hudsonburke/SandsOfTime/Hardware/CAD/Clock/Rack and Pinion Arm/Inside_Channel/Inside_Channel_Acrylic_Assem.SLDASM

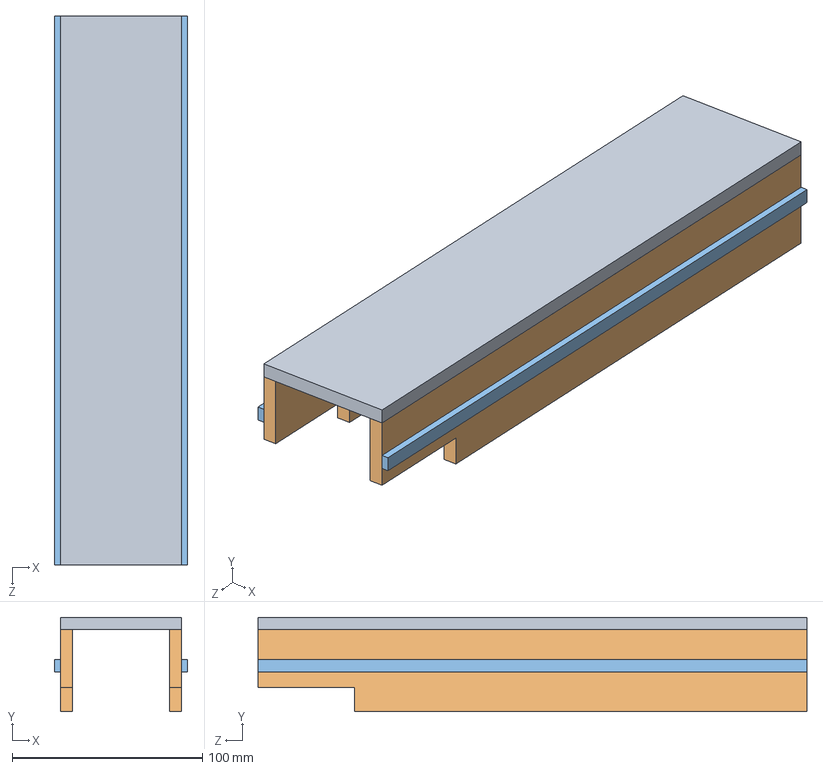
[picture p34: CAD file, 2023-07-05]
Hardware/CAD/Clock/Rack and Pinion Arm/Inside_Channel/Inside_Channel_Acrylic_Assem.SLDASM
69.8 x 49.5 x 288.3 mm
Top
Vert_Outer x 2
Slide x 2
