hudsonburke/SandsOfTime/PriorWork/Solidworks/Solidworks/HG_Assembly/HG_Assembly_4.SLDASM

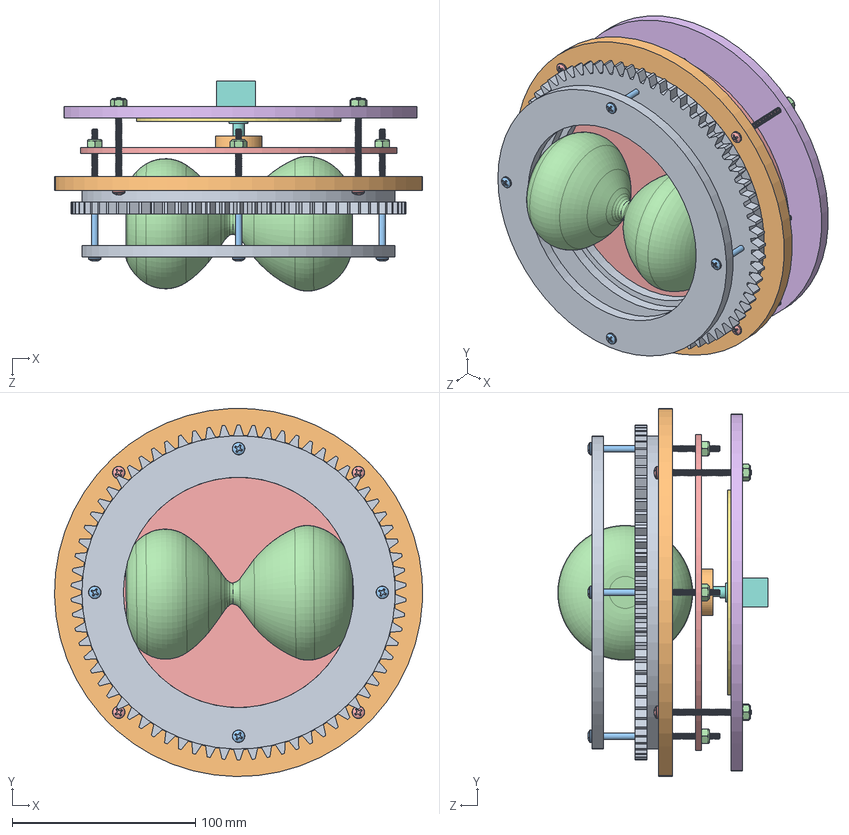
[picture p35: CAD file, 2023-07-05]
PriorWork/Solidworks/Solidworks/HG_Assembly/HG_Assembly_4.SLDASM
200.9 x 200.9 x 114.8 mm
Hourglass_holder_Plate_2 x 2
Outer_Ring_LS
Inner_Ring_LS
Hourglass
Diffuser
Encoder_Plate
LED_ring
Encoder (1)
HG_Gear
Encoder_mount
6_32_2.75_inch x 4
Nylon_Insert_Nut x 8
6_32_2_inch x 4
