hudsonburke/SandsOfTime/Hardware/CAD/Clock/Frame_with_HG_Assembly.SLDASM

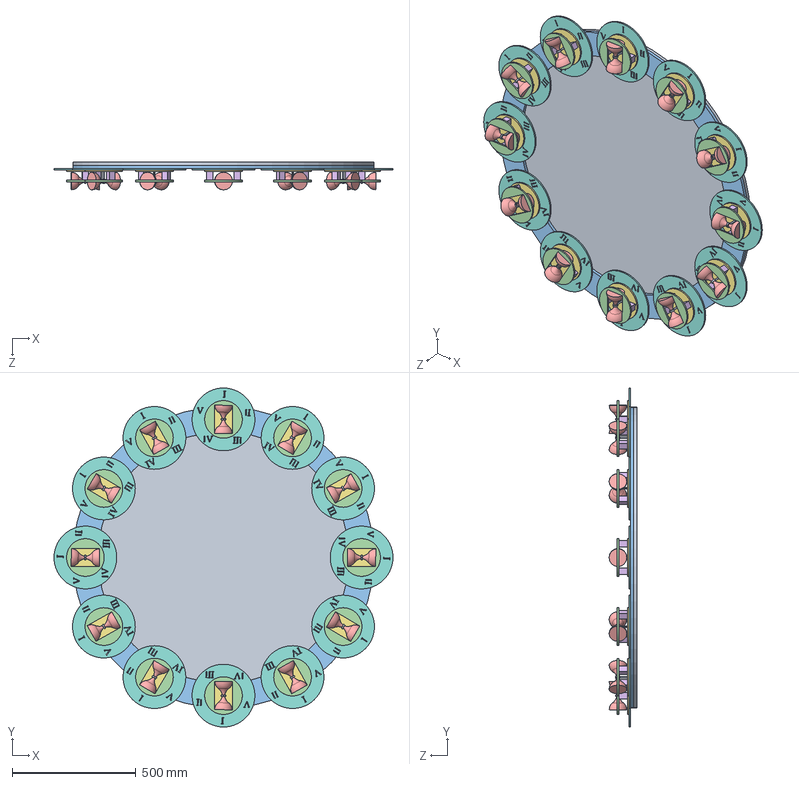
[picture p36: CAD file, 2023-07-05]
Hardware/CAD/Clock/Frame_with_HG_Assembly.SLDASM
1371.6 x 1371.6 x 111.7 mm
Clock_Back
Bearing x 12
Clock_Frame
Hourglass_Plate x 12
Hourglass x 12
Flick_Standoff x 24
Flick_Spacer x 12
Number_Plate x 12
Holder x 24
