hudsonburke/SandsOfTime/Hardware/CAD/Clock/Rack and Pinion Arm/Bearing.SLDASM

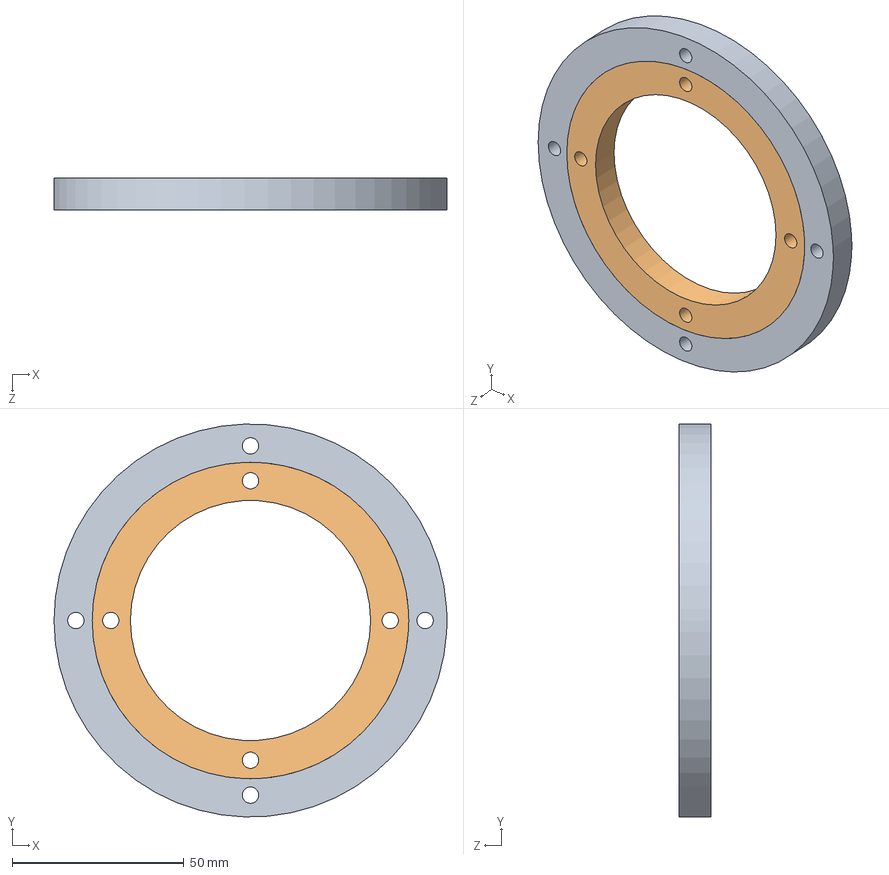
[picture p37: CAD file, 2023-07-05]
Hardware/CAD/Clock/Rack and Pinion Arm/Bearing.SLDASM
114.3 x 114.2 x 9.17 mm
Outside_Ring
Inside_Ring
