hudsonburke/SandsOfTime/Hardware/CAD/Clock/Arm/Arm_Mechanism.SLDASM

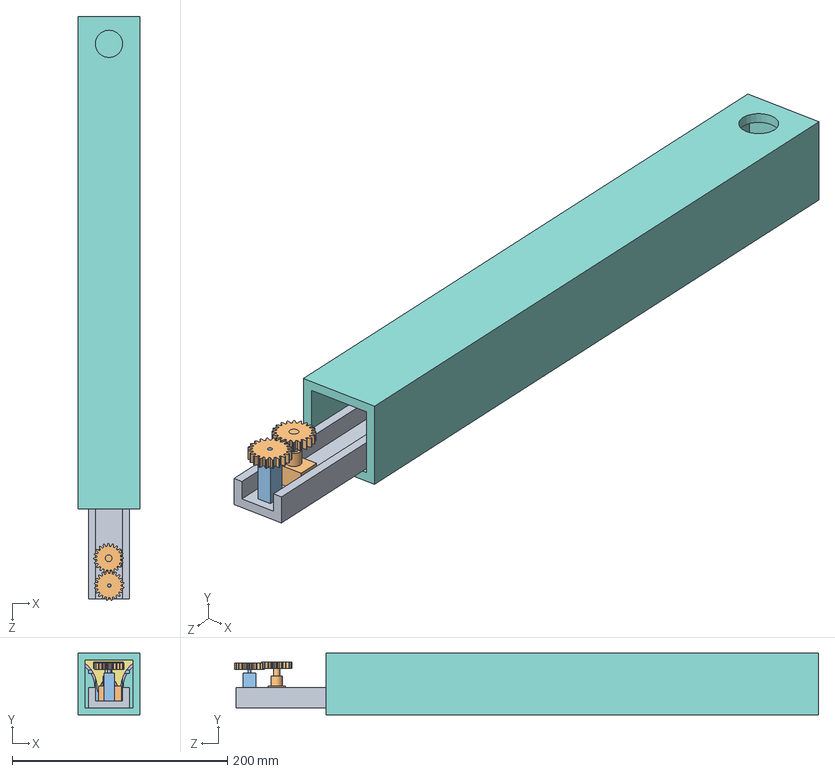
[picture p38: CAD file, 2023-07-05]
Hardware/CAD/Clock/Arm/Arm_Mechanism.SLDASM
57.1 x 57.1 x 542.3 mm
U_Channel
Encoder
Small_Motor
Lead_Nut
Lead_Screw
Bearing_Lead_Screw
Bearing_Holder
Outer Arm
Lead_Screw_Motor
spur gear_ai x 2
Lead_Nut_Holder
Lin_Bearing_Track
Lin_Bearing_Mount
Motor_Holder
