hudsonburke/SandsOfTime/Hardware/CAD/Clock/Open Back/Second_Arm_SubAssembly.SLDASM

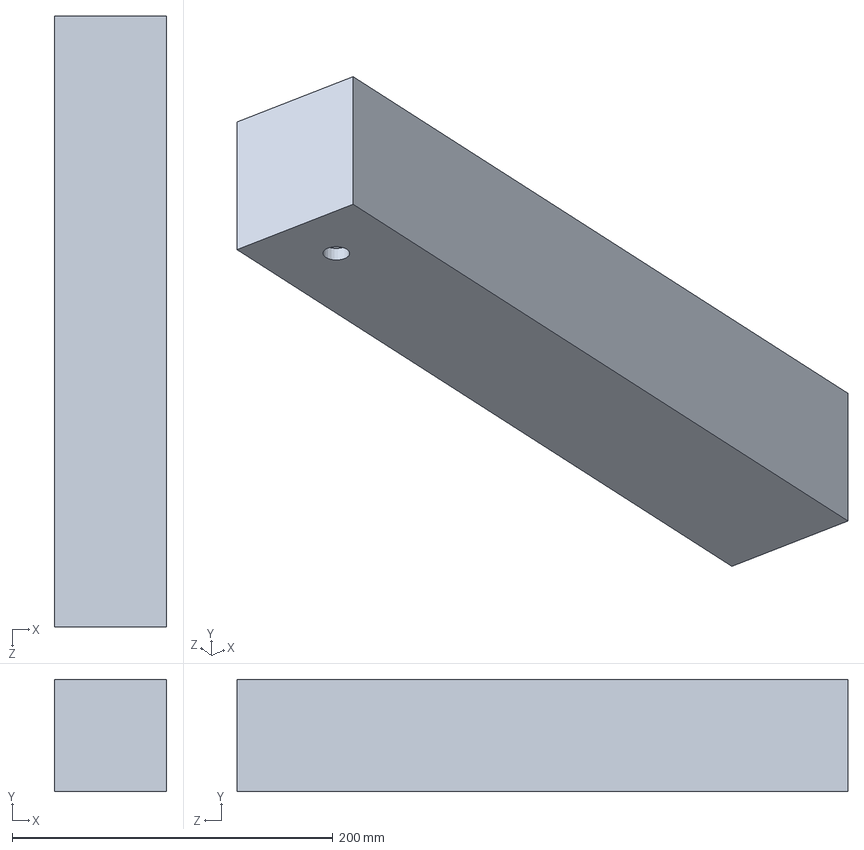
[picture p39: CAD file, 2023-07-05]
Hardware/CAD/Clock/Open Back/Second_Arm_SubAssembly.SLDASM
69.8 x 69.8 x 381.0 mm
Arm1
Linear_Actuator
Arm2
spur gear_ai
