hudsonburke/SandsOfTime/Hardware/CAD/Clock/R and P Arm DC Brush/HG Assembly 10-9/New Version of Assembly 10-9/HG_Assembly_3.SLDASM

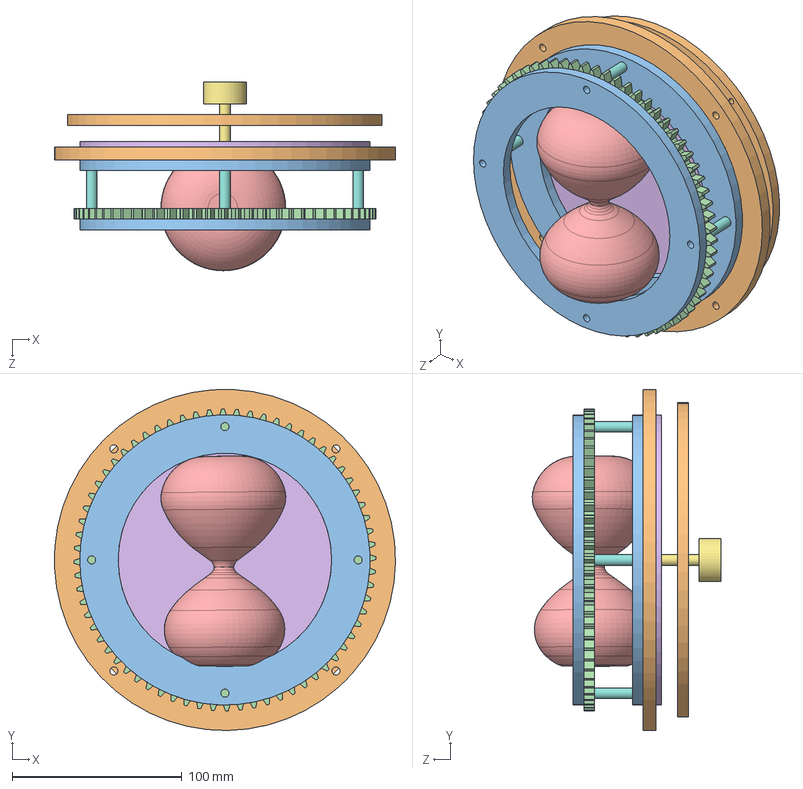
[picture p40: CAD file, 2023-07-05]
Hardware/CAD/Clock/R and P Arm DC Brush/HG Assembly 10-9/New Version of Assembly 10-9/HG_Assembly_3.SLDASM
200.9 x 200.9 x 111.1 mm
Hourglass_Plate_2 x 2
Outer_Ring_LS
Inner_Ring_LS
spur gear_ai
Hourglass
Diffuser
Encoder
Standoff x 4
LED_ring
LED_spacer
