hudsonburke/SandsOfTime/Hardware/CAD/Clock/Rack and Pinion Arm/Inside_Slide.SLDASM

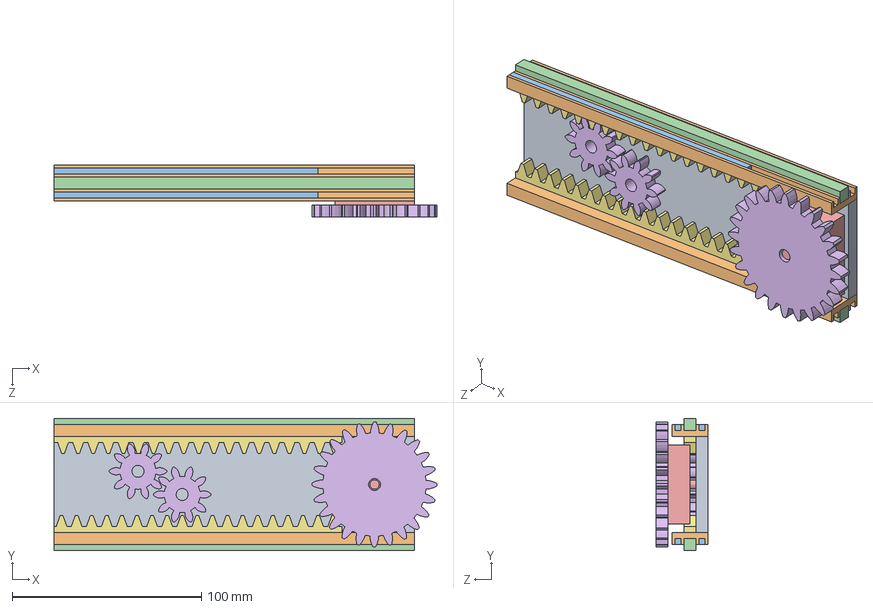
[picture p41: CAD file, 2023-07-05]
Hardware/CAD/Clock/Rack and Pinion Arm/Inside_Slide.SLDASM
202.5 x 69.8 x 27.5 mm
Inside_Bottom_Plate
Inside_Side_Plate x 2
Copper_Insert x 4
Teflon_Insert x 2
Pancake_Motor
spur gear_ai x 3
rack spur rectangular_ai x 2
