hudsonburke/SandsOfTime/Hardware/CAD/Clock/Open Back/Second_Clock_Assembly.SLDASM

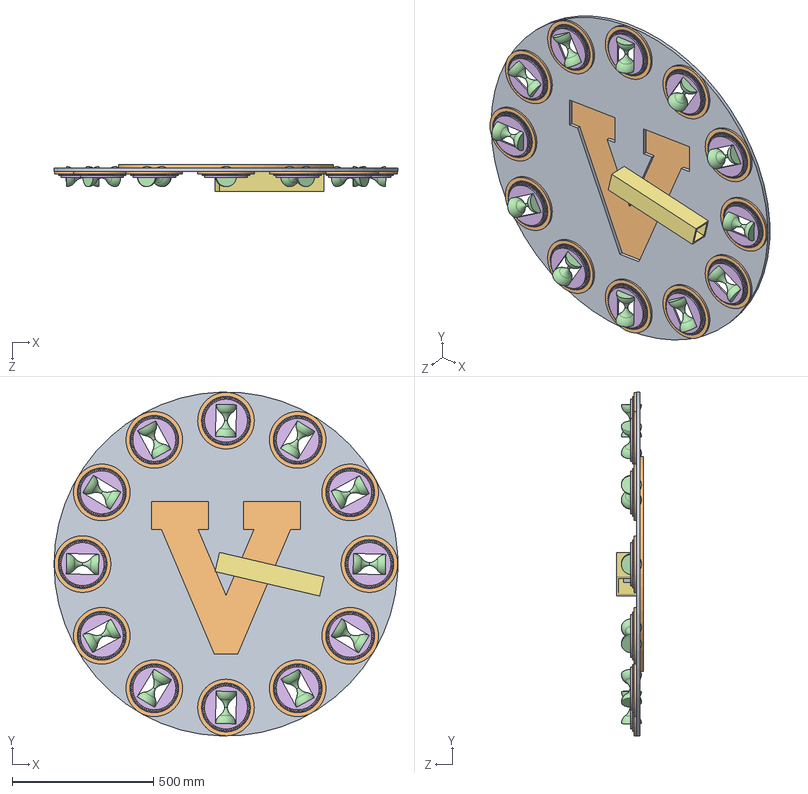
[picture p42: CAD file, 2023-07-05]
Hardware/CAD/Clock/Open Back/Second_Clock_Assembly.SLDASM
1219.2 x 1218.7 x 95.2 mm
Second_BackPlate
Outer_Ring x 12
Inner_Ring x 12
Hourglass x 12
spur gear_ai x 13
Hourglass_Plate x 12
Arm1
Linear_Actuator
Arm2
Back_Plate
