hudsonburke/SandsOfTime/Hardware/CAD/Clock/Hourglass_SubAssem.SLDASM

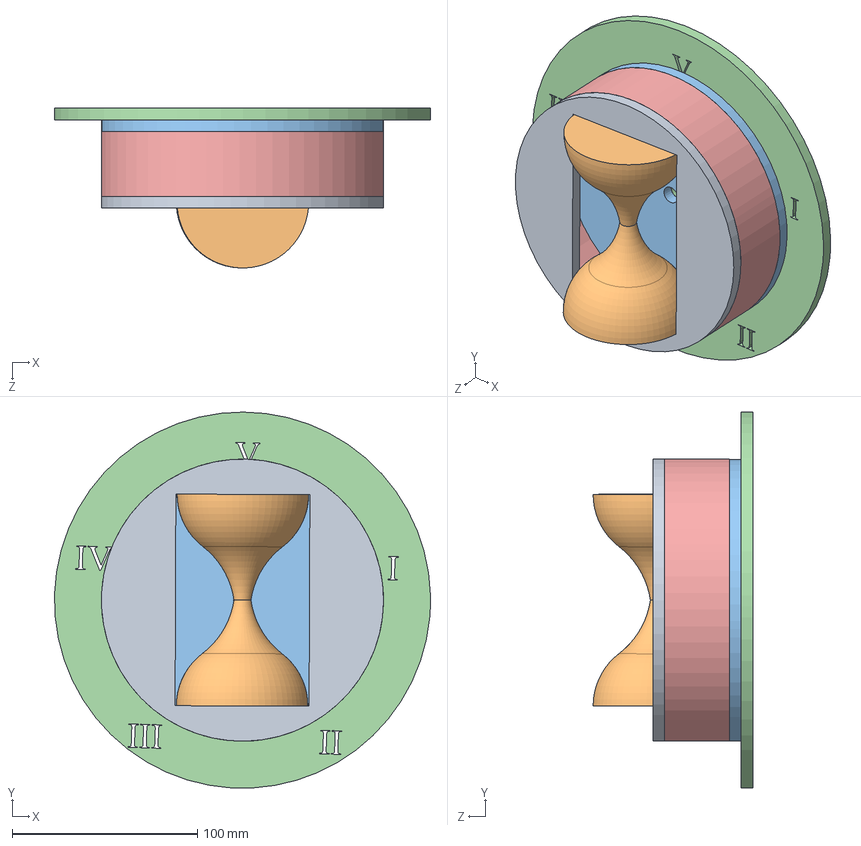
[picture p43: CAD file, 2023-07-05]
Hardware/CAD/Clock/Hourglass_SubAssem.SLDASM
203.1 x 203.0 x 86.3 mm
Hourglass_Plate
Hourglass
Flick_Spacer
Number_Plate
PVC_ring
