hudsonburke/SandsOfTime/Hardware/CAD/Clock/HG_Assembly_3.SLDASM

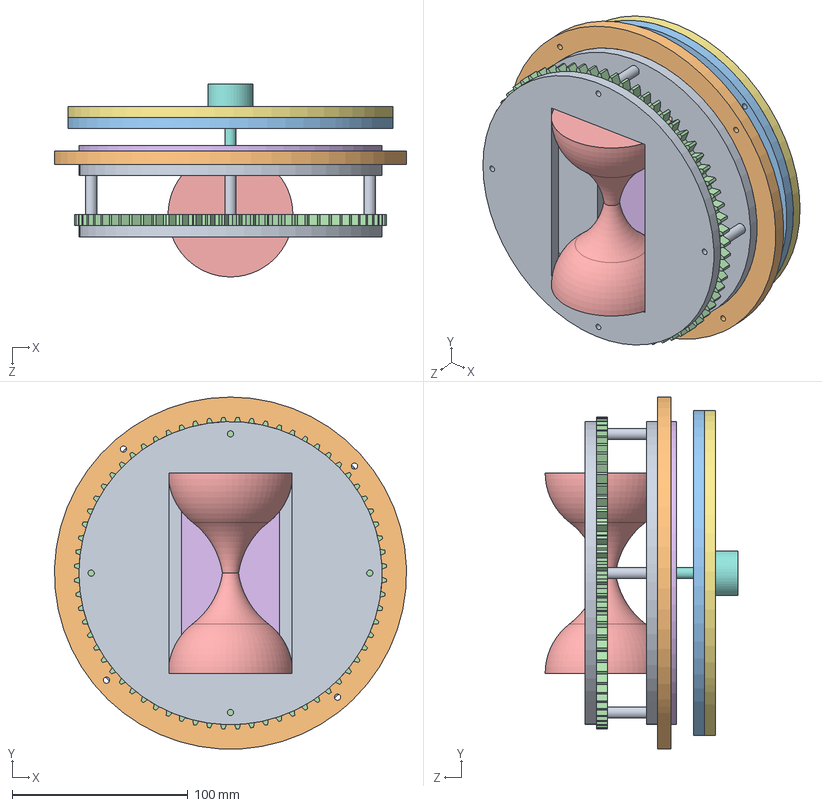
[picture p44: CAD file, 2023-07-05]
Hardware/CAD/Clock/HG_Assembly_3.SLDASM
200.6 x 200.5 x 109.8 mm
Hourglass_Plate_2 x 2
Outer_Ring
Inner_Ring
spur gear_ai
Hourglass
Diffuser
Back_Plate
Encoder
Standoff x 4
LED_ring
LED_spacer
