hudsonburke/SandsOfTime/Hardware/CAD/Clock/Clock_Assembly_4.SLDASM

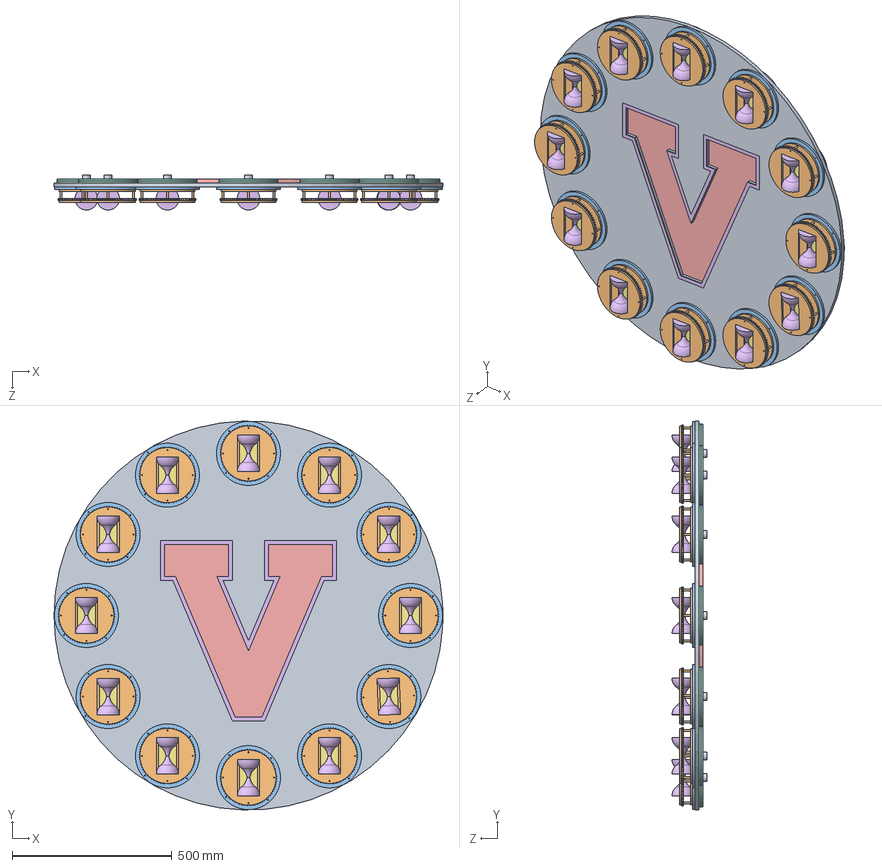
[picture p45: CAD file, 2023-07-05]
Hardware/CAD/Clock/Clock_Assembly_4.SLDASM
1219.2 x 1218.7 x 109.8 mm
Second_BackPlate
Hourglass_Plate_2 x 24
Outer_Ring x 12
Inner_Ring x 12
spur gear_ai x 12
Hourglass x 12
Diffuser x 12
Back_Plate x 12
Encoder x 12
Standoff x 48
LED_ring x 12
LED_spacer x 12
Back_Plate1
Alum_V
