hudsonburke/SandsOfTime/Hardware/CAD/Clock/Frame_Assembly.SLDASM

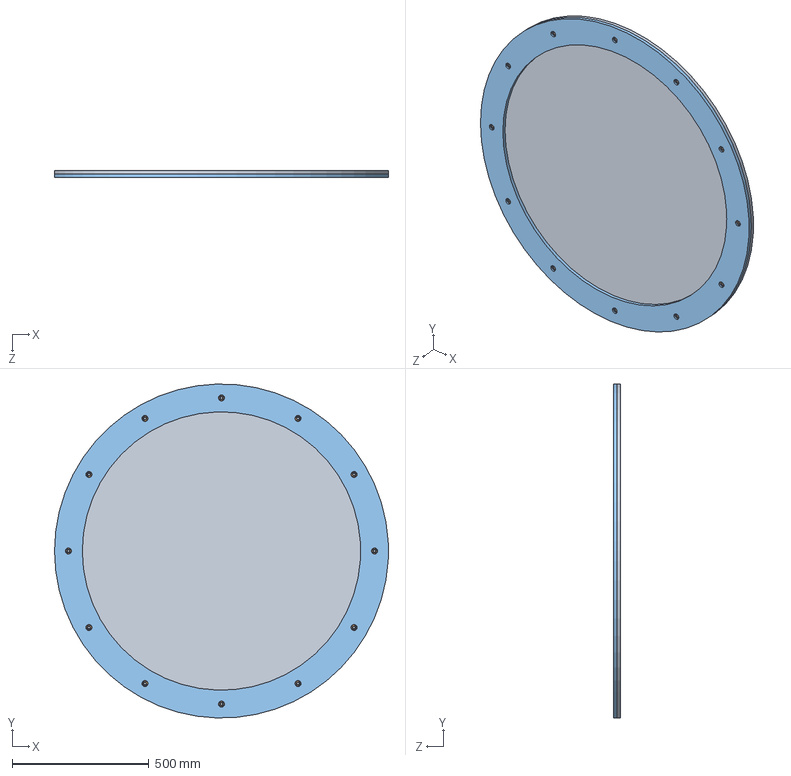
[picture p46: CAD file, 2023-07-05]
Hardware/CAD/Clock/Frame_Assembly.SLDASM
1219.2 x 1218.7 x 25.4 mm
Clock_Back
Bearing x 12
Clock_Frame
