hudsonburke/SandsOfTime/Hardware/CAD/Clock/R and P Arm DC Brush/Arm_Rotation_Assem.SLDASM

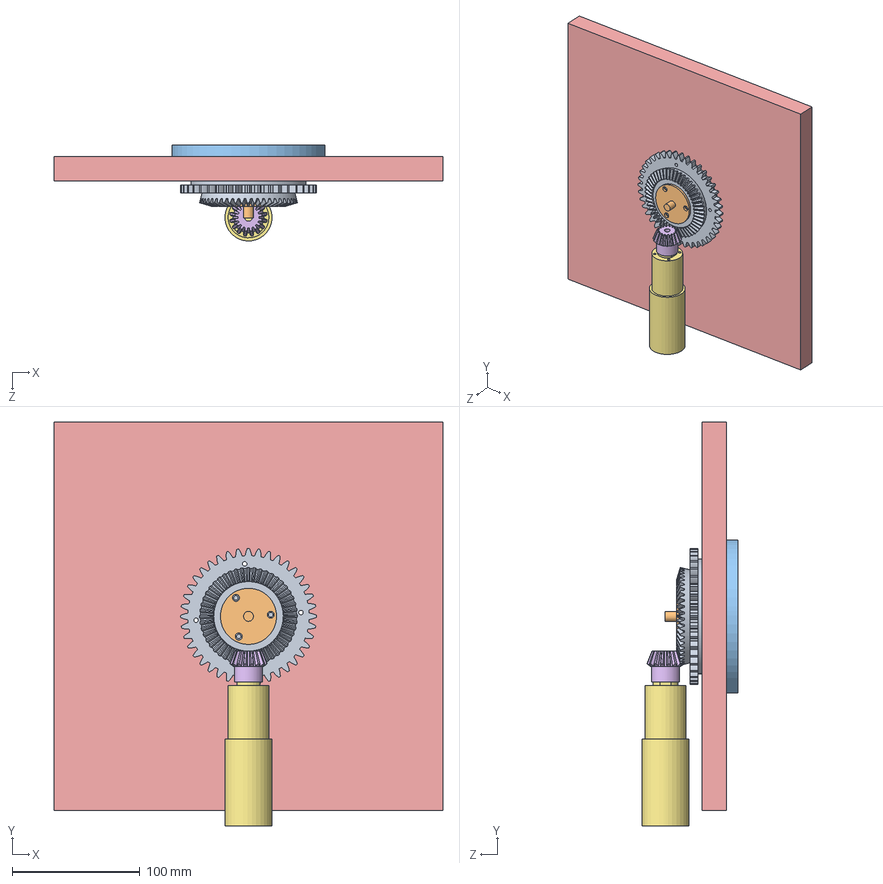
[picture p47: CAD file, 2023-07-05]
Hardware/CAD/Clock/R and P Arm DC Brush/Arm_Rotation_Assem.SLDASM
304.8 x 316.8 x 75.3 mm
Master_Center_Gear
Slip_Ring
Outside_Ring
Inside_Ring
Dummy_Backplate
Bevel_Gear_Motor
Drive_Motor
