hudsonburke/SandsOfTime/Hardware/CAD/Clock/R and P Arm DC Brush/Master_Drive_Gear.SLDASM

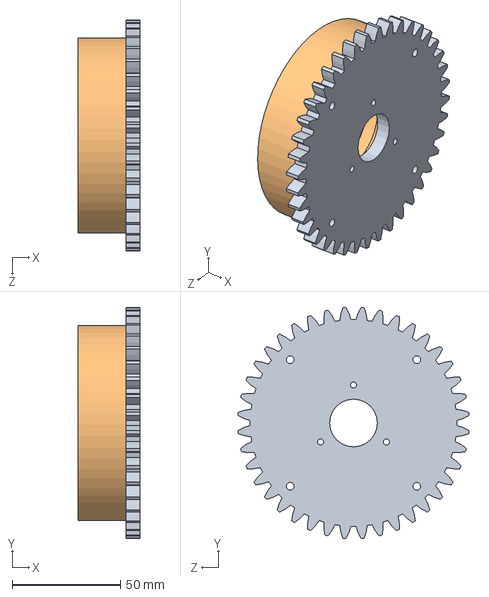
[picture p48: CAD file, 2023-07-05]
Hardware/CAD/Clock/R and P Arm DC Brush/Master_Drive_Gear.SLDASM
28.6 x 106.5 x 106.5 mm
Spur_Gear_Drive_Motor
Arm_Cup_Attachment
