hudsonburke/SandsOfTime/Hardware/CAD/Clock/Rack and Pinion Arm/Graphite_Brush.SLDASM

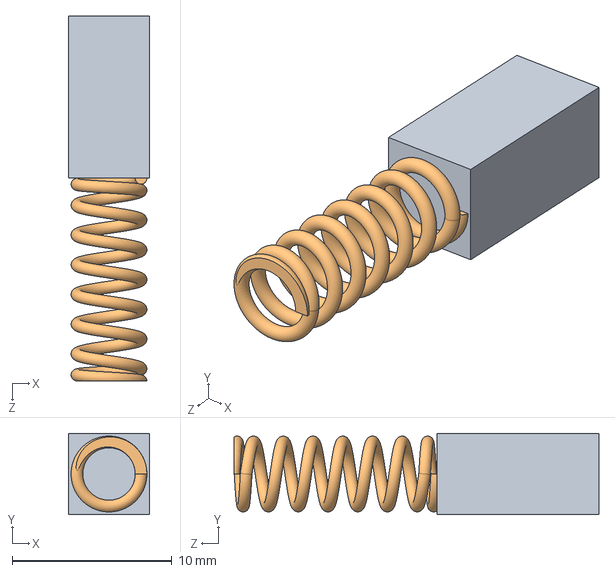
[picture p49: CAD file, 2023-07-05]
Hardware/CAD/Clock/Rack and Pinion Arm/Graphite_Brush.SLDASM
5.08 x 5.08 x 22.9 mm
Graphite
Graphite_Spring
