hudsonburke/SandsOfTime/Hardware/CAD/Clock/Arm/Lin_Bearing_Track.SLDPRT

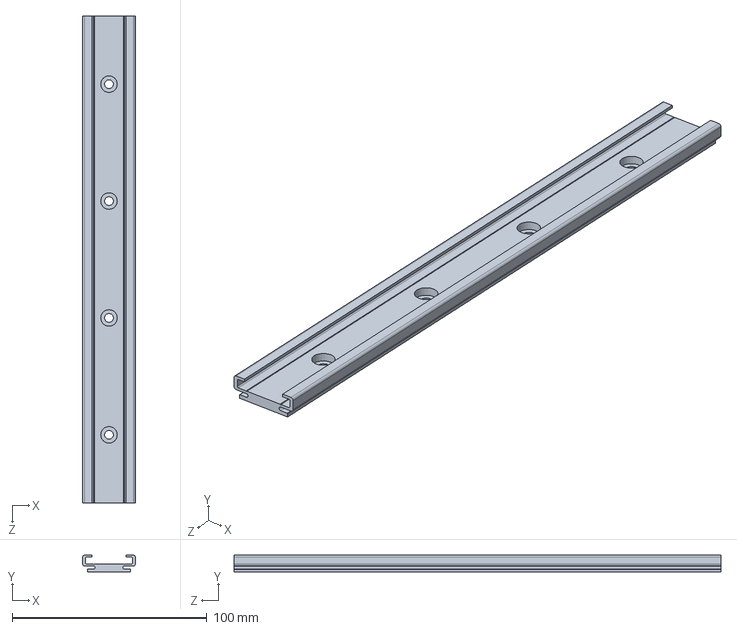
[picture p50: CAD file, 2023-07-05]
Hardware/CAD/Clock/Arm/Lin_Bearing_Track.SLDPRT
27.0 x 8.70 x 250.0 mm
