hudsonburke/SandsOfTime/Hardware/CAD/Clock/Open Back/Inner_Ring.SLDPRT

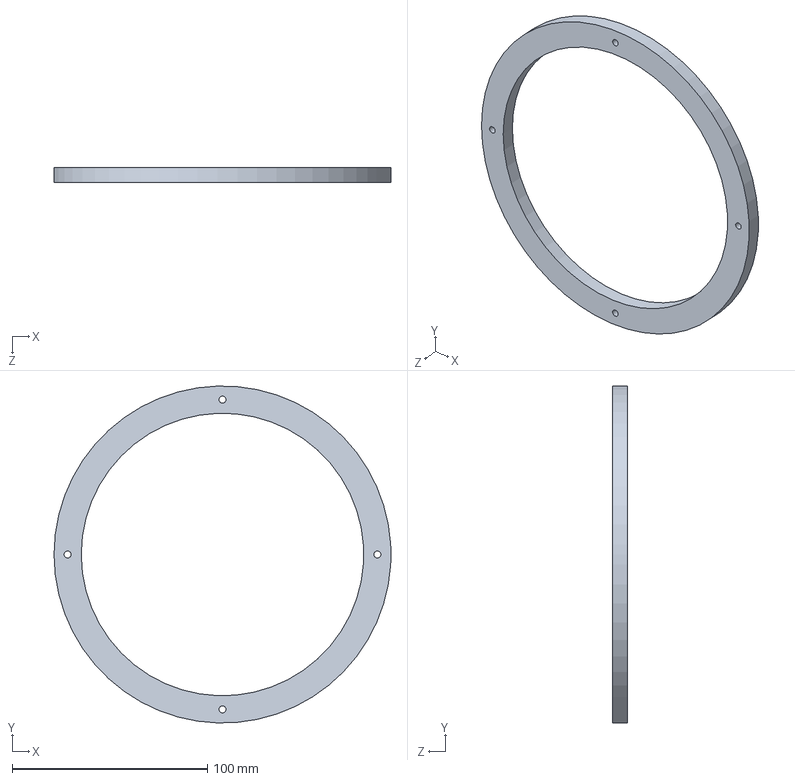
[picture p51: CAD file, 2023-07-05]
Hardware/CAD/Clock/Open Back/Inner_Ring.SLDPRT
172.7 x 172.6 x 7.62 mm
