hudsonburke/SandsOfTime/Hardware/CAD/Clock/R and P Arm DC Brush/HG Assembly 10-9/New Version of Assembly 10-9/Hourglass.SLDPRT

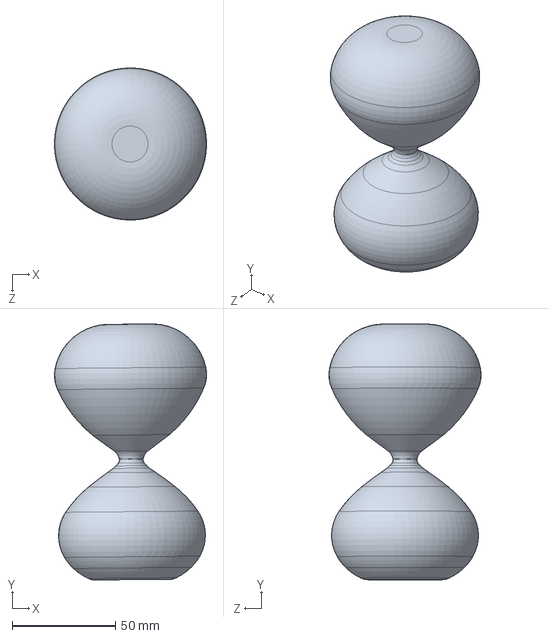
[picture p52: CAD file, 2026-04-15]
Hardware/CAD/Clock/R and P Arm DC Brush/HG Assembly 10-9/New Version of Assembly 10-9/Hourglass.SLDPRT
73.6 x 123.9 x 73.6 mm
