hudsonburke/SandsOfTime/Hardware/CAD/Clock/R and P Arm DC Brush/Inner_Channel/Bearing_Side.SLDPRT

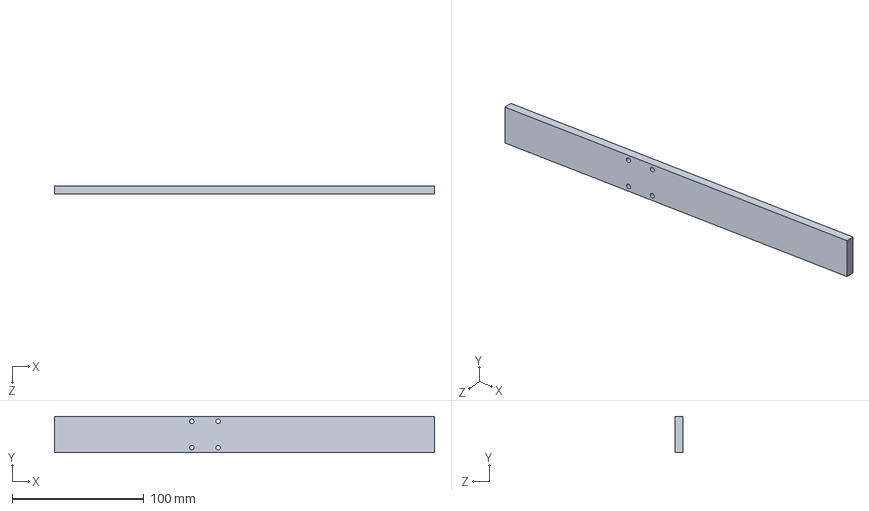
[picture p53: CAD file, 2023-07-05]
Hardware/CAD/Clock/R and P Arm DC Brush/Inner_Channel/Bearing_Side.SLDPRT
288.3 x 27.5 x 6.35 mm
