hudsonburke/SandsOfTime/Hardware/CAD/Clock/R and P Arm DC Brush/Outer_Channel/Left_Side.SLDPRT

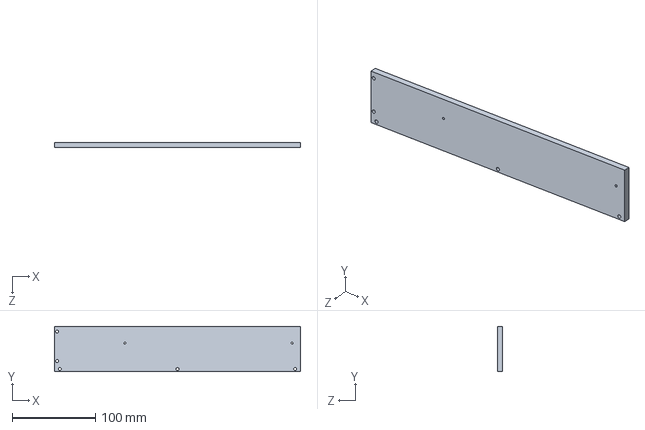
[picture p54: CAD file, 2023-07-05]
Hardware/CAD/Clock/R and P Arm DC Brush/Outer_Channel/Left_Side.SLDPRT
294.6 x 54.3 x 6.35 mm
