hudsonburke/SandsOfTime/Hardware/CAD/Clock/Rack and Pinion Arm/Bottom_Channel/Bottom.SLDPRT

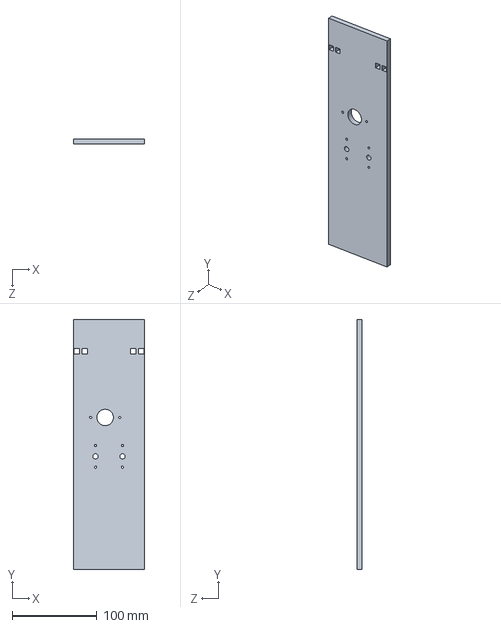
[picture p55: CAD file, 2023-07-05]
Hardware/CAD/Clock/Rack and Pinion Arm/Bottom_Channel/Bottom.SLDPRT
83.5 x 294.6 x 6.35 mm
