hudsonburke/SandsOfTime/Hardware/CAD/Clock/Rack and Pinion Arm/Inside_Channel/Sidewall.SLDPRT

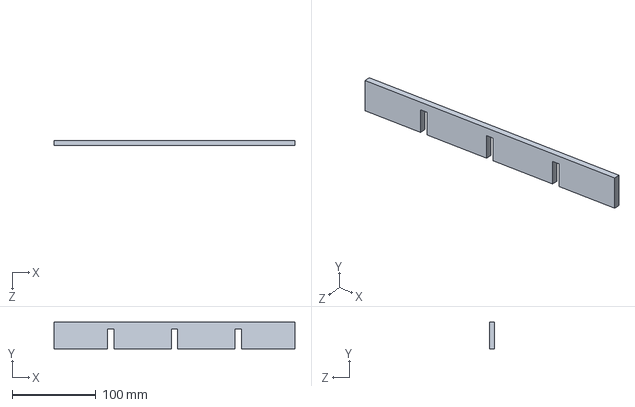
[picture p56: CAD file, 2023-07-05]
Hardware/CAD/Clock/Rack and Pinion Arm/Inside_Channel/Sidewall.SLDPRT
288.3 x 31.8 x 6.35 mm
