hudsonburke/SandsOfTime/PriorWork/MerrickBackup/Blocks/Inner Channel/L.SLDPRT

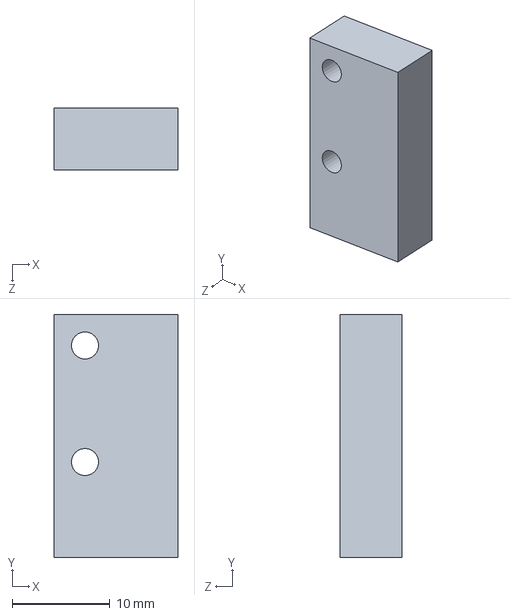
[picture p57: CAD file, 2023-07-05]
PriorWork/MerrickBackup/Blocks/Inner Channel/L.SLDPRT
12.7 x 24.9 x 6.35 mm
