hudsonburke/SandsOfTime/PriorWork/MerrickBackup/DXFs/Encoder_mount.DXF

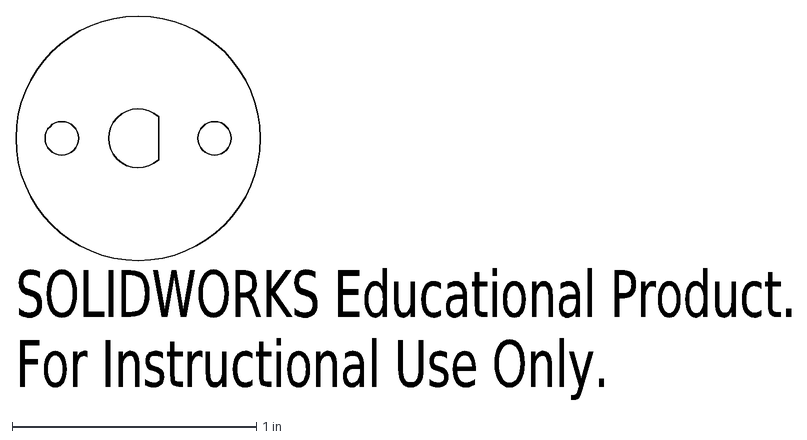
[picture p58: CAD file, 2023-07-05]
PriorWork/MerrickBackup/DXFs/Encoder_mount.DXF
SOLIDWORKS Educational Product.
For Instructional Use Only.
