hudsonburke/SandsOfTime/PriorWork/MerrickBackup/DXFs/Inner_Arm/Bottom_IC.DXF

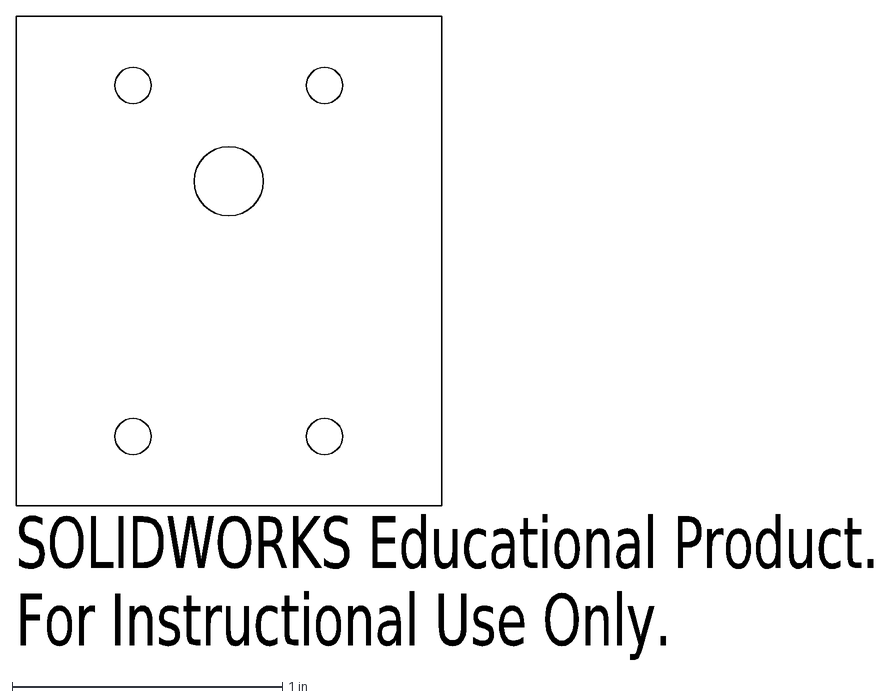
[picture p59: CAD file, 2023-07-05]
PriorWork/MerrickBackup/DXFs/Inner_Arm/Bottom_IC.DXF
SOLIDWORKS Educational Product.
For Instructional Use Only.
