hudsonburke/SandsOfTime/PriorWork/MerrickBackup/DXFs/Outer_Arm/Bottom_OC.SLDPRT

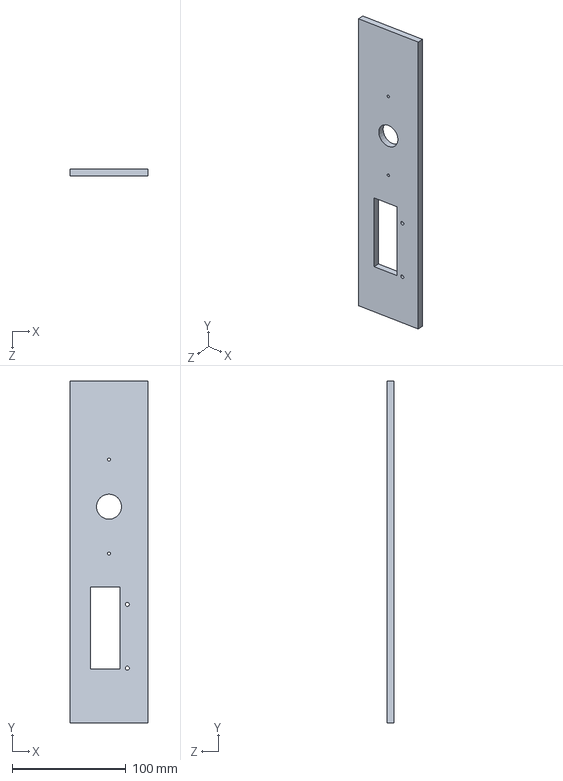
[picture p60: CAD file, 2023-07-05]
PriorWork/MerrickBackup/DXFs/Outer_Arm/Bottom_OC.SLDPRT
68.7 x 300.2 x 6.35 mm
