hudsonburke/SandsOfTime/PriorWork/MerrickBackup/Solidworks/Clock/Spacer.SLDPRT

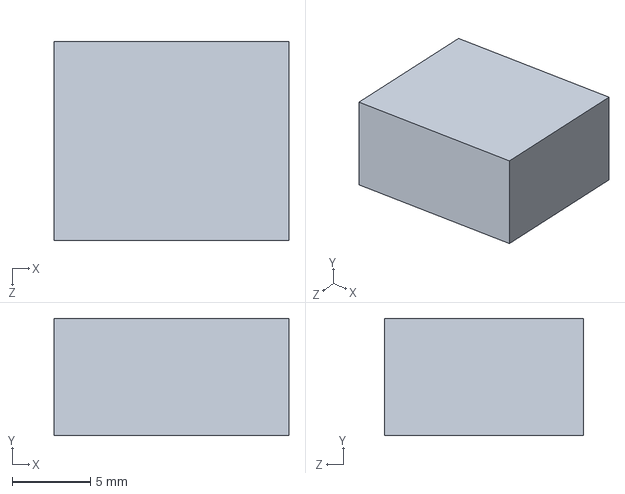
[picture p61: CAD file, 2023-07-05]
PriorWork/MerrickBackup/Solidworks/Clock/Spacer.SLDPRT
15.0 x 7.50 x 12.7 mm
