hudsonburke/SandsOfTime/PriorWork/MerrickBackup/Solidworks/HG_Assembly/6_32_2.75_inch.SLDPRT

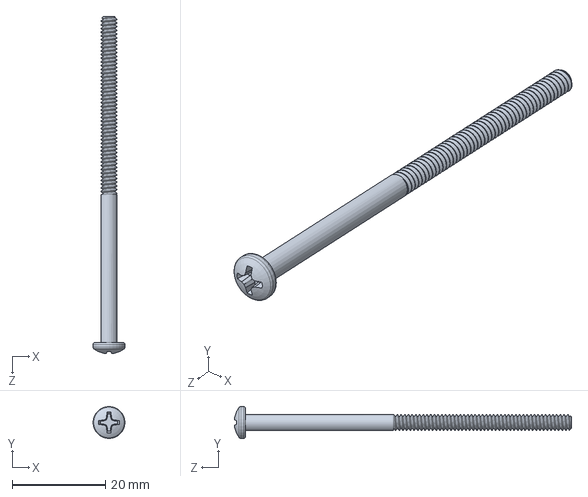
[picture p62: CAD file, 2023-07-05]
PriorWork/MerrickBackup/Solidworks/HG_Assembly/6_32_2.75_inch.SLDPRT
6.86 x 6.86 x 72.2 mm
