hudsonburke/SandsOfTime/PriorWork/MerrickBackup/WaterJet/Furman_Capstone_Arm_Gear.dxf

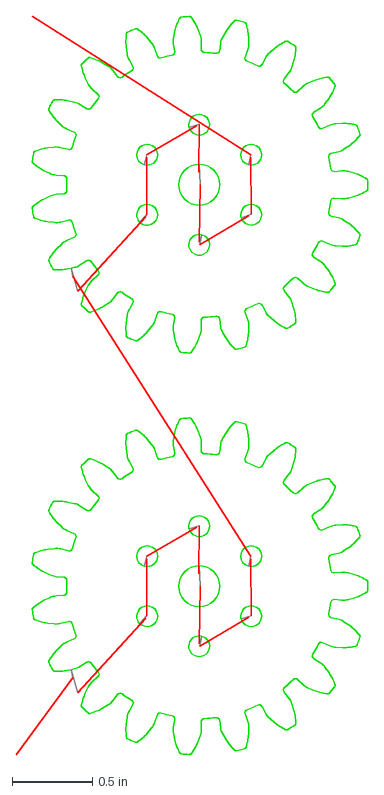
[picture p63: CAD file, 2023-07-05]
PriorWork/MerrickBackup/WaterJet/Furman_Capstone_Arm_Gear.dxf
2.19 x 4.60 in
