hudsonburke/SandsOfTime/PriorWork/Solidworks/Solidworks/HG_Assembly/Encoder (1).SLDPRT

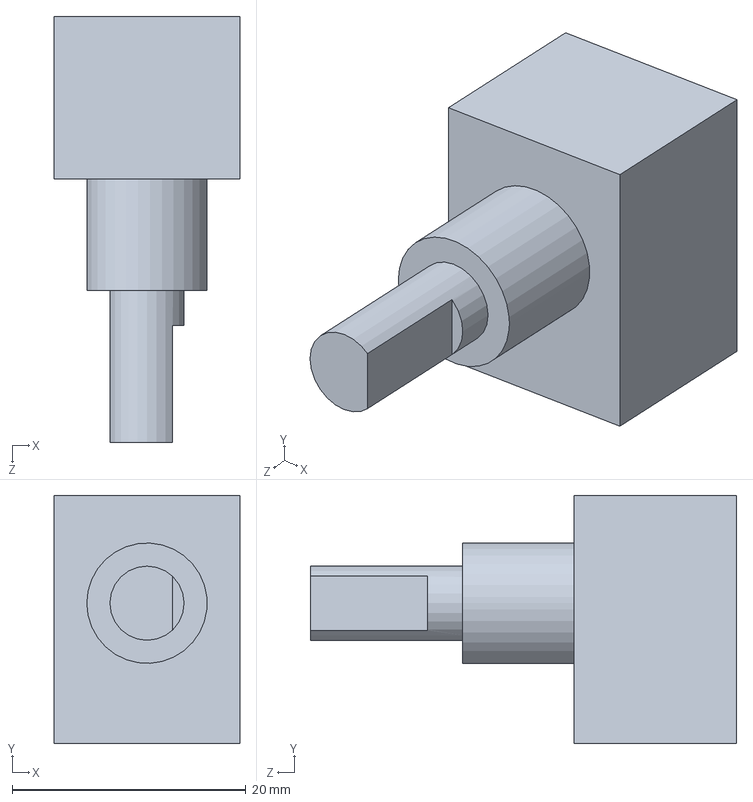
[picture p64: CAD file, 2023-07-05]
PriorWork/Solidworks/Solidworks/HG_Assembly/Encoder (1).SLDPRT
15.9 x 21.2 x 36.4 mm
