hudsonburke/SandsOfTime/Hardware/CAD/Clock/Arm/Lin_Bearing_Mount.SLDPRT

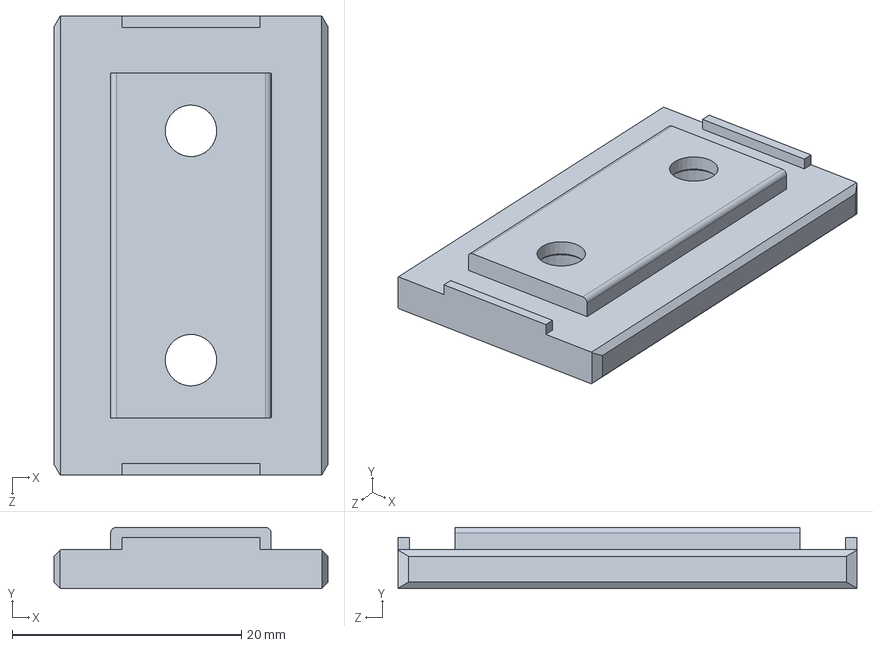
[picture p65: CAD file, 2023-07-05]
Hardware/CAD/Clock/Arm/Lin_Bearing_Mount.SLDPRT
23.9 x 5.35 x 40.0 mm
