hudsonburke/SandsOfTime/Hardware/CAD/Clock/Open Back/Alum_V.SLDPRT

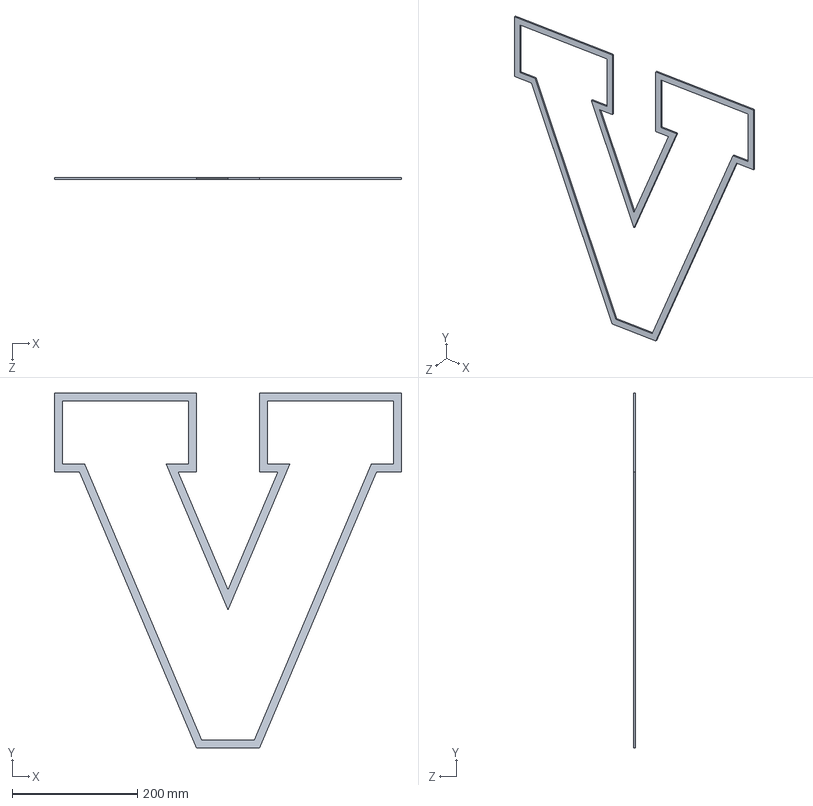
[picture p66: CAD file, 2023-07-05]
Hardware/CAD/Clock/Open Back/Alum_V.SLDPRT
553.0 x 565.5 x 3.17 mm
