hudsonburke/SandsOfTime/Hardware/CAD/Clock/Rack and Pinion Arm/Bottom_Channel/Back.SLDPRT

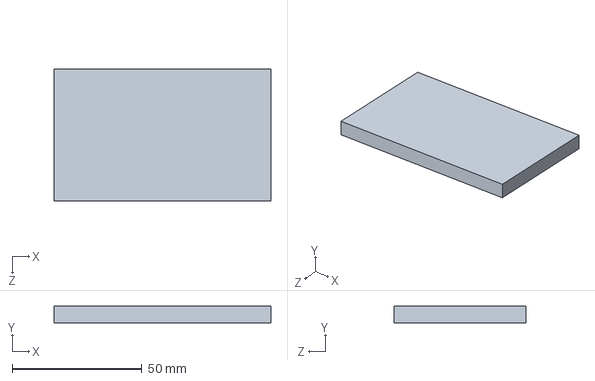
[picture p67: CAD file, 2023-07-05]
Hardware/CAD/Clock/Rack and Pinion Arm/Bottom_Channel/Back.SLDPRT
83.5 x 6.35 x 50.8 mm
