hudsonburke/SandsOfTime/Hardware/CAD/Clock/Rack and Pinion Arm/Inside_Channel/Vert_Outer.SLDPRT

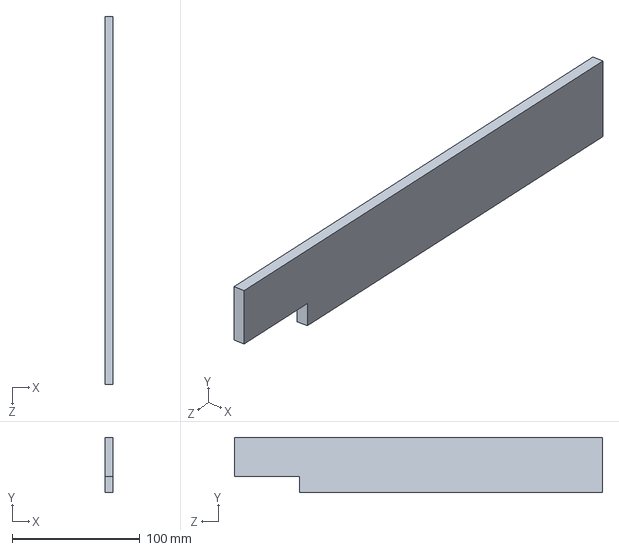
[picture p68: CAD file, 2023-07-05]
Hardware/CAD/Clock/Rack and Pinion Arm/Inside_Channel/Vert_Outer.SLDPRT
6.35 x 43.2 x 288.3 mm
