hudsonburke/SandsOfTime/PriorWork/MerrickBackup/Blocks/Inner Channel/Top_IC.SLDPRT

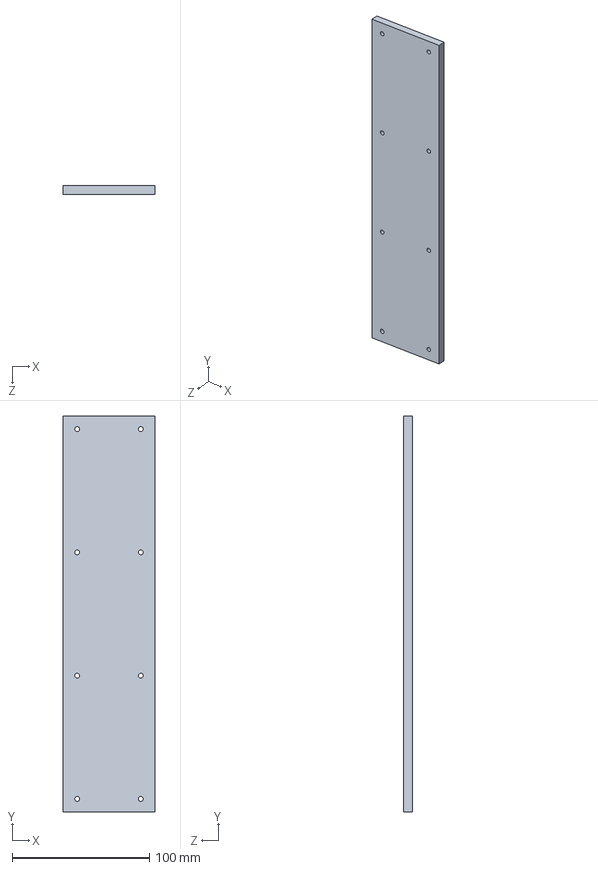
[picture p69: CAD file, 2023-07-05]
PriorWork/MerrickBackup/Blocks/Inner Channel/Top_IC.SLDPRT
66.7 x 288.3 x 6.35 mm
