hudsonburke/SandsOfTime/PriorWork/MerrickBackup/DXFs/Arm_Gear.DXF

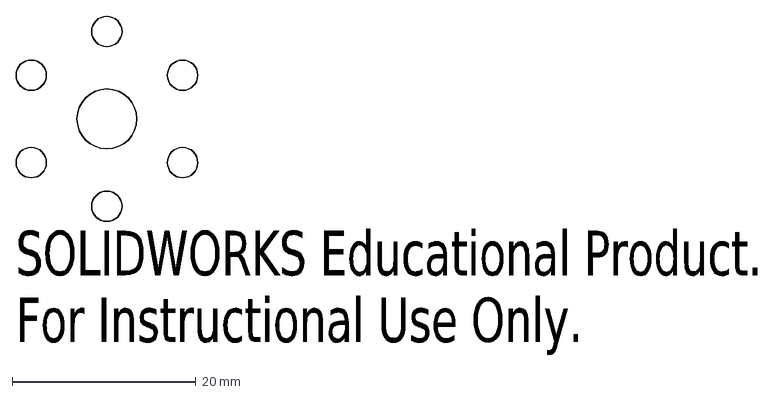
[picture p70: CAD file, 2023-07-05]
PriorWork/MerrickBackup/DXFs/Arm_Gear.DXF
SOLIDWORKS Educational Product.
For Instructional Use Only.
