hudsonburke/SandsOfTime/PriorWork/MerrickBackup/Solidworks/Clock/Wood_V_insert.SLDPRT

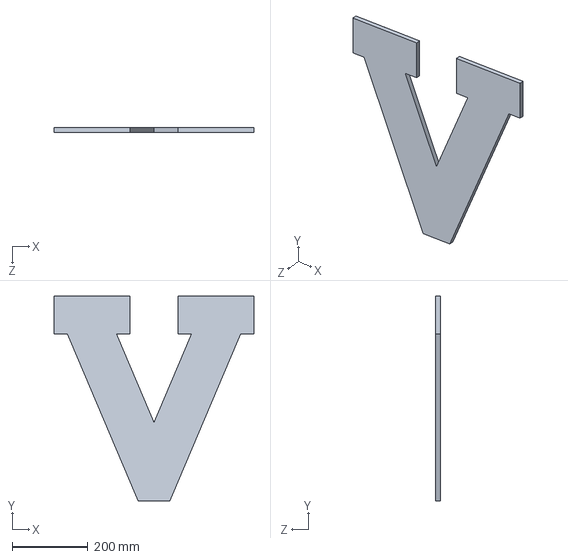
[picture p72: CAD file, 2023-07-05]
PriorWork/MerrickBackup/Solidworks/Clock/Wood_V_insert.SLDPRT
527.6 x 540.1 x 12.7 mm
