hudsonburke/SandsOfTime/PriorWork/MerrickBackup/Solidworks/HG_Assembly/Outer_Ring_LS.SLDPRT

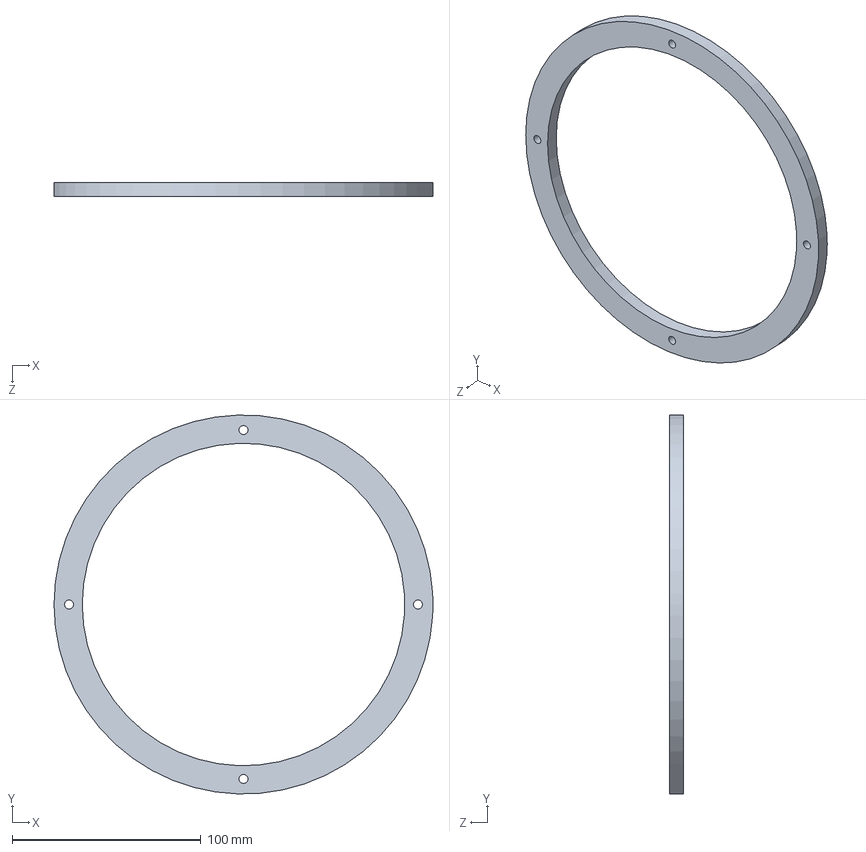
[picture p73: CAD file, 2023-07-05]
PriorWork/MerrickBackup/Solidworks/HG_Assembly/Outer_Ring_LS.SLDPRT
201.0 x 200.9 x 7.62 mm
