hudsonburke/SandsOfTime/PriorWork/Solidworks/Solidworks/Clock/SandClockExtendArm.SLDPRT

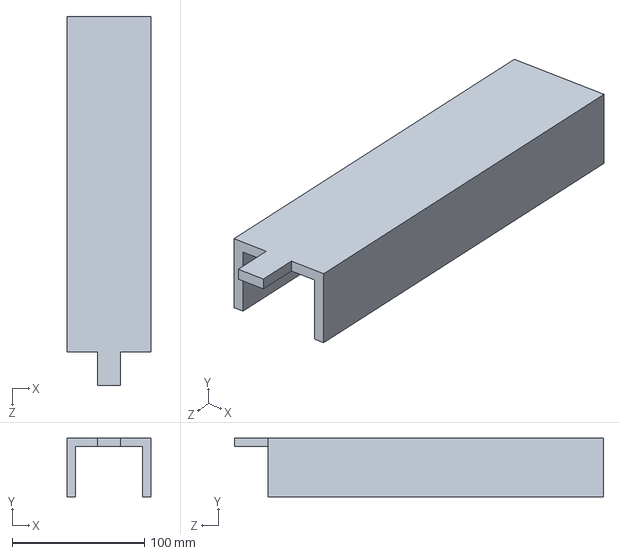
[picture p74: CAD file, 2023-07-05]
PriorWork/Solidworks/Solidworks/Clock/SandClockExtendArm.SLDPRT
63.5 x 44.5 x 279.4 mm
