hudsonburke/SandsOfTime/PriorWork/Solidworks/Solidworks/HG_Assembly/Inner_Ring_LS.SLDPRT

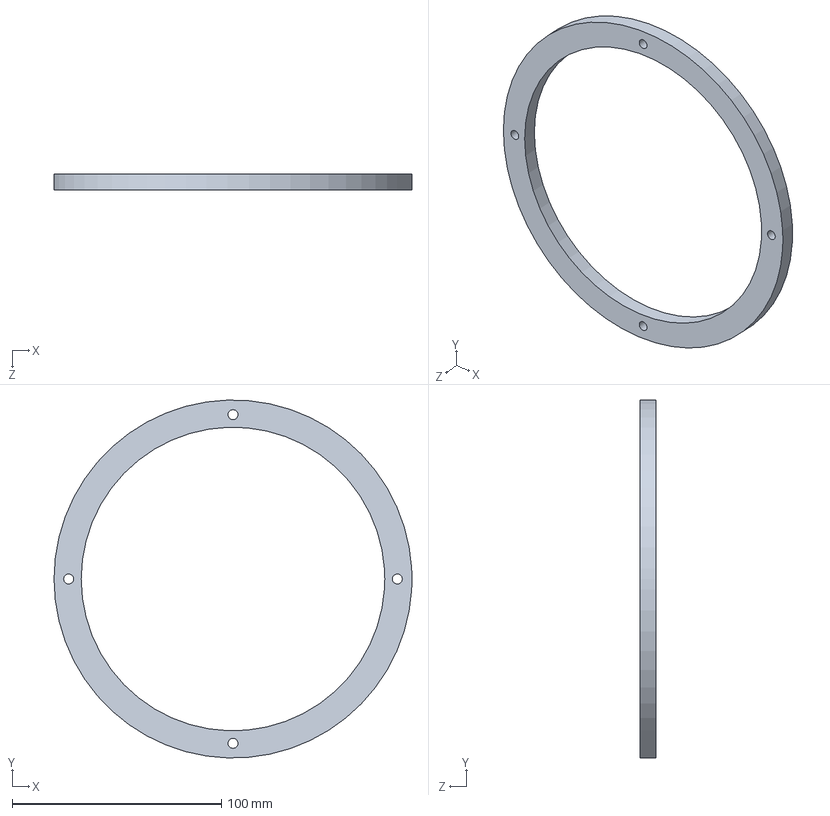
[picture p75: CAD file, 2023-07-05]
PriorWork/Solidworks/Solidworks/HG_Assembly/Inner_Ring_LS.SLDPRT
171.0 x 170.9 x 7.62 mm
