hudsonburke/SandsOfTime/Hardware/CAD/Clock/Arm/Encoder_Connector.SLDPRT

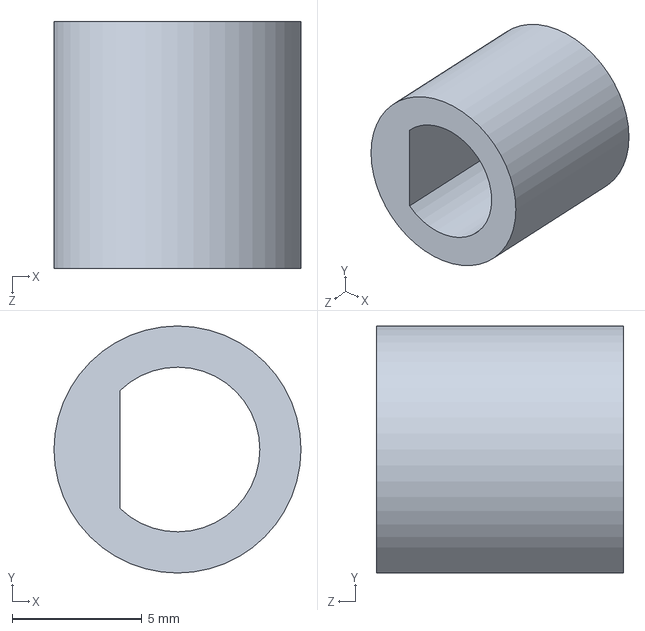
[picture p76: CAD file, 2023-07-05]
Hardware/CAD/Clock/Arm/Encoder_Connector.SLDPRT
9.53 x 9.53 x 9.53 mm
