hudsonburke/SandsOfTime/Hardware/CAD/Clock/CNC Backplate/Face_Ring.SLDPRT

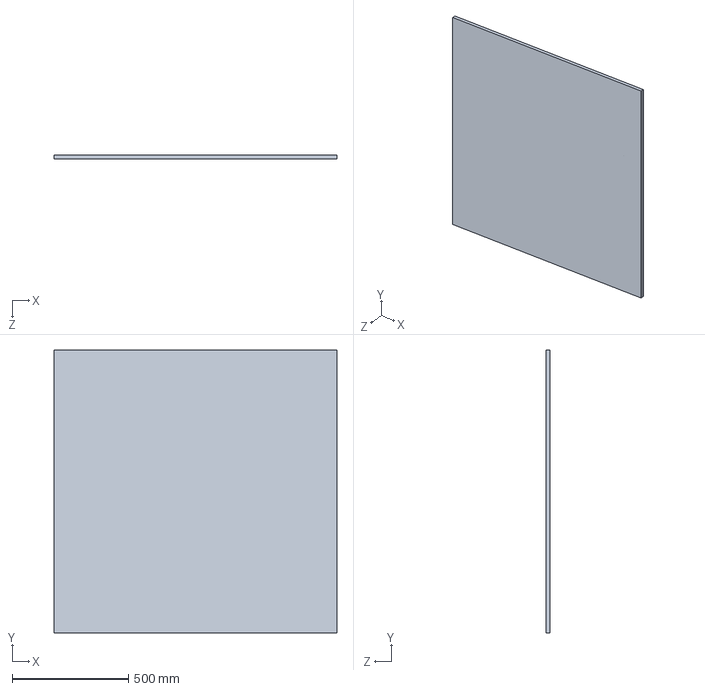
[picture p77: CAD file, 2023-07-05]
Hardware/CAD/Clock/CNC Backplate/Face_Ring.SLDPRT
1219.2 x 1219.2 x 19.1 mm
