hudsonburke/SandsOfTime/Hardware/CAD/Clock/Holder.SLDPRT

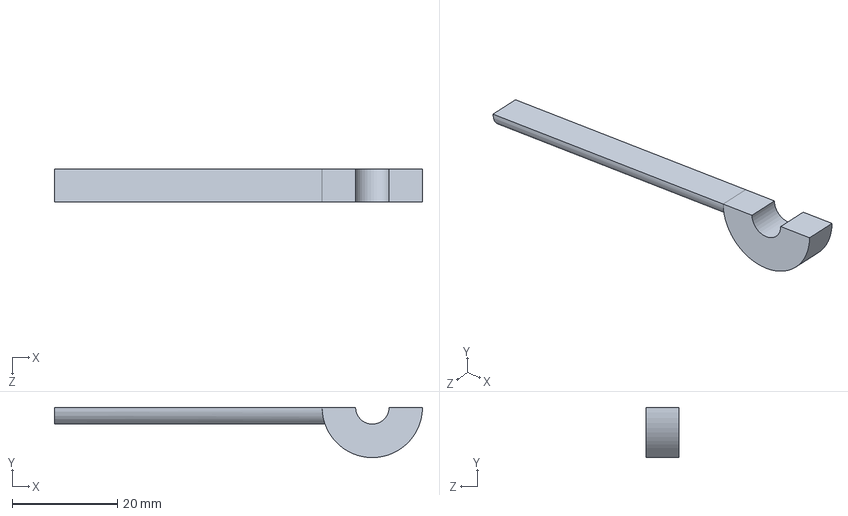
[picture p78: CAD file, 2023-07-05]
Hardware/CAD/Clock/Holder.SLDPRT
69.8 x 9.53 x 6.35 mm
