hudsonburke/SandsOfTime/Hardware/CAD/Clock/Open Back/Arm1.SLDPRT

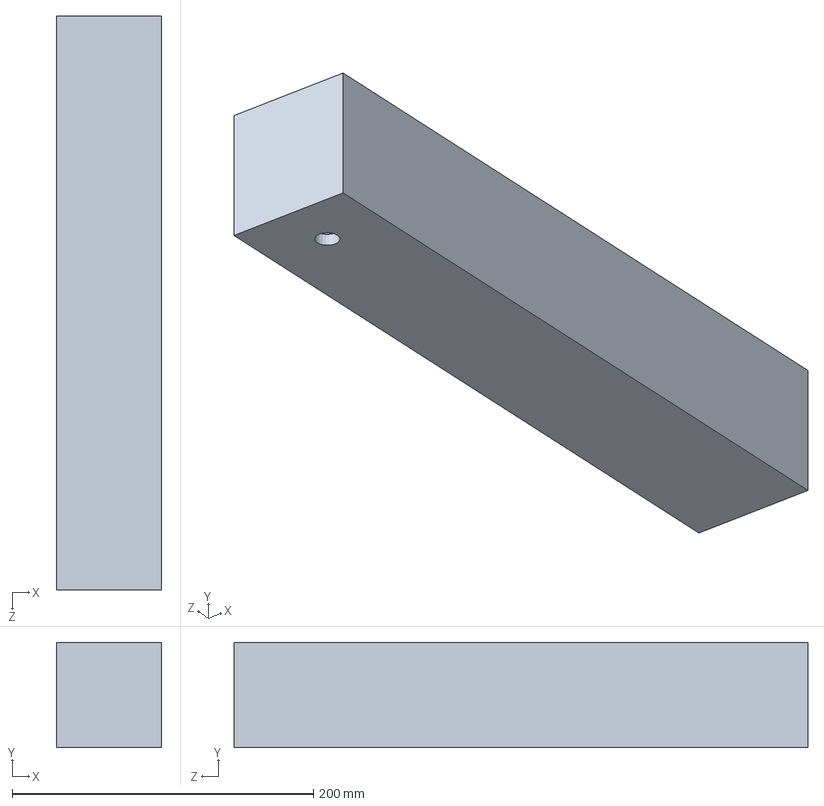
[picture p79: CAD file, 2023-07-05]
Hardware/CAD/Clock/Open Back/Arm1.SLDPRT
69.8 x 69.8 x 381.0 mm
