hudsonburke/SandsOfTime/Hardware/CAD/Clock/R and P Arm DC Brush/CounterWeight.SLDPRT

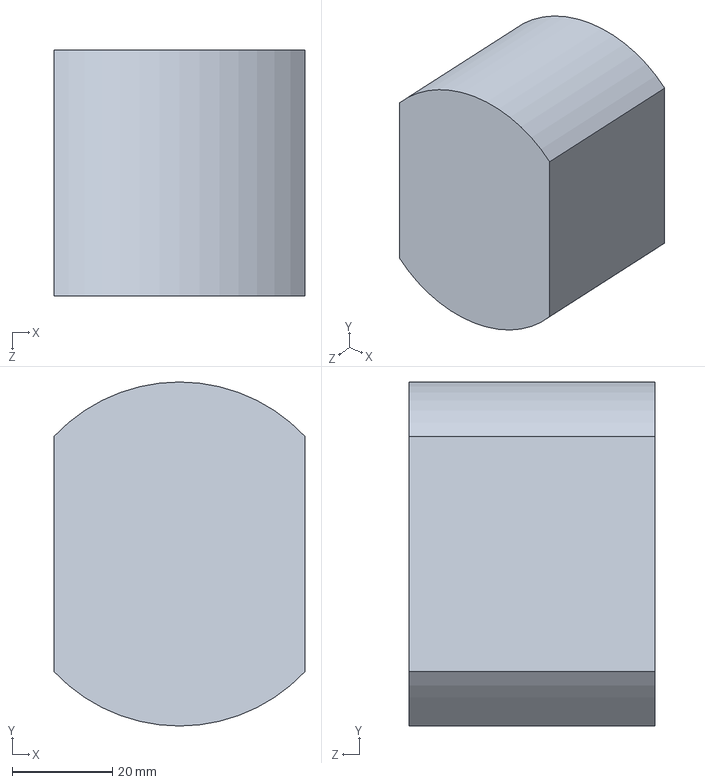
[picture p80: CAD file, 2023-07-05]
Hardware/CAD/Clock/R and P Arm DC Brush/CounterWeight.SLDPRT
50.0 x 68.6 x 49.0 mm
