hudsonburke/SandsOfTime/Hardware/CAD/Clock/R and P Arm DC Brush/HG Assembly 10-9/New Version of Assembly 10-9/LED_ring.SLDPRT

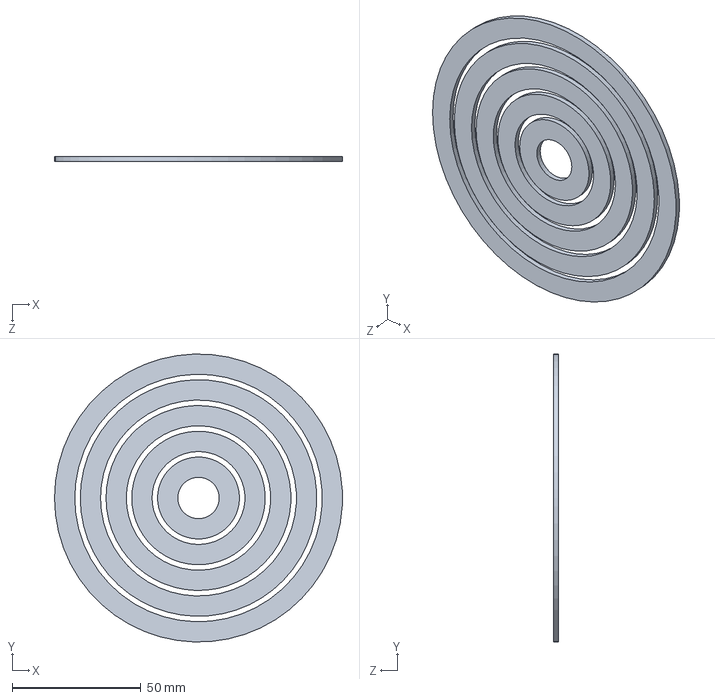
[picture p81: CAD file, 2023-07-05]
Hardware/CAD/Clock/R and P Arm DC Brush/HG Assembly 10-9/New Version of Assembly 10-9/LED_ring.SLDPRT
111.8 x 111.8 x 1.98 mm
