hudsonburke/SandsOfTime/Hardware/CAD/Clock/R and P Arm DC Brush/Outer_Channel/Base.SLDPRT

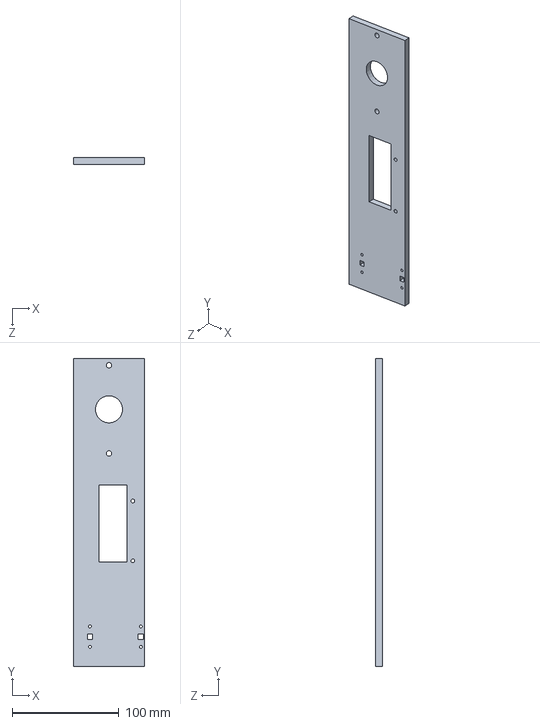
[picture p82: CAD file, 2023-07-05]
Hardware/CAD/Clock/R and P Arm DC Brush/Outer_Channel/Base.SLDPRT
66.7 x 288.3 x 6.35 mm
