hudsonburke/SandsOfTime/Hardware/CAD/Clock/Rack and Pinion Arm/Bottom_Channel/Side_Wall.SLDPRT

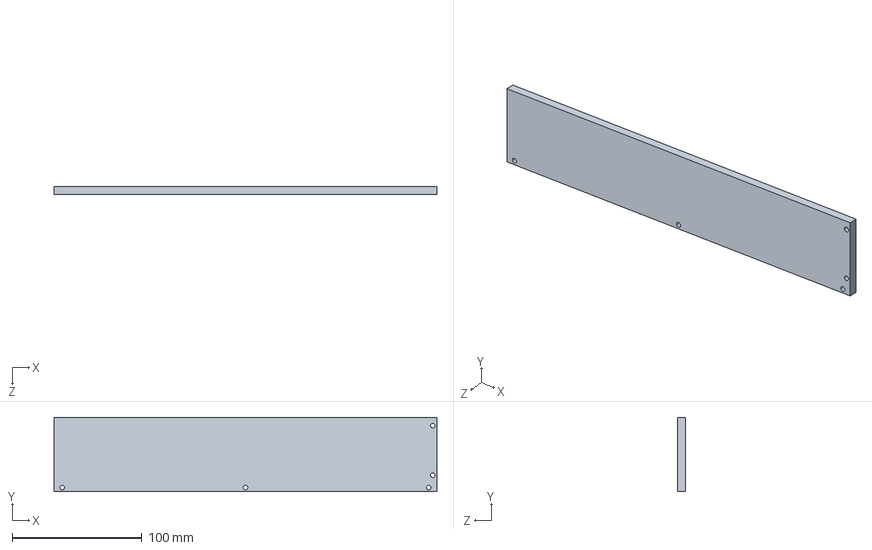
[picture p83: CAD file, 2023-07-05]
Hardware/CAD/Clock/Rack and Pinion Arm/Bottom_Channel/Side_Wall.SLDPRT
294.6 x 57.1 x 6.35 mm
