hudsonburke/SandsOfTime/Hardware/CAD/Clock/Rack and Pinion Arm/Inside_Channel/Top_of_T.SLDPRT

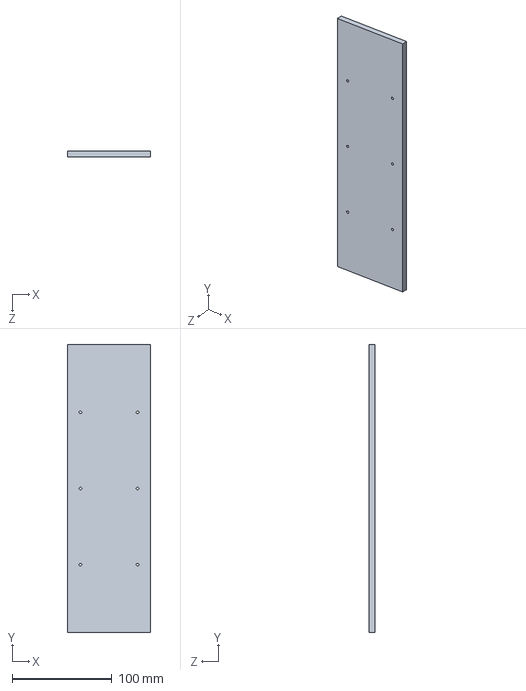
[picture p84: CAD file, 2023-07-05]
Hardware/CAD/Clock/Rack and Pinion Arm/Inside_Channel/Top_of_T.SLDPRT
83.5 x 288.3 x 6.35 mm
