hudsonburke/SandsOfTime/Hardware/CAD/Clock/Rack and Pinion Arm/Rack.SLDPRT

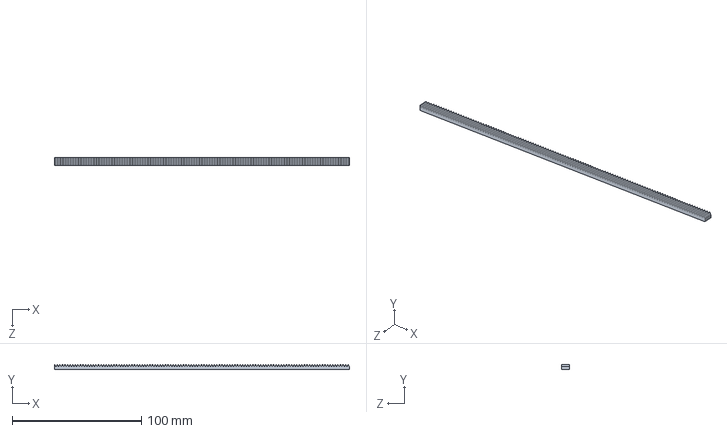
[picture p85: CAD file, 2023-07-05]
Hardware/CAD/Clock/Rack and Pinion Arm/Rack.SLDPRT
228.6 x 3.81 x 6.35 mm
