hudsonburke/SandsOfTime/PriorWork/MerrickBackup/Blocks/Inner Channel/Right_Side_IC.SLDPRT

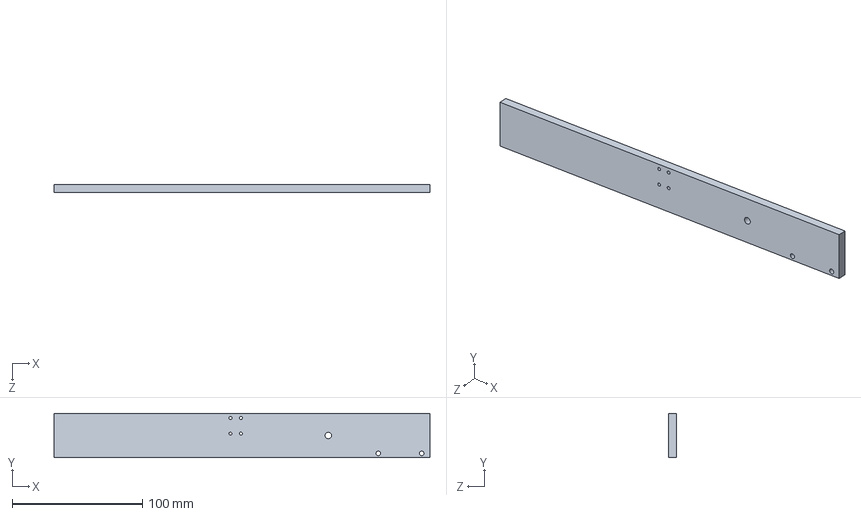
[picture p86: CAD file, 2023-07-05]
PriorWork/MerrickBackup/Blocks/Inner Channel/Right_Side_IC.SLDPRT
288.3 x 33.8 x 6.35 mm
