hudsonburke/SandsOfTime/PriorWork/MerrickBackup/DXFs/Inner_Arm/L.DXF

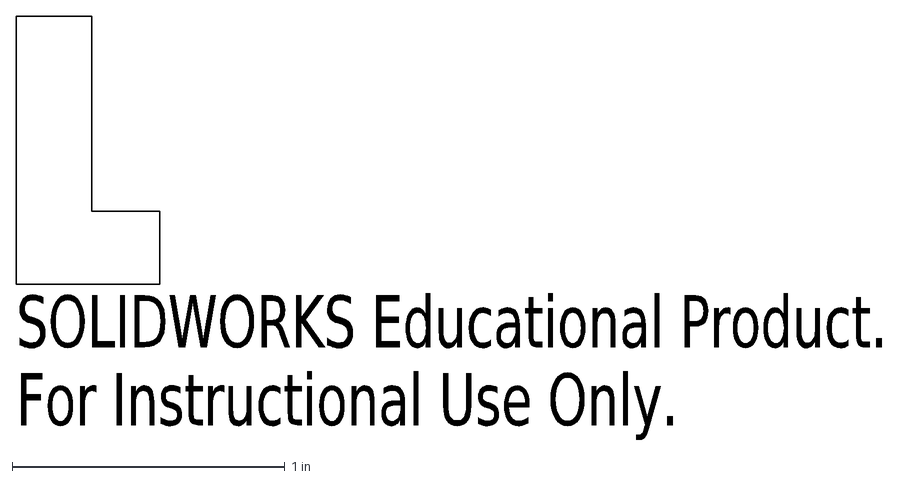
[picture p87: CAD file, 2023-07-05]
PriorWork/MerrickBackup/DXFs/Inner_Arm/L.DXF
SOLIDWORKS Educational Product.
For Instructional Use Only.
