hudsonburke/SandsOfTime/PriorWork/MerrickBackup/DXFs/LCD_Panel.DXF

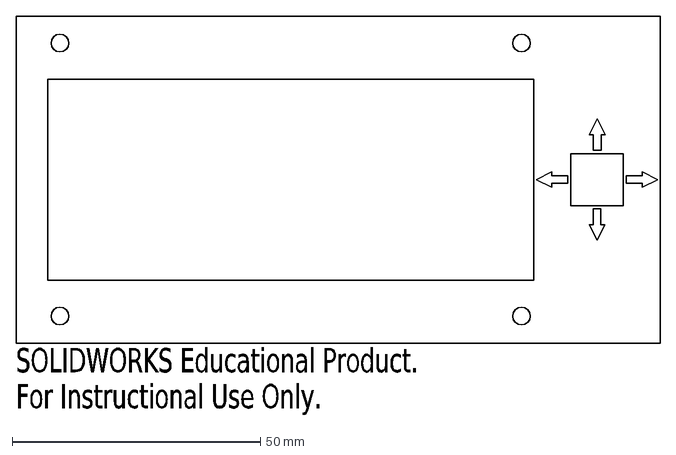
[picture p88: CAD file, 2023-07-05]
PriorWork/MerrickBackup/DXFs/LCD_Panel.DXF
SOLIDWORKS Educational Product.
For Instructional Use Only.
