hudsonburke/SandsOfTime/PriorWork/MerrickBackup/DXFs/Outer_Arm/Back_OC.SLDPRT

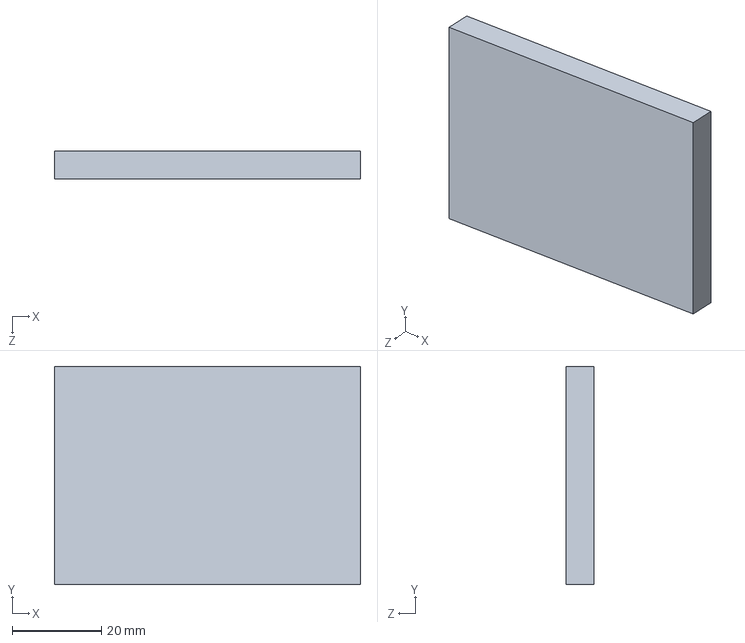
[picture p89: CAD file, 2023-07-05]
PriorWork/MerrickBackup/DXFs/Outer_Arm/Back_OC.SLDPRT
68.7 x 49.0 x 6.35 mm
