hudsonburke/SandsOfTime/PriorWork/MerrickBackup/Solidworks/Clock/SandClockCenter.SLDPRT

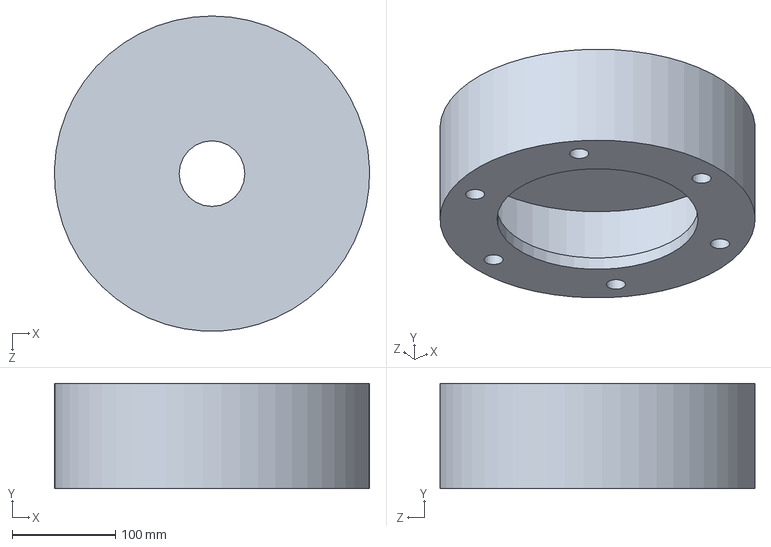
[picture p90: CAD file, 2023-07-05]
PriorWork/MerrickBackup/Solidworks/Clock/SandClockCenter.SLDPRT
304.7 x 101.6 x 304.5 mm
