hudsonburke/SandsOfTime/PriorWork/MerrickBackup/WaterJet/Furman_Capstone_Rotunda.dxf

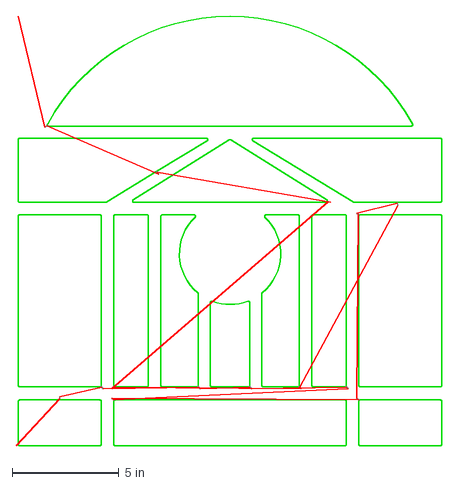
[picture p91: CAD file, 2023-07-05]
PriorWork/MerrickBackup/WaterJet/Furman_Capstone_Rotunda.dxf
20.0 x 20.1 in
