hudsonburke/SandsOfTime/PriorWork/Solidworks/Solidworks/Clock/Wood_Example.SLDPRT

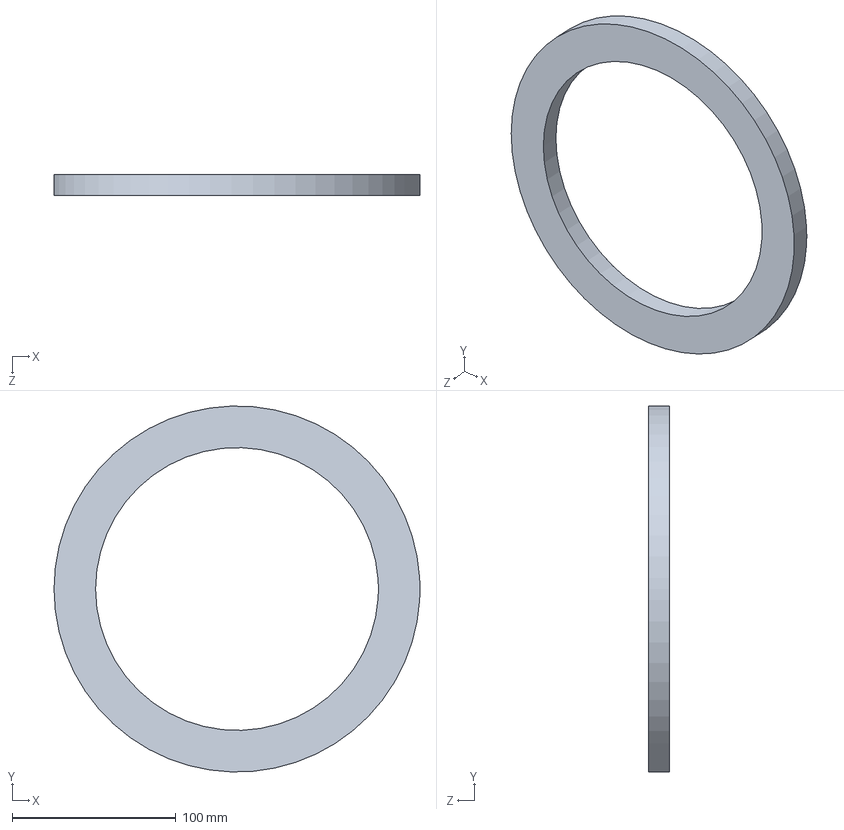
[picture p92: CAD file, 2023-07-05]
PriorWork/Solidworks/Solidworks/Clock/Wood_Example.SLDPRT
223.5 x 223.4 x 12.7 mm
