hudsonburke/SandsOfTime/Hardware/CAD/Clock/Arm/Motor_Holder.SLDPRT

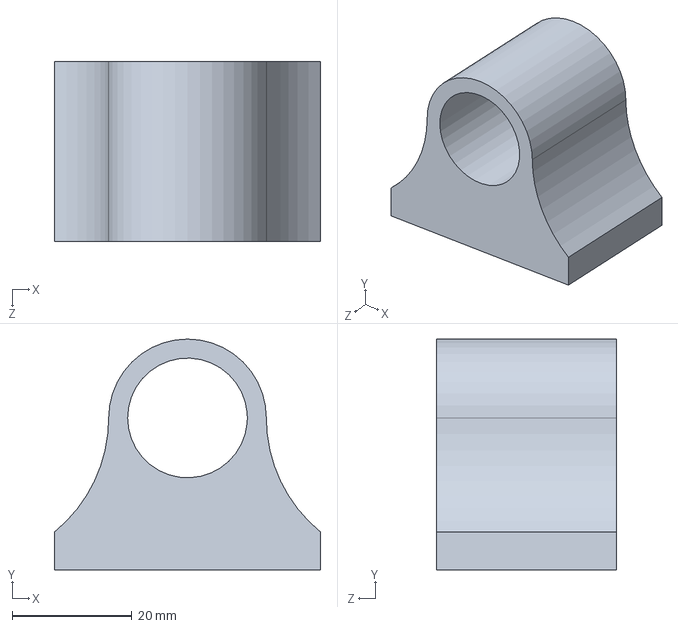
[picture p93: CAD file, 2023-07-05]
Hardware/CAD/Clock/Arm/Motor_Holder.SLDPRT
44.5 x 38.6 x 30.0 mm
