hudsonburke/SandsOfTime/Hardware/CAD/Clock/CNC Backplate/CNC_Toolpaths.SLDPRT

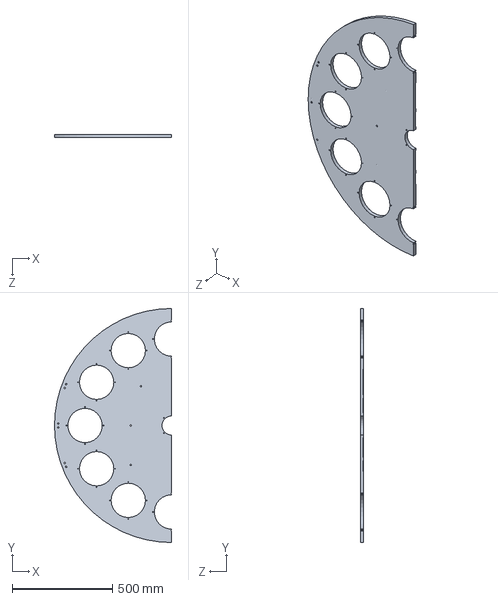
[picture p94: CAD file, 2023-07-05]
Hardware/CAD/Clock/CNC Backplate/CNC_Toolpaths.SLDPRT
584.2 x 1168.4 x 17.3 mm
