hudsonburke/SandsOfTime/Hardware/CAD/Clock/Number_Plate.SLDPRT

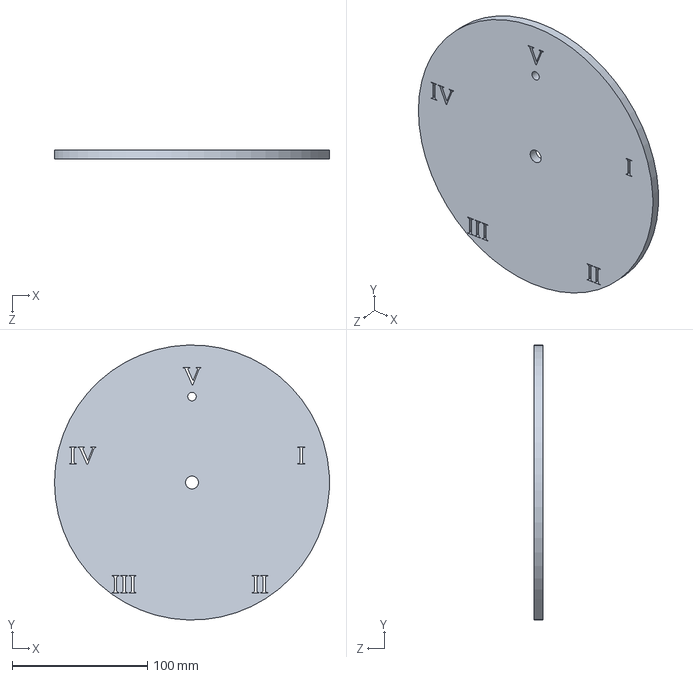
[picture p95: CAD file, 2023-07-05]
Hardware/CAD/Clock/Number_Plate.SLDPRT
203.2 x 203.1 x 6.35 mm
