hudsonburke/SandsOfTime/Hardware/CAD/Clock/Open Back/Second_BackPlate.SLDPRT

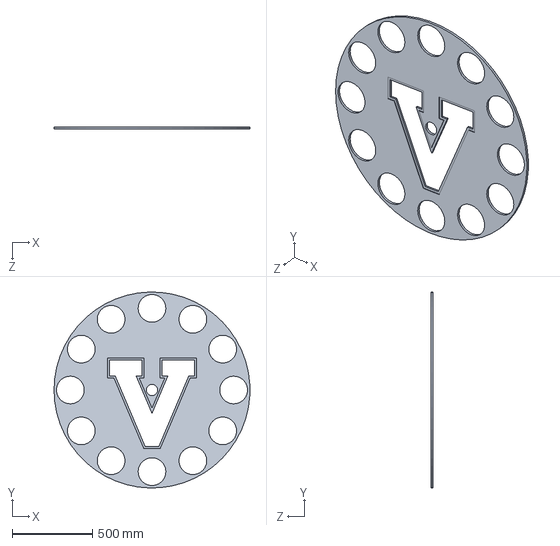
[picture p96: CAD file, 2023-07-05]
Hardware/CAD/Clock/Open Back/Second_BackPlate.SLDPRT
1219.2 x 1218.7 x 12.7 mm
