hudsonburke/SandsOfTime/Hardware/CAD/Clock/R and P Arm DC Brush/Limit_Switch.SLDPRT

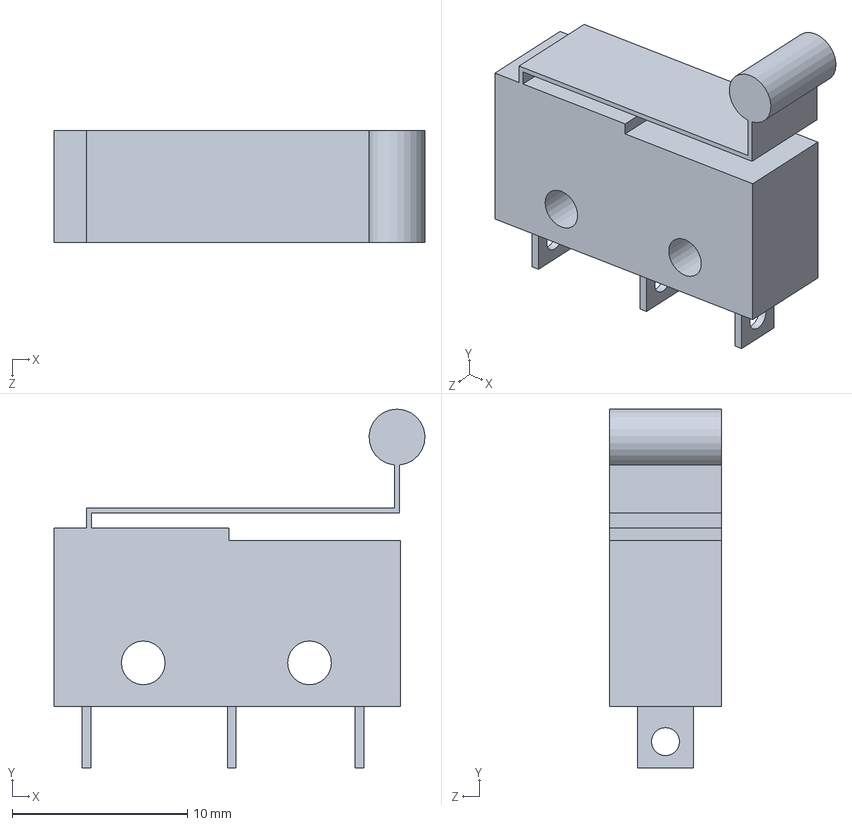
[picture p97: CAD file, 2023-07-05]
Hardware/CAD/Clock/R and P Arm DC Brush/Limit_Switch.SLDPRT
21.2 x 20.5 x 6.40 mm
