hudsonburke/SandsOfTime/Hardware/CAD/Clock/R and P Arm DC Brush/Outer_Channel/Back.SLDPRT

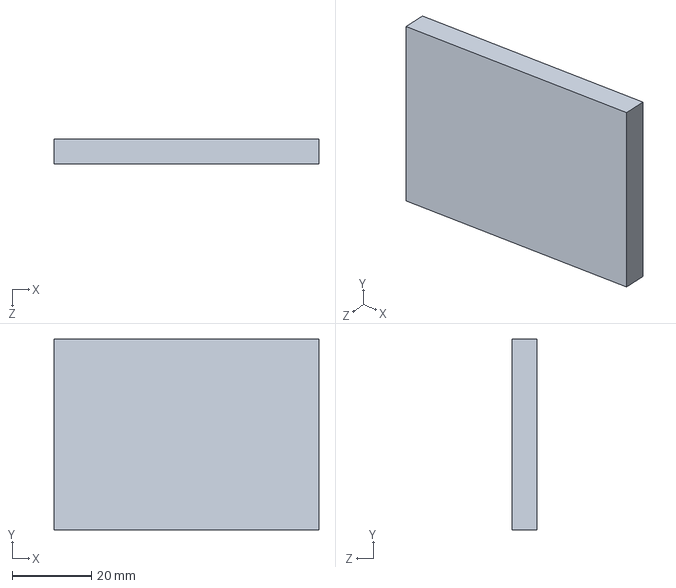
[picture p98: CAD file, 2023-07-05]
Hardware/CAD/Clock/R and P Arm DC Brush/Outer_Channel/Back.SLDPRT
66.7 x 48.0 x 6.35 mm
