hudsonburke/SandsOfTime/Hardware/CAD/Clock/Rack and Pinion Arm/Bottom_Channel/Back_Plate.SLDPRT

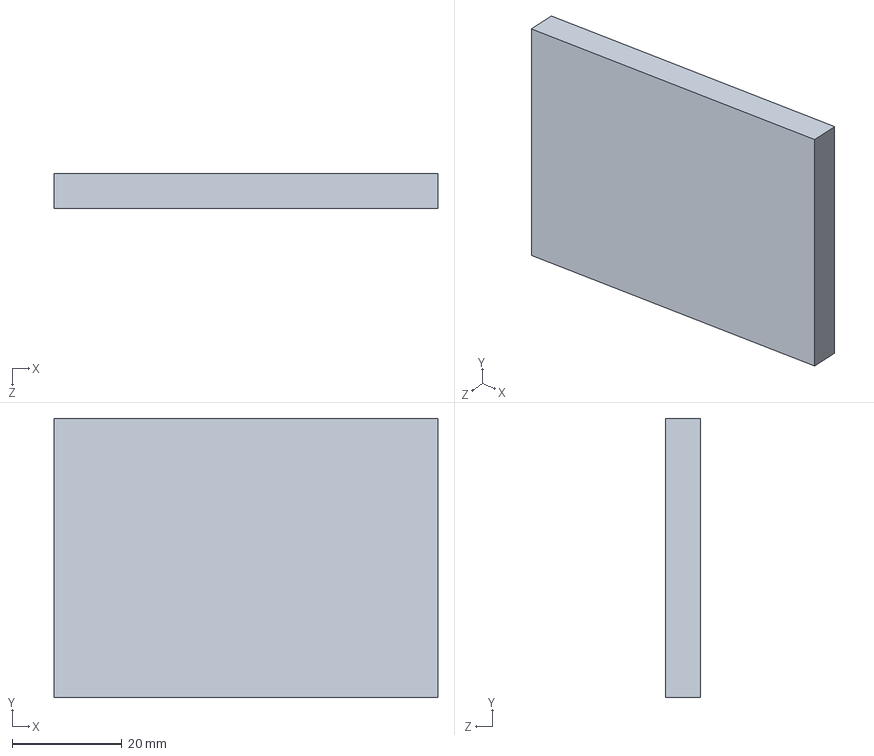
[picture p99: CAD file, 2023-07-05]
Hardware/CAD/Clock/Rack and Pinion Arm/Bottom_Channel/Back_Plate.SLDPRT
69.8 x 50.8 x 6.35 mm
