hudsonburke/SandsOfTime/Hardware/CAD/Clock/Rack and Pinion Arm/Inside_Channel/Top_Piece.SLDPRT

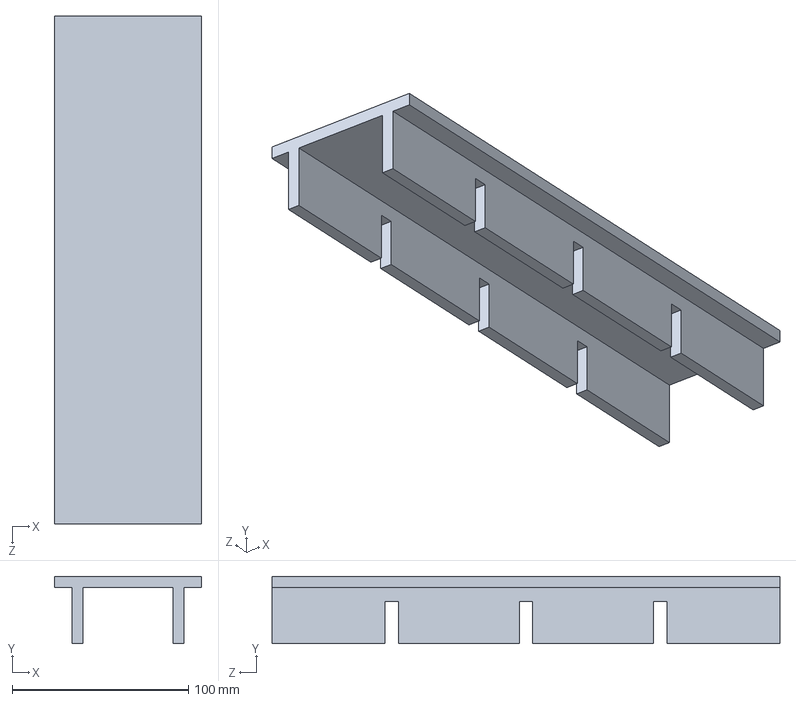
[picture p100: CAD file, 2023-07-05]
Hardware/CAD/Clock/Rack and Pinion Arm/Inside_Channel/Top_Piece.SLDPRT
83.5 x 38.1 x 288.3 mm
