hudsonburke/SandsOfTime/Hardware/CAD/Clock/Rack and Pinion Arm/Rubber_Insulator.SLDPRT

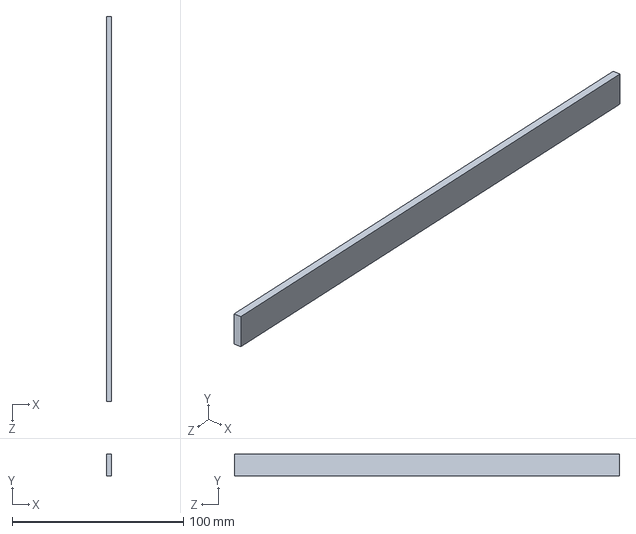
[picture p101: CAD file, 2023-07-05]
Hardware/CAD/Clock/Rack and Pinion Arm/Rubber_Insulator.SLDPRT
3.17 x 12.7 x 224.8 mm
