hudsonburke/SandsOfTime/PriorWork/MerrickBackup/DXFs/Encoder_Top_Plate.DXF

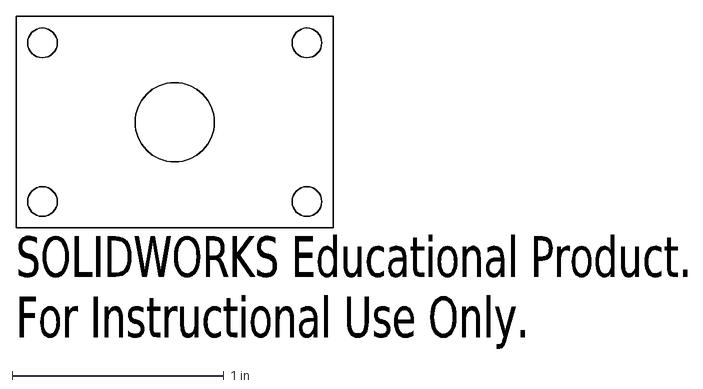
[picture p102: CAD file, 2023-07-05]
PriorWork/MerrickBackup/DXFs/Encoder_Top_Plate.DXF
SOLIDWORKS Educational Product.
For Instructional Use Only.
