hudsonburke/SandsOfTime/PriorWork/MerrickBackup/DXFs/Inner_Arm/Left_Side_IC.DXF

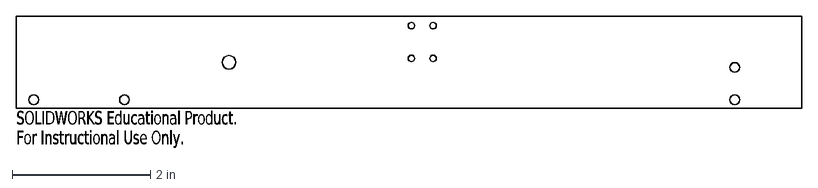
[picture p103: CAD file, 2023-07-05]
PriorWork/MerrickBackup/DXFs/Inner_Arm/Left_Side_IC.DXF
SOLIDWORKS Educational Product.
For Instructional Use Only.
