hudsonburke/SandsOfTime/PriorWork/MerrickBackup/DXFs/Outer_Arm/Right_Side_OC.SLDPRT

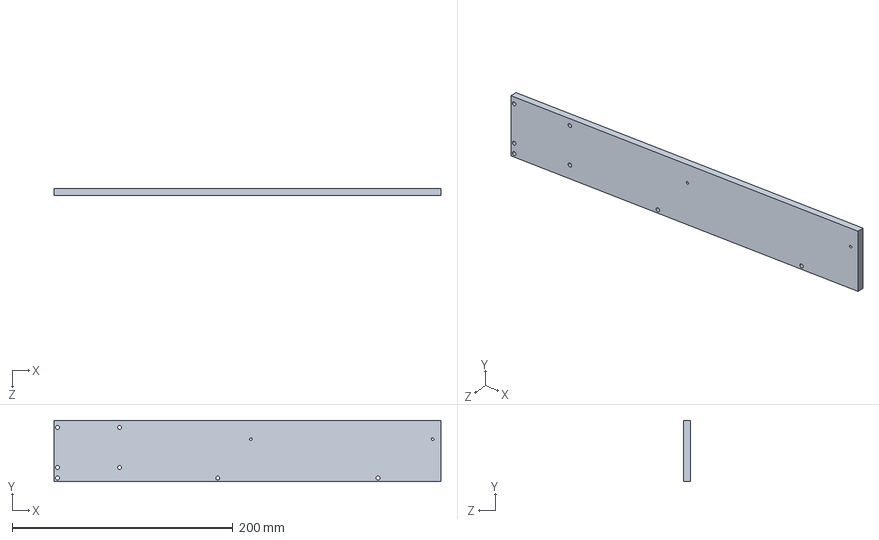
[picture p104: CAD file, 2023-07-05]
PriorWork/MerrickBackup/DXFs/Outer_Arm/Right_Side_OC.SLDPRT
351.0 x 55.3 x 6.35 mm
