hudsonburke/SandsOfTime/PriorWork/MerrickBackup/Solidworks/HG_Assembly/Diffuser.SLDPRT

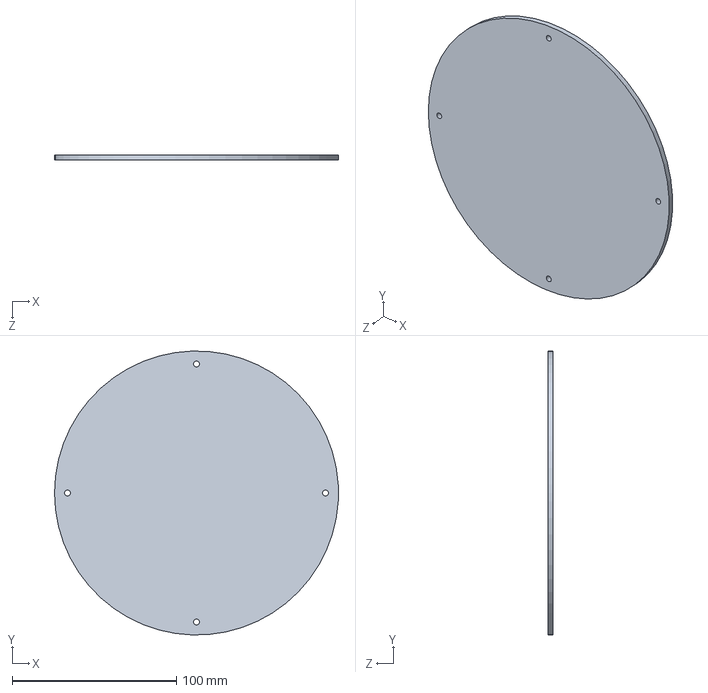
[picture p105: CAD file, 2023-07-05]
PriorWork/MerrickBackup/Solidworks/HG_Assembly/Diffuser.SLDPRT
172.7 x 172.6 x 3.17 mm
