hudsonburke/SandsOfTime/Hardware/CAD/Clock/CNC Backplate/Rotunda_Plate.SLDPRT

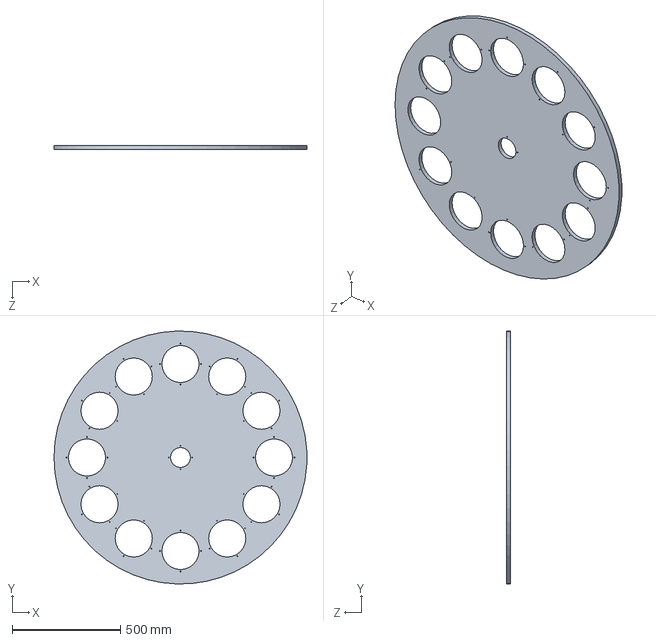
[picture p106: CAD file, 2023-07-05]
Hardware/CAD/Clock/CNC Backplate/Rotunda_Plate.SLDPRT
1168.4 x 1167.9 x 19.1 mm
