hudsonburke/SandsOfTime/Hardware/CAD/Clock/LED_strip.SLDPRT

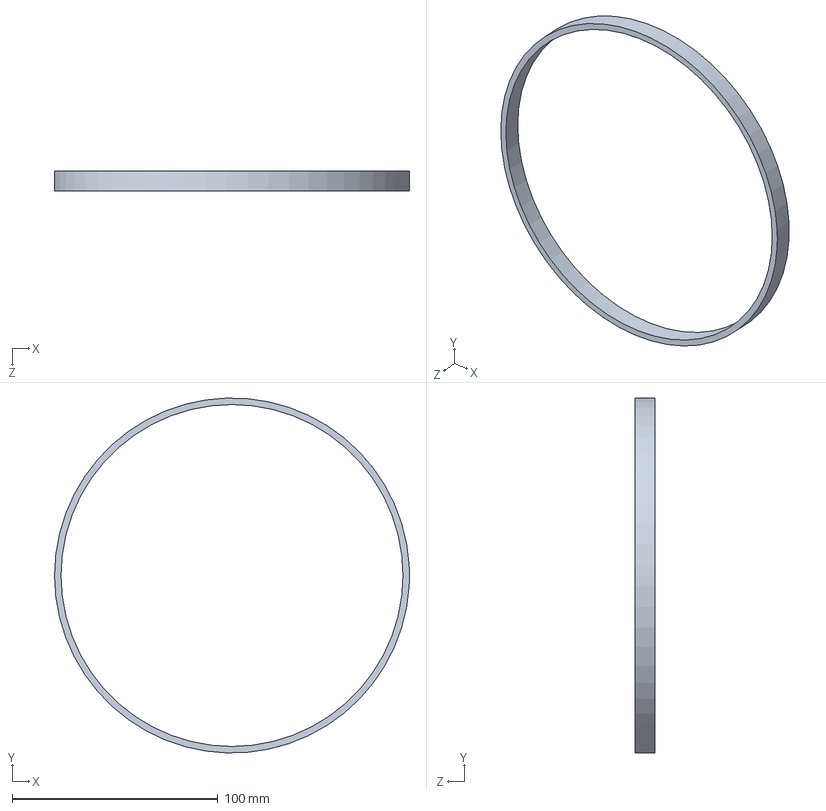
[picture p107: CAD file, 2023-07-05]
Hardware/CAD/Clock/LED_strip.SLDPRT
172.7 x 172.6 x 9.53 mm
