hudsonburke/SandsOfTime/Hardware/CAD/Clock/R and P Arm DC Brush/HG Assembly 10-9/New Version of Assembly 10-9/Diffuser.SLDPRT

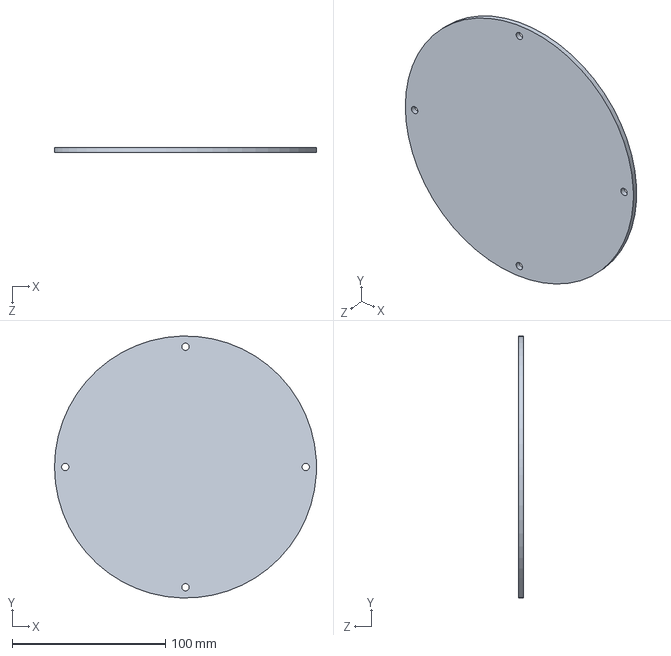
[picture p108: CAD file, 2023-07-05]
Hardware/CAD/Clock/R and P Arm DC Brush/HG Assembly 10-9/New Version of Assembly 10-9/Diffuser.SLDPRT
171.0 x 170.9 x 3.17 mm
