hudsonburke/SandsOfTime/Hardware/CAD/Clock/R and P Arm DC Brush/Pinion_Final.SLDPRT

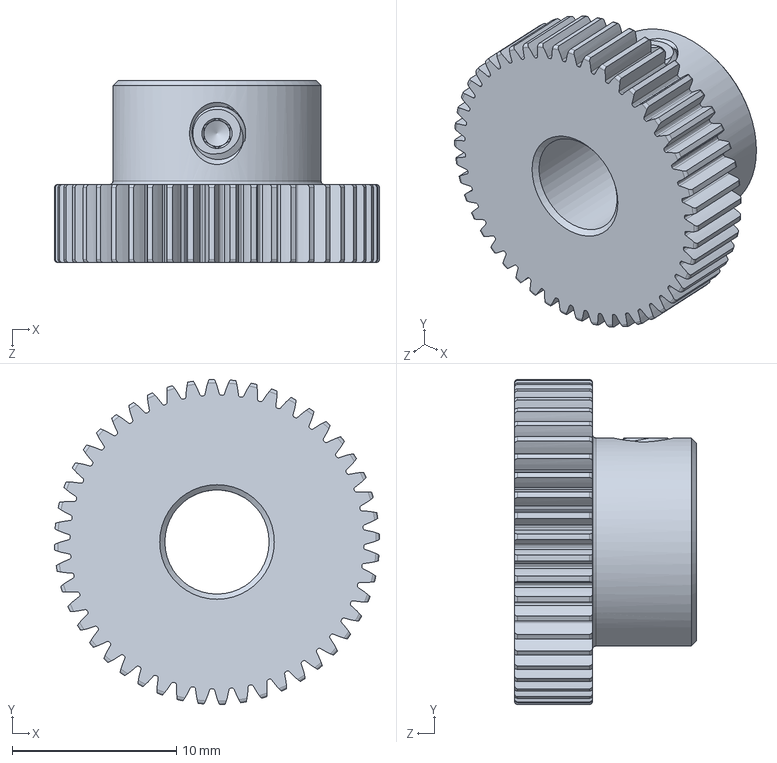
[picture p109: CAD file, 2023-07-05]
Hardware/CAD/Clock/R and P Arm DC Brush/Pinion_Final.SLDPRT
19.8 x 19.8 x 11.1 mm
