hudsonburke/SandsOfTime/Hardware/CAD/Clock/Rack and Pinion Arm/Inside_Channel/Slide.SLDPRT

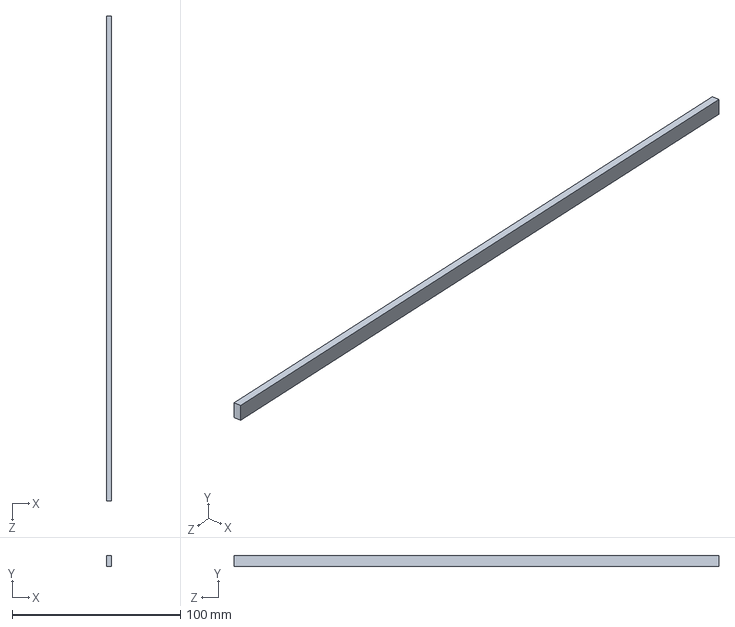
[picture p110: CAD file, 2023-07-05]
Hardware/CAD/Clock/Rack and Pinion Arm/Inside_Channel/Slide.SLDPRT
3.17 x 6.35 x 288.3 mm
