hudsonburke/SandsOfTime/Hardware/CAD/Clock/Rack and Pinion Arm/Slip_Ring.SLDPRT

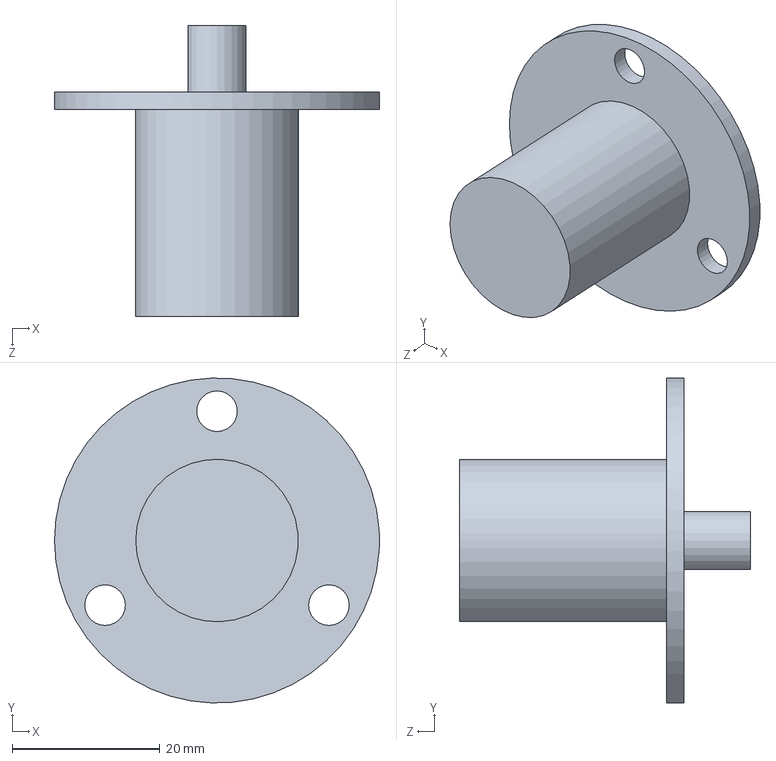
[picture p111: CAD file, 2023-07-05]
Hardware/CAD/Clock/Rack and Pinion Arm/Slip_Ring.SLDPRT
44.0 x 44.0 x 39.4 mm
