hudsonburke/SandsOfTime/PriorWork/MerrickBackup/DXFs/Inner_Arm/Top_IC.DXF

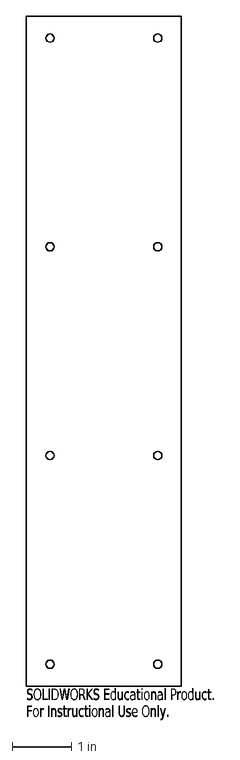
[picture p112: CAD file, 2023-07-05]
PriorWork/MerrickBackup/DXFs/Inner_Arm/Top_IC.DXF
SOLIDWORKS Educational Product.
For Instructional Use Only.
