hudsonburke/SandsOfTime/PriorWork/MerrickBackup/Solidworks/HG_Assembly/HG_Gear.SLDPRT

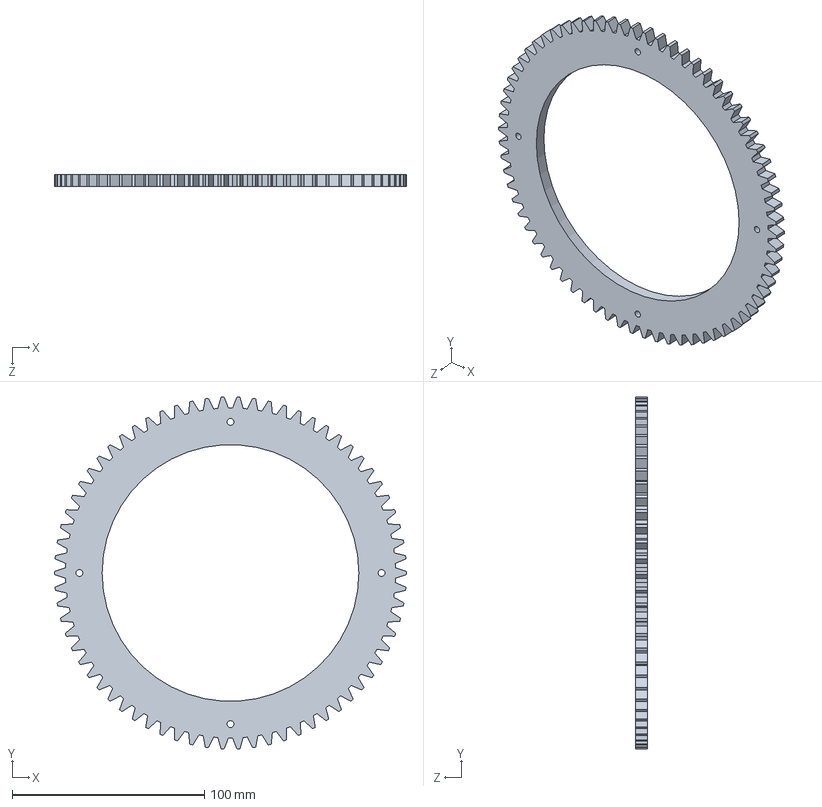
[picture p113: CAD file, 2023-07-05]
PriorWork/MerrickBackup/Solidworks/HG_Assembly/HG_Gear.SLDPRT
182.9 x 182.8 x 6.35 mm
