hudsonburke/SandsOfTime/PriorWork/Solidworks/Solidworks/HG_Assembly/Encoder_Plate.SLDPRT

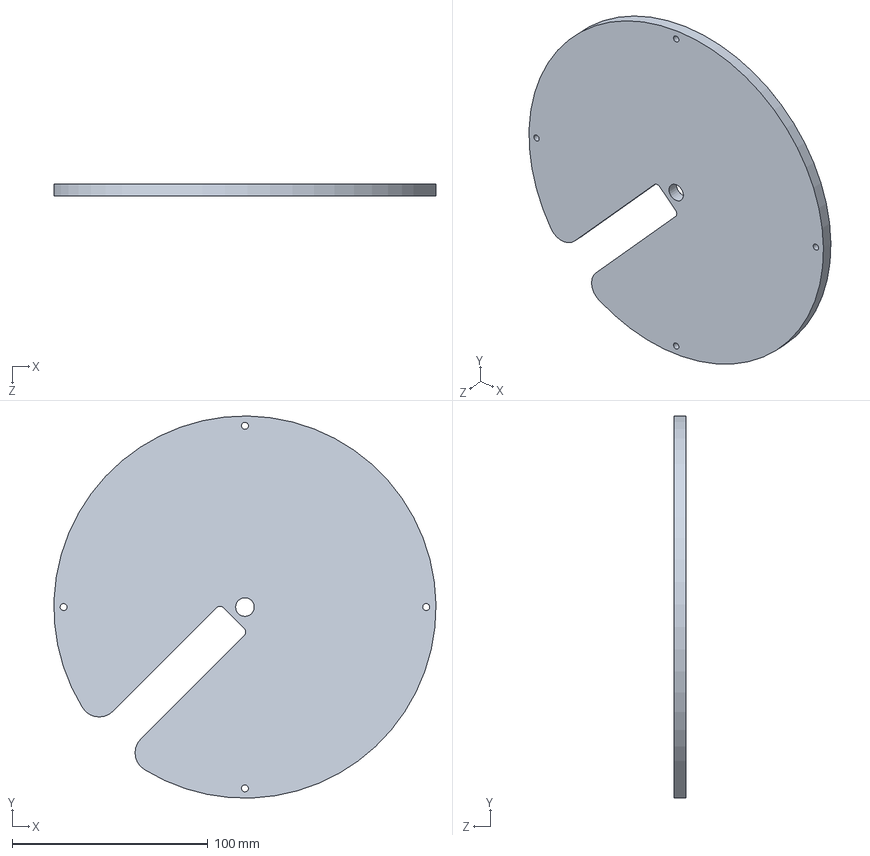
[picture p114: CAD file, 2023-07-05]
PriorWork/Solidworks/Solidworks/HG_Assembly/Encoder_Plate.SLDPRT
194.9 x 194.9 x 6.35 mm
