hudsonburke/SandsOfTime/Hardware/CAD/Clock/CNC Backplate/Spacer_Arcs.SLDPRT

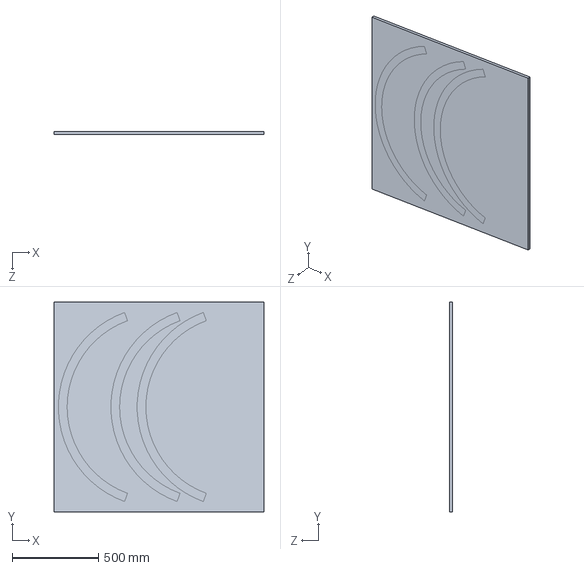
[picture p115: CAD file, 2023-07-05]
Hardware/CAD/Clock/CNC Backplate/Spacer_Arcs.SLDPRT
1219.2 x 1219.2 x 19.1 mm
