hudsonburke/SandsOfTime/Hardware/CAD/Clock/Flick_Standoff.SLDPRT

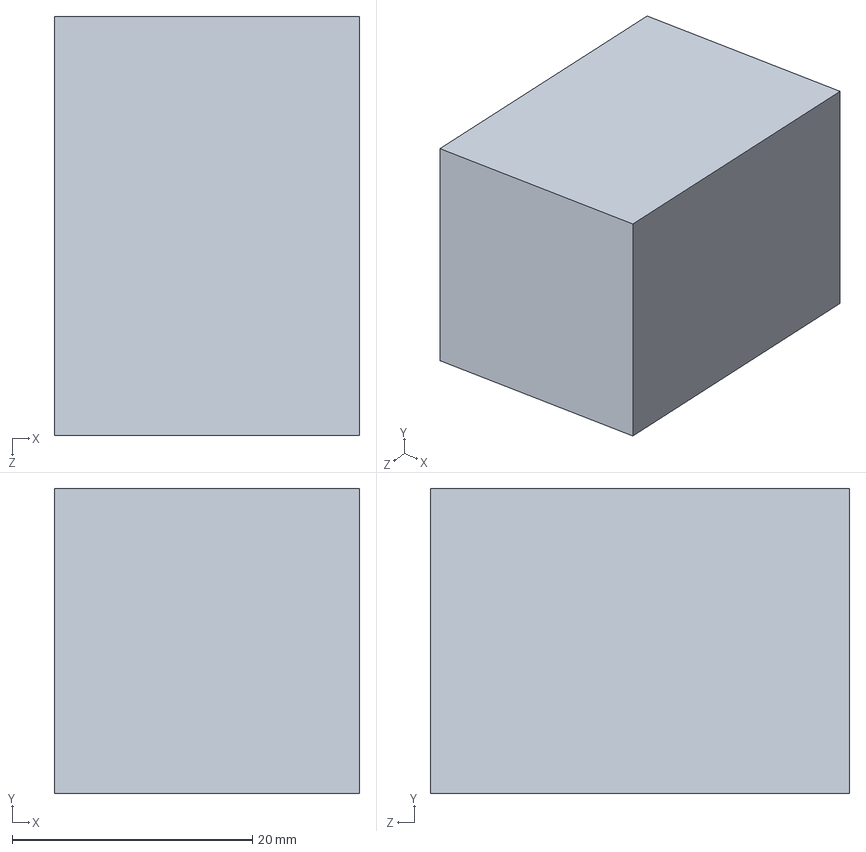
[picture p116: CAD file, 2023-07-05]
Hardware/CAD/Clock/Flick_Standoff.SLDPRT
25.4 x 25.4 x 34.9 mm
