hudsonburke/SandsOfTime/Hardware/CAD/Clock/R and P Arm DC Brush/HG Assembly 10-9/New Version of Assembly 10-9/Encoder.SLDPRT

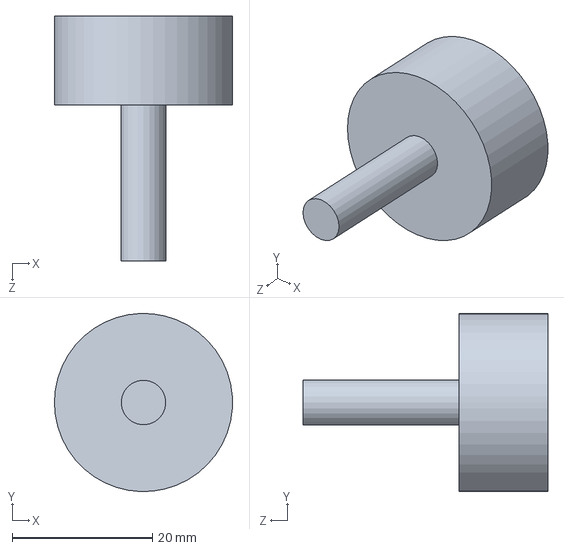
[picture p117: CAD file, 2023-07-05]
Hardware/CAD/Clock/R and P Arm DC Brush/HG Assembly 10-9/New Version of Assembly 10-9/Encoder.SLDPRT
25.4 x 25.4 x 34.9 mm
