hudsonburke/SandsOfTime/Hardware/CAD/Clock/R and P Arm DC Brush/Quarter_Face_Ring.SLDPRT

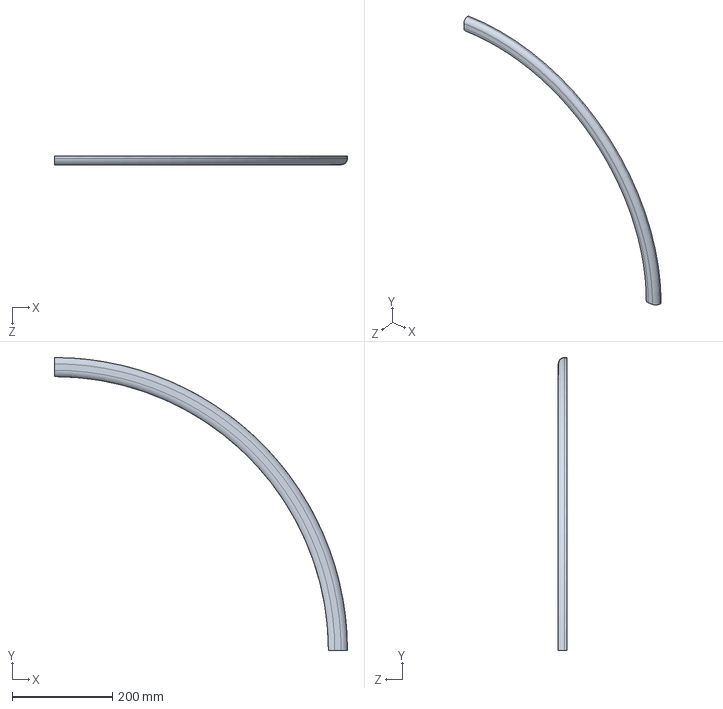
[picture p118: CAD file, 2023-07-05]
Hardware/CAD/Clock/R and P Arm DC Brush/Quarter_Face_Ring.SLDPRT
584.2 x 584.2 x 17.3 mm
