hudsonburke/SandsOfTime/Hardware/CAD/Clock/Rack and Pinion Arm/Bottom_Channel/Bottom_Plate.SLDPRT

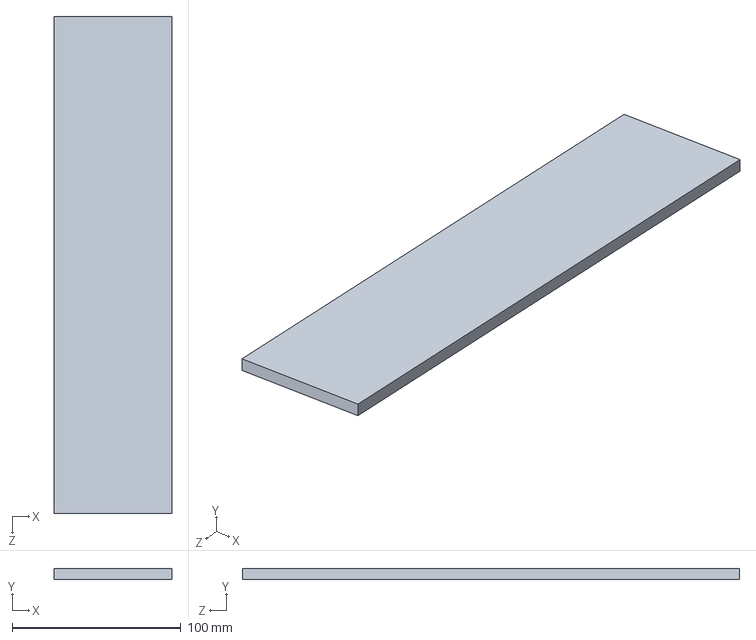
[picture p119: CAD file, 2023-07-05]
Hardware/CAD/Clock/Rack and Pinion Arm/Bottom_Channel/Bottom_Plate.SLDPRT
69.8 x 6.35 x 294.6 mm
