hudsonburke/SandsOfTime/Hardware/CAD/Clock/Rack and Pinion Arm/Large_Gear_Shaft.STL

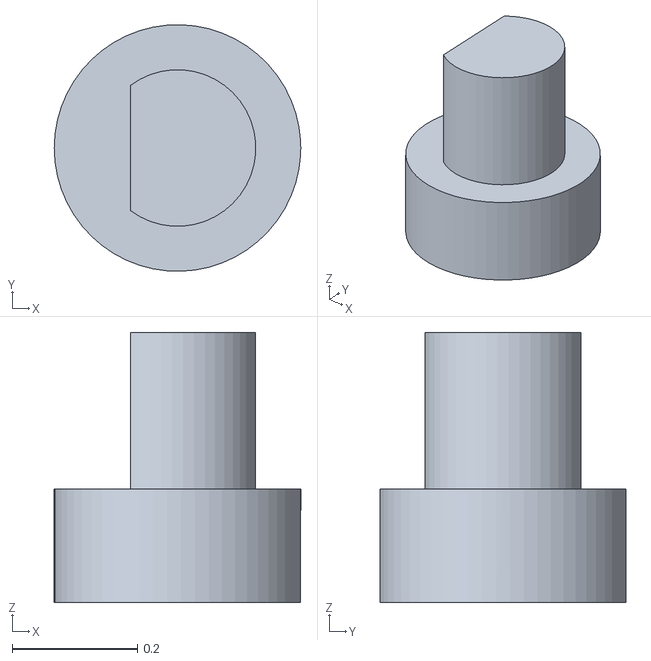
[picture p120: CAD file, 2023-07-05]
Hardware/CAD/Clock/Rack and Pinion Arm/Large_Gear_Shaft.STL
0.394 x 0.394 x 0.431
