hudsonburke/SandsOfTime/PriorWork/MerrickBackup/Blocks/Inner Channel/Bottom_IC.SLDPRT

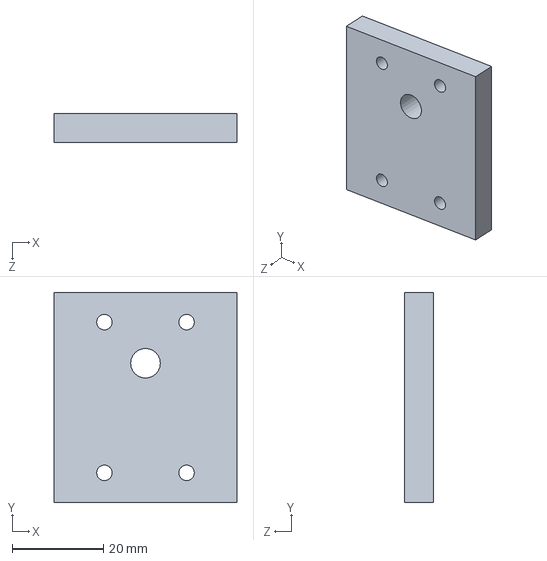
[picture p121: CAD file, 2023-07-05]
PriorWork/MerrickBackup/Blocks/Inner Channel/Bottom_IC.SLDPRT
40.0 x 46.0 x 6.35 mm
