hudsonburke/SandsOfTime/PriorWork/MerrickBackup/DXFs/Encoder_Bottom_Plate.DXF

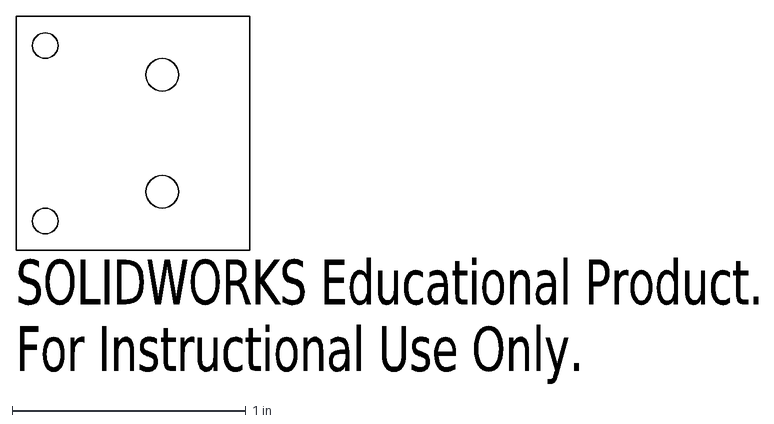
[picture p122: CAD file, 2023-07-05]
PriorWork/MerrickBackup/DXFs/Encoder_Bottom_Plate.DXF
SOLIDWORKS Educational Product.
For Instructional Use Only.
