hudsonburke/SandsOfTime/PriorWork/MerrickBackup/Solidworks/HG_Assembly/6_32_2_inch.SLDPRT

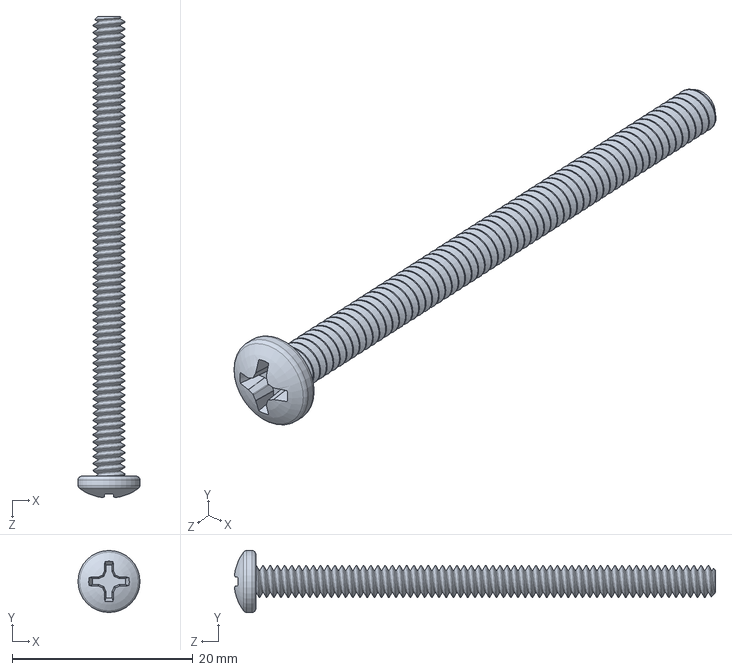
[picture p124: CAD file, 2023-07-05]
PriorWork/MerrickBackup/Solidworks/HG_Assembly/6_32_2_inch.SLDPRT
6.86 x 6.86 x 53.2 mm
