hudsonburke/SandsOfTime/Hardware/CAD/Clock/Arm/Small_Motor.SLDPRT

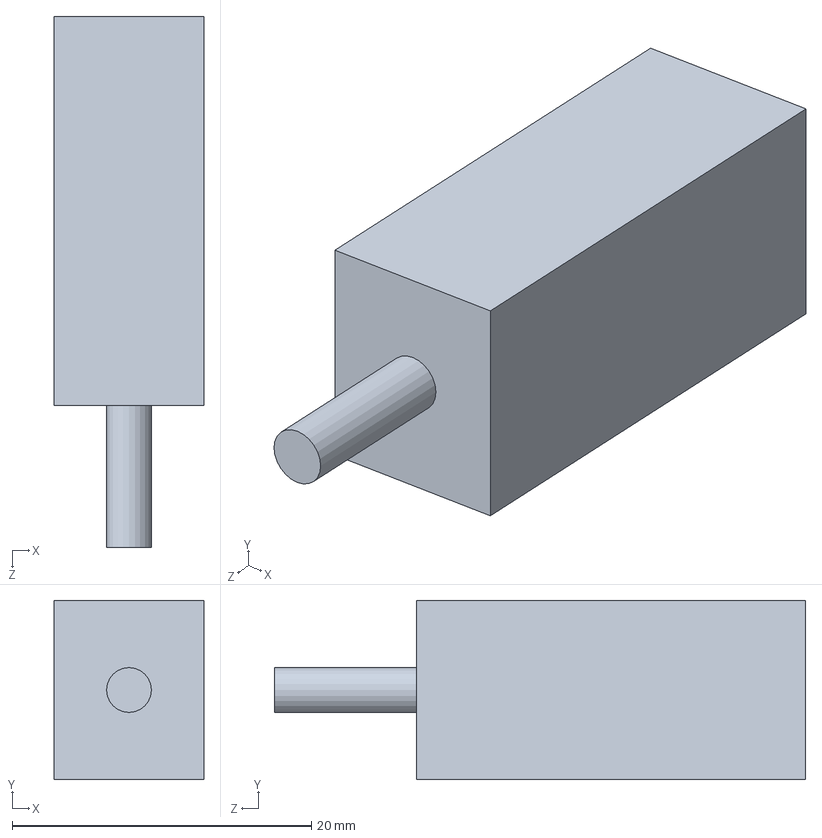
[picture p125: CAD file, 2023-07-05]
Hardware/CAD/Clock/Arm/Small_Motor.SLDPRT
10.0 x 12.0 x 35.5 mm
