hudsonburke/SandsOfTime/Hardware/CAD/Clock/Encoder_Post_Mount.SLDPRT

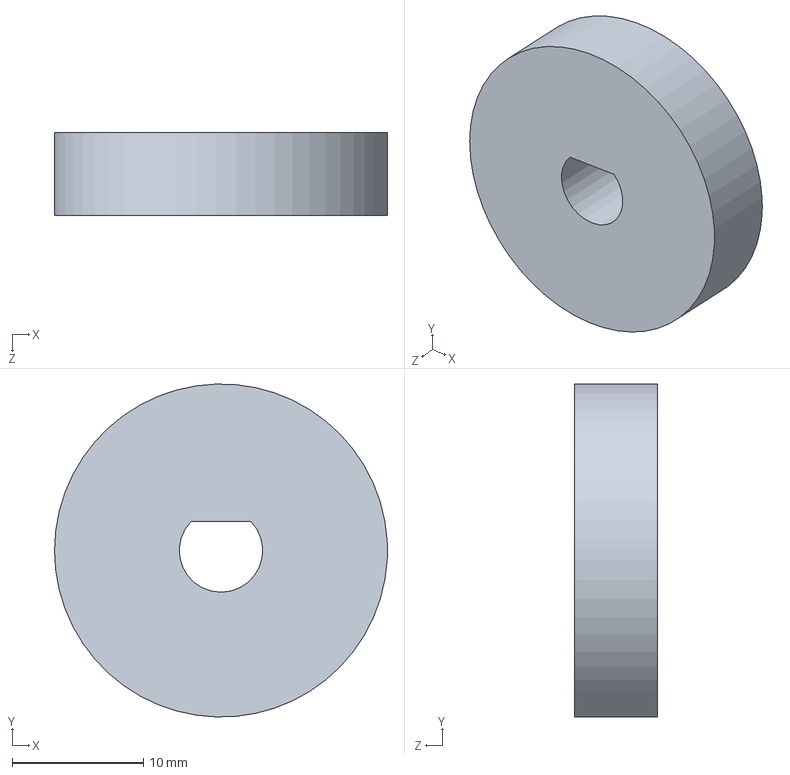
[picture p126: CAD file, 2023-07-05]
Hardware/CAD/Clock/Encoder_Post_Mount.SLDPRT
25.4 x 25.4 x 6.35 mm
