hudsonburke/SandsOfTime/Hardware/CAD/Clock/Open Back/Outer_Ring.SLDPRT

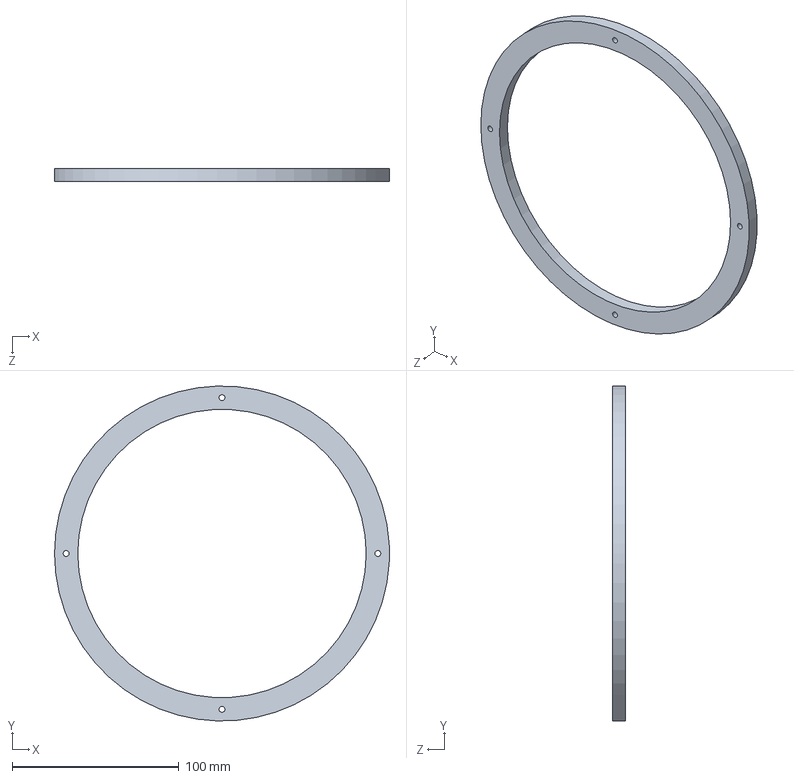
[picture p127: CAD file, 2023-07-05]
Hardware/CAD/Clock/Open Back/Outer_Ring.SLDPRT
200.7 x 200.6 x 7.62 mm
