hudsonburke/SandsOfTime/Hardware/CAD/Clock/R and P Arm DC Brush/HG Assembly 10-9/New Version of Assembly 10-9/Back_Plate.SLDPRT

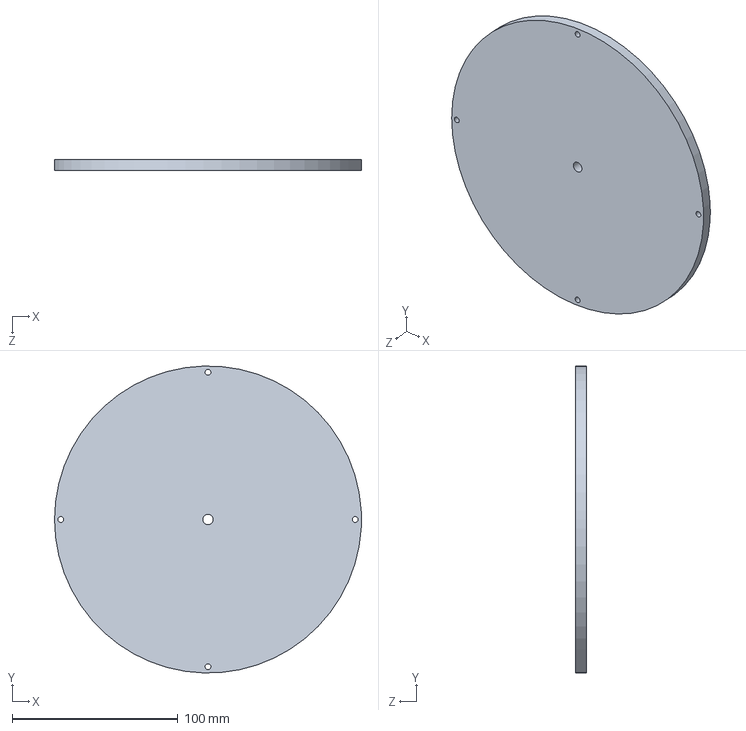
[picture p128: CAD file, 2023-07-05]
Hardware/CAD/Clock/R and P Arm DC Brush/HG Assembly 10-9/New Version of Assembly 10-9/Back_Plate.SLDPRT
185.4 x 185.3 x 6.35 mm
