hudsonburke/SandsOfTime/Hardware/CAD/Clock/R and P Arm DC Brush/Inside_Ring.SLDPRT

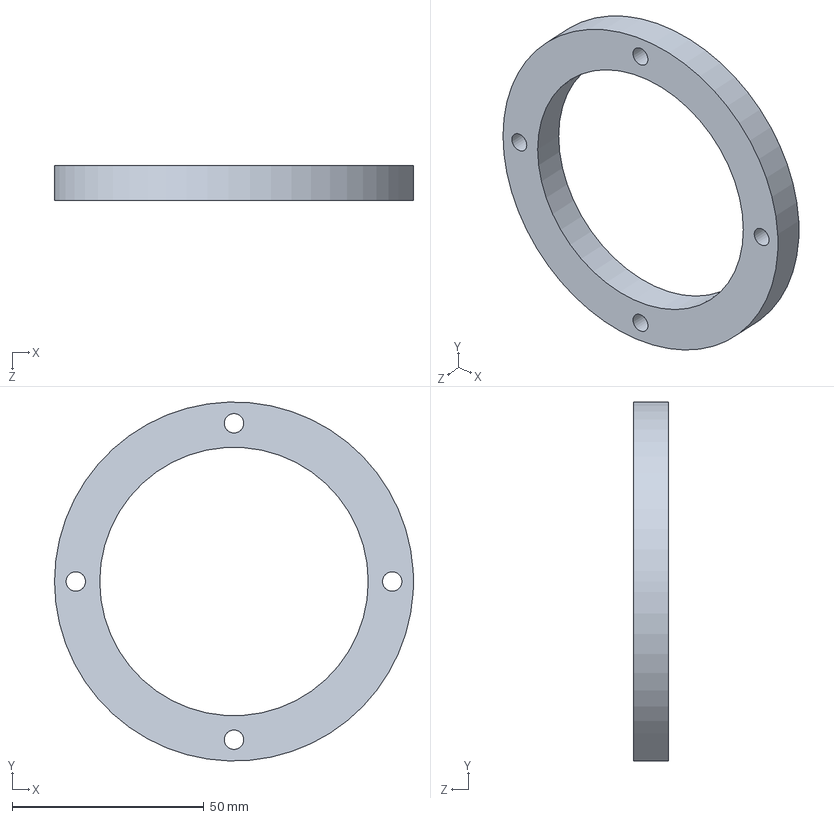
[picture p129: CAD file, 2023-07-05]
Hardware/CAD/Clock/R and P Arm DC Brush/Inside_Ring.SLDPRT
93.6 x 93.6 x 9.17 mm
