hudsonburke/SandsOfTime/Hardware/CAD/Clock/Rack and Pinion Arm/Bottom_Channel/Vert_Long_Outside.SLDPRT

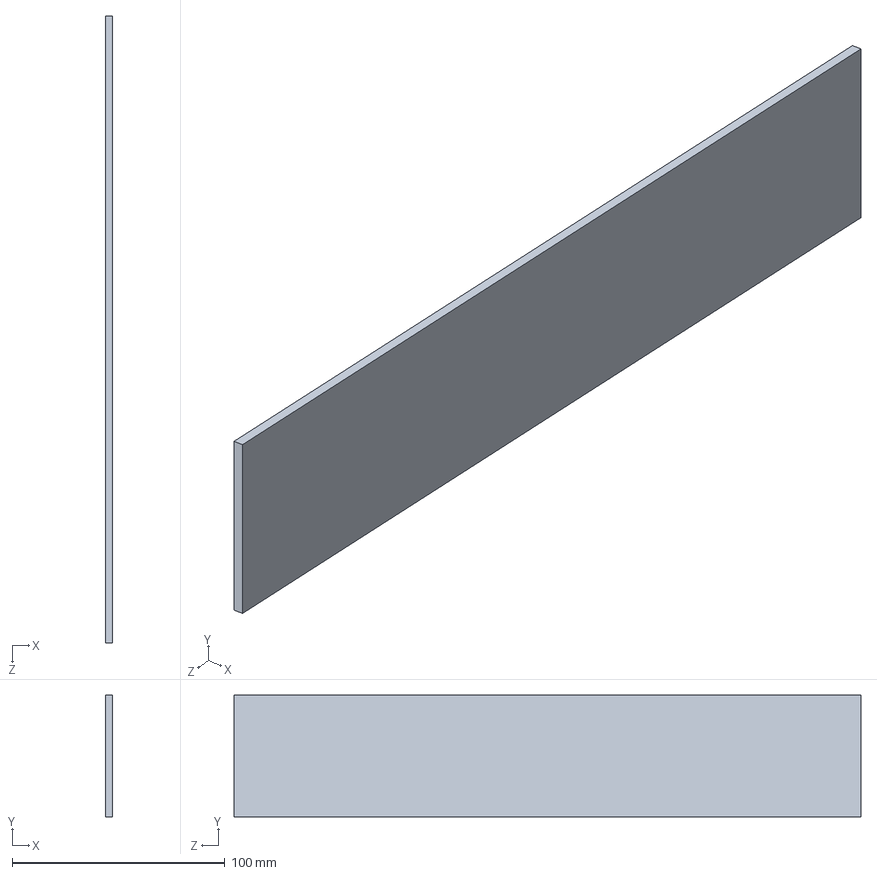
[picture p130: CAD file, 2023-07-05]
Hardware/CAD/Clock/Rack and Pinion Arm/Bottom_Channel/Vert_Long_Outside.SLDPRT
3.17 x 57.1 x 294.6 mm
