hudsonburke/SandsOfTime/Hardware/CAD/Clock/Rack and Pinion Arm/Graphite_Spring.SLDPRT

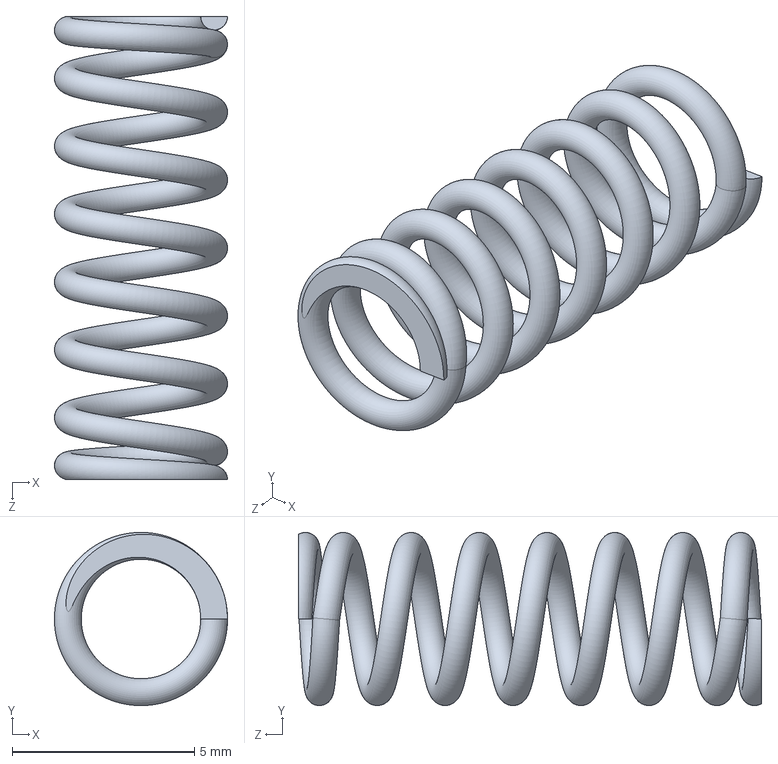
[picture p131: CAD file, 2023-07-05]
Hardware/CAD/Clock/Rack and Pinion Arm/Graphite_Spring.SLDPRT
4.75 x 4.75 x 12.7 mm
