hudsonburke/SandsOfTime/Hardware/CAD/Clock/Rack and Pinion Arm/Inside_Channel/Top.SLDPRT

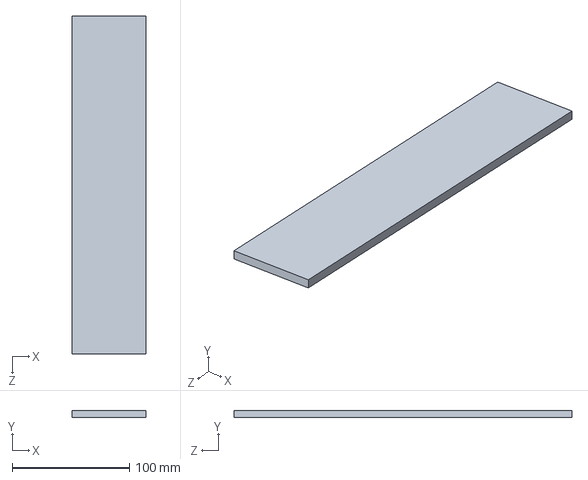
[picture p132: CAD file, 2023-07-05]
Hardware/CAD/Clock/Rack and Pinion Arm/Inside_Channel/Top.SLDPRT
63.5 x 6.35 x 288.3 mm
