hudsonburke/SandsOfTime/PriorWork/MerrickBackup/DXFs/LCD_Display_Plate.DXF

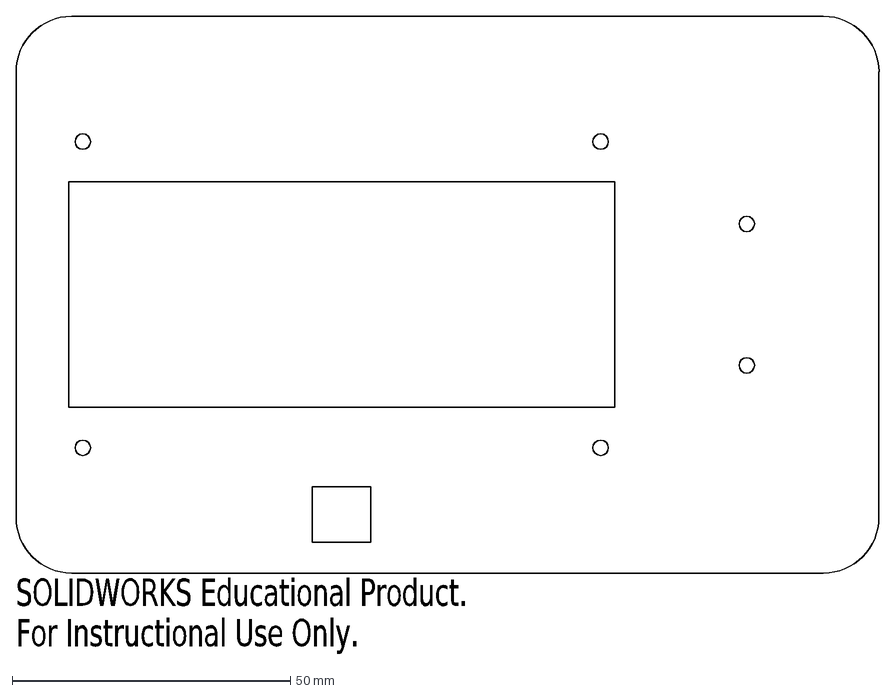
[picture p133: CAD file, 2023-07-05]
PriorWork/MerrickBackup/DXFs/LCD_Display_Plate.DXF
SOLIDWORKS Educational Product.
For Instructional Use Only.
