hudsonburke/SandsOfTime/PriorWork/MerrickBackup/Solidworks/HG_Assembly/Hourglass_holder_Plate_2.SLDPRT

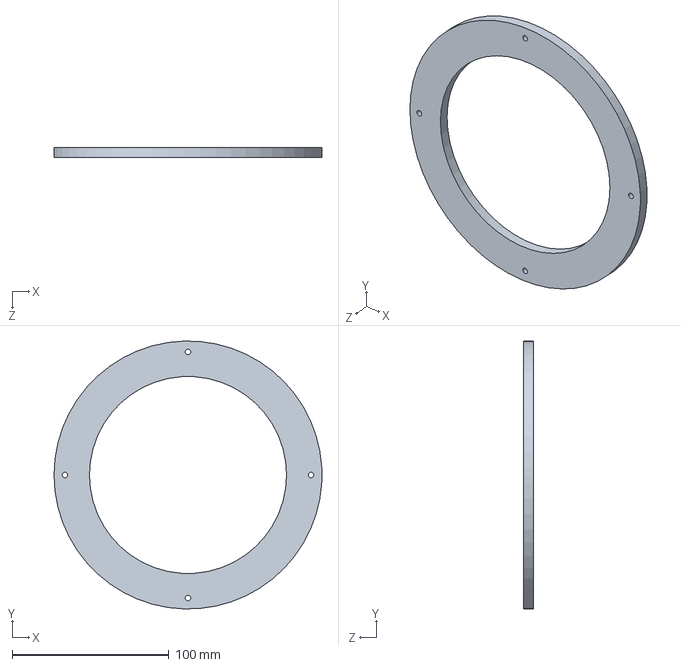
[picture p134: CAD file, 2023-07-05]
PriorWork/MerrickBackup/Solidworks/HG_Assembly/Hourglass_holder_Plate_2.SLDPRT
171.0 x 170.9 x 6.35 mm
