hudsonburke/SandsOfTime/Hardware/CAD/Clock/Big_Motor_Mount.SLDPRT

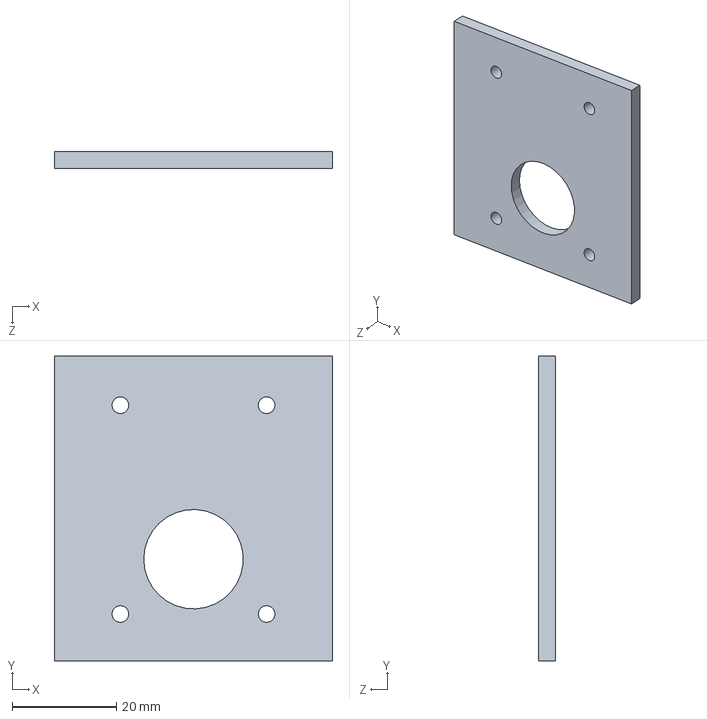
[picture p135: CAD file, 2023-07-05]
Hardware/CAD/Clock/Big_Motor_Mount.SLDPRT
53.3 x 58.4 x 3.17 mm
