hudsonburke/SandsOfTime/Hardware/CAD/Clock/Open Back/Linear_Actuator.SLDPRT

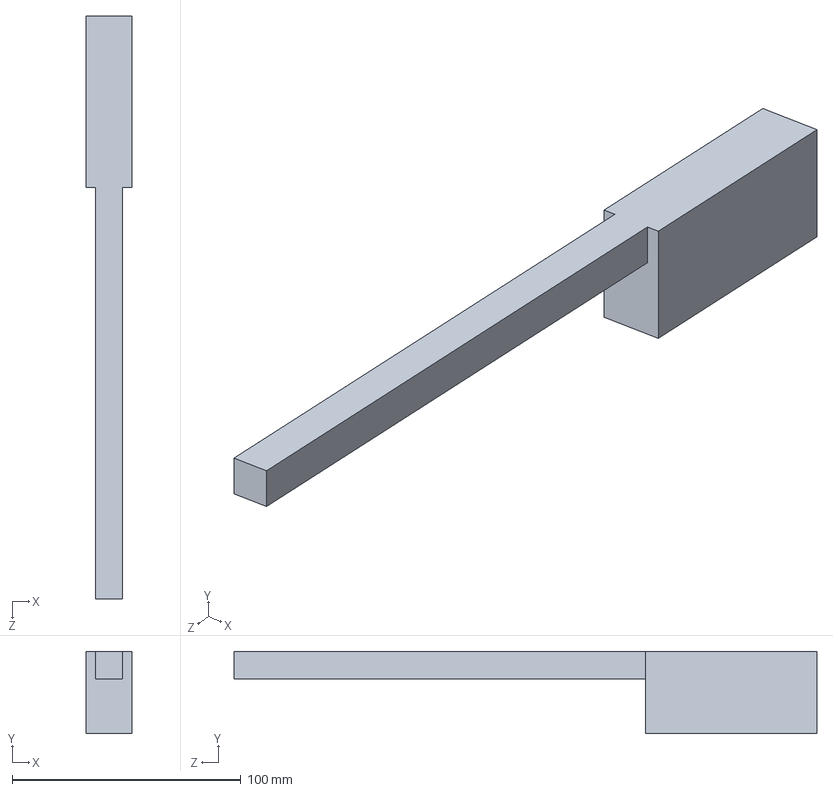
[picture p136: CAD file, 2023-07-05]
Hardware/CAD/Clock/Open Back/Linear_Actuator.SLDPRT
20.0 x 36.0 x 255.0 mm
