hudsonburke/SandsOfTime/Hardware/CAD/Clock/Rack and Pinion Arm/Bottom_Channel/Slide_Rail_Inside.SLDPRT

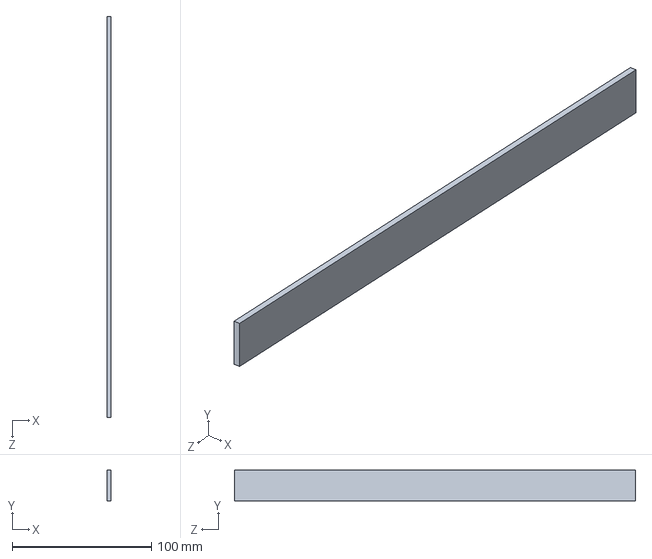
[picture p137: CAD file, 2023-07-05]
Hardware/CAD/Clock/Rack and Pinion Arm/Bottom_Channel/Slide_Rail_Inside.SLDPRT
3.17 x 22.2 x 288.3 mm
