hudsonburke/SandsOfTime/Hardware/CAD/Clock/Rack and Pinion Arm/Idler_Gear.SLDPRT

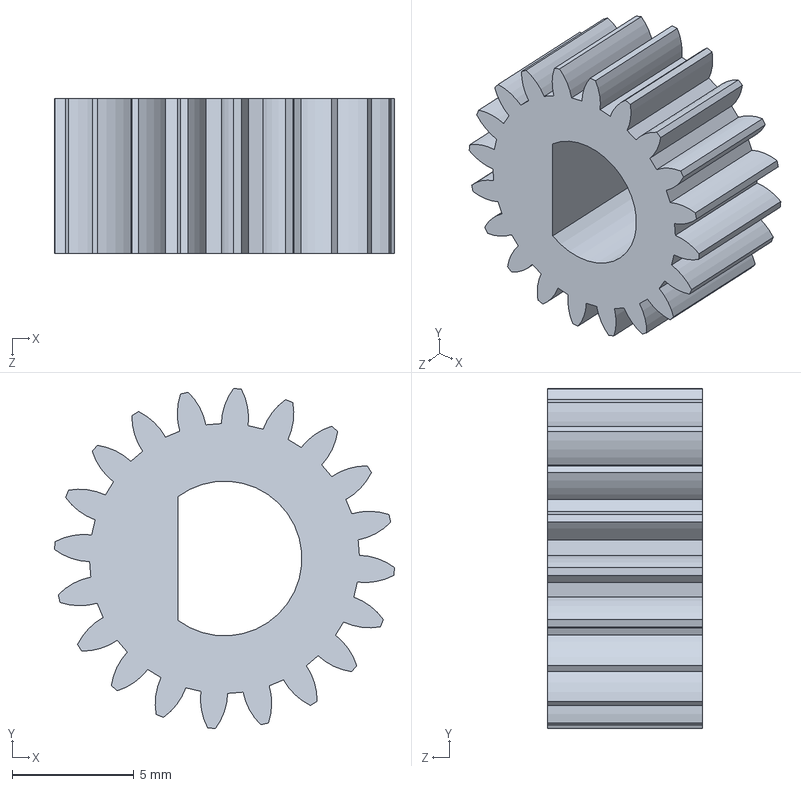
[picture p138: CAD file, 2023-07-05]
Hardware/CAD/Clock/Rack and Pinion Arm/Idler_Gear.SLDPRT
14.0 x 14.0 x 6.35 mm
