hudsonburke/SandsOfTime/PriorWork/MerrickBackup/DXFs/Encoder_Jig_Wall_quarter.DXF

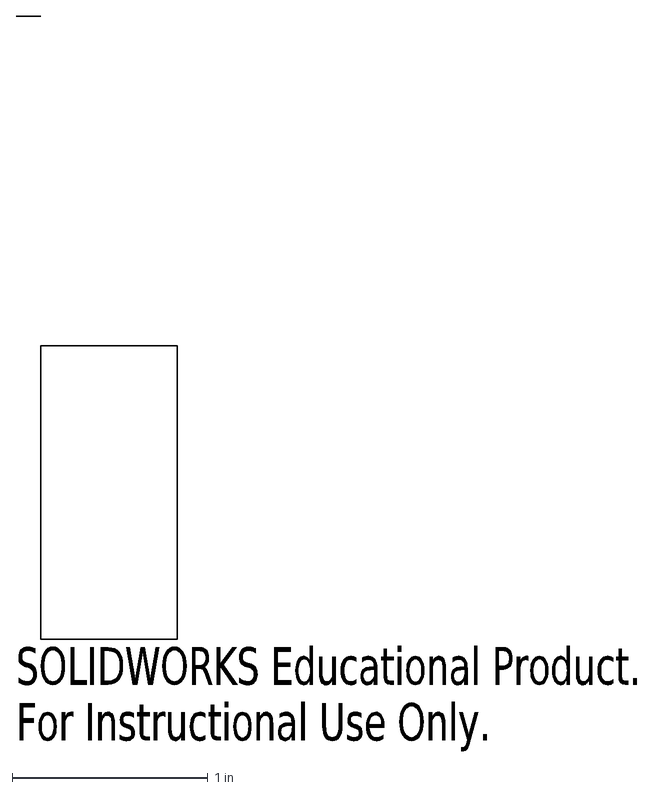
[picture p139: CAD file, 2023-07-05]
PriorWork/MerrickBackup/DXFs/Encoder_Jig_Wall_quarter.DXF
SOLIDWORKS Educational Product.
For Instructional Use Only.
