hudsonburke/SandsOfTime/Hardware/CAD/Clock/Open Back/Back_Plate1.SLDPRT

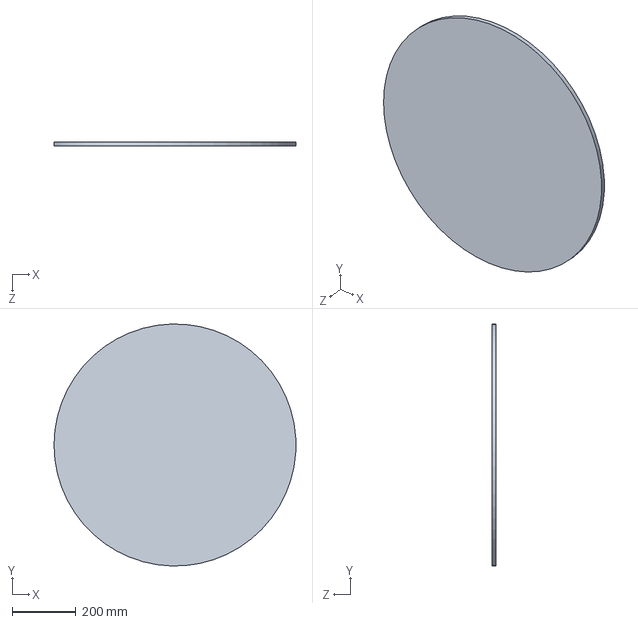
[picture p140: CAD file, 2023-07-05]
Hardware/CAD/Clock/Open Back/Back_Plate1.SLDPRT
762.0 x 761.7 x 12.7 mm
