hudsonburke/SandsOfTime/Hardware/CAD/Clock/R and P Arm DC Brush/Face_Ring.SLDPRT

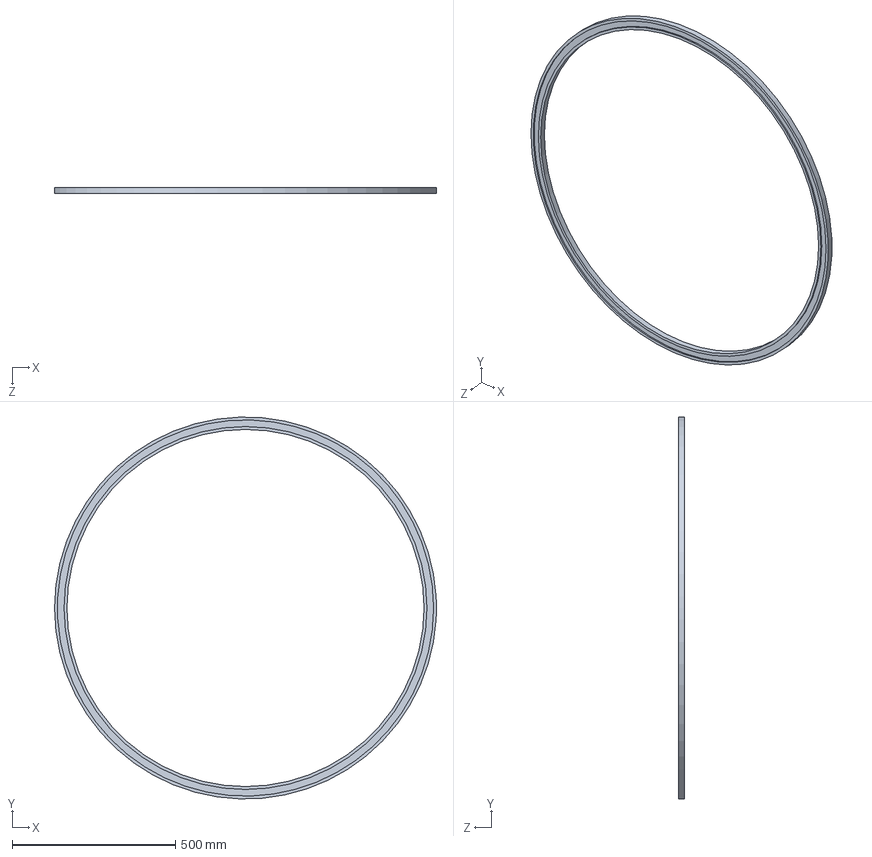
[picture p141: CAD file, 2023-07-05]
Hardware/CAD/Clock/R and P Arm DC Brush/Face_Ring.SLDPRT
1168.4 x 1167.9 x 19.1 mm
