hudsonburke/SandsOfTime/Hardware/CAD/Clock/Rack and Pinion Arm/Brush_Holder.SLDPRT

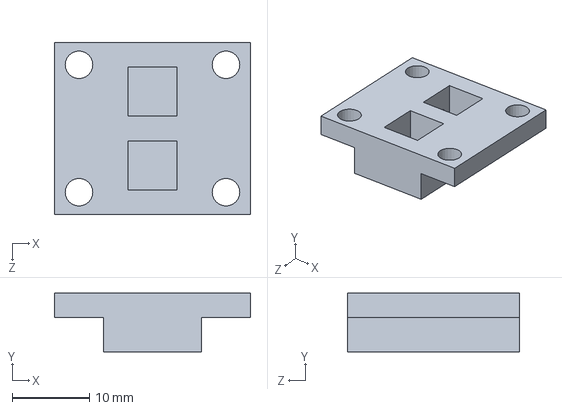
[picture p142: CAD file, 2023-07-05]
Hardware/CAD/Clock/Rack and Pinion Arm/Brush_Holder.SLDPRT
25.4 x 7.62 x 22.2 mm
