hudsonburke/SandsOfTime/Hardware/CAD/Clock/Arm_Assembly.PNG

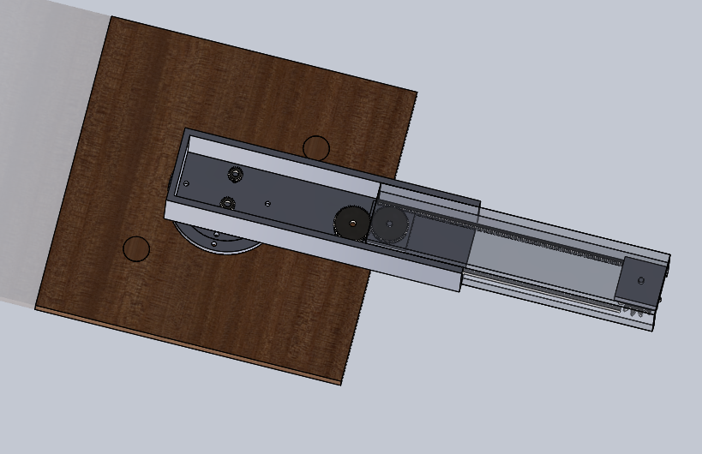
Hardware/CAD/Clock/Arm_Assembly.PNG
