hudsonburke/SandsOfTime/Hardware/CAD/Clock/Arm_Assembly_2.PNG

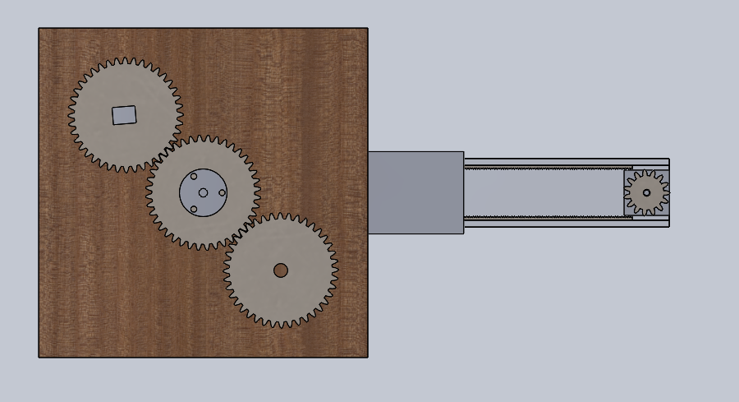
Hardware/CAD/Clock/Arm_Assembly_2.PNG
