hudsonburke/SandsOfTime/Hardware/CAD/Clock/HG_SubAssembly.PNG

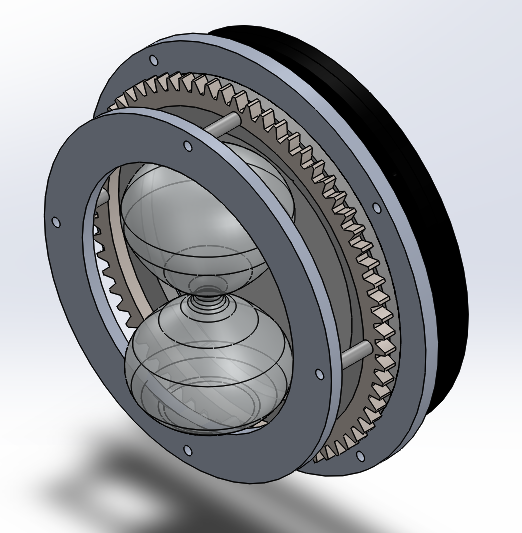
Hardware/CAD/Clock/HG_SubAssembly.PNG
