hudsonburke/SandsOfTime/Hardware/Wiring/LED board wiring.png

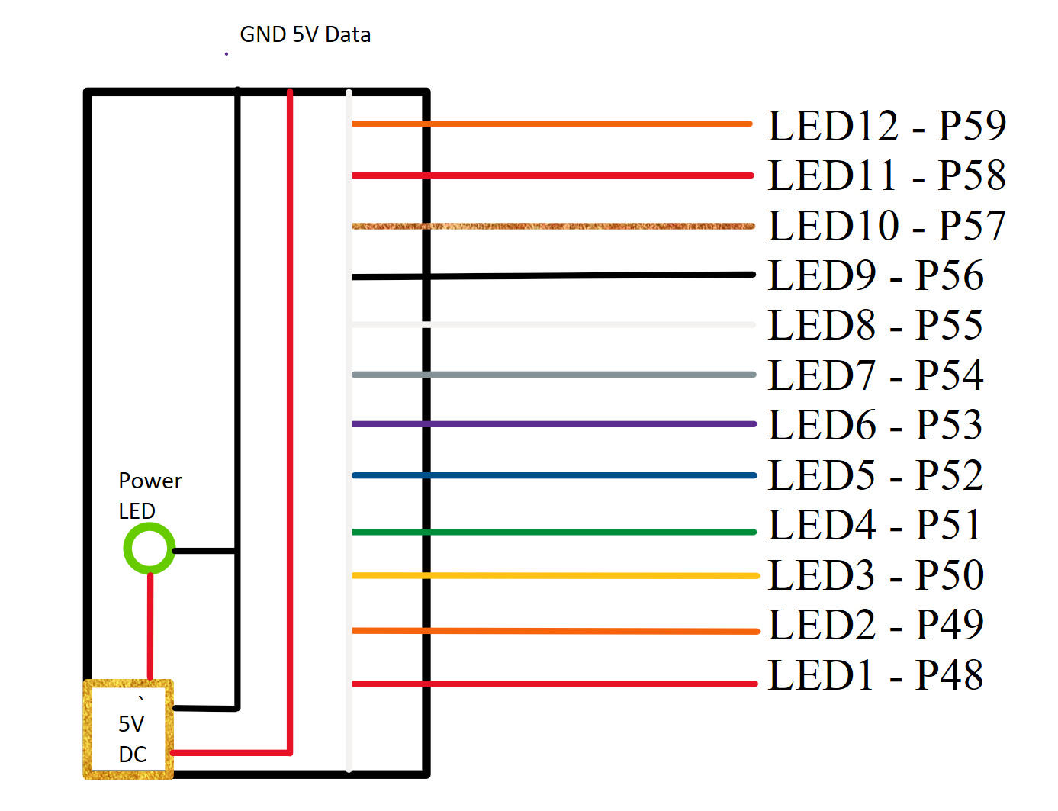
Hardware/Wiring/LED board wiring.png
