hudsonburke/SandsOfTime/Hardware/SandsOfTimePCB/SandsOfTimePCB.kicad_sch

## KiCad design Hardware/SandsOfTimePCB/SandsOfTimePCB.kicad_sch (2023-05-23)

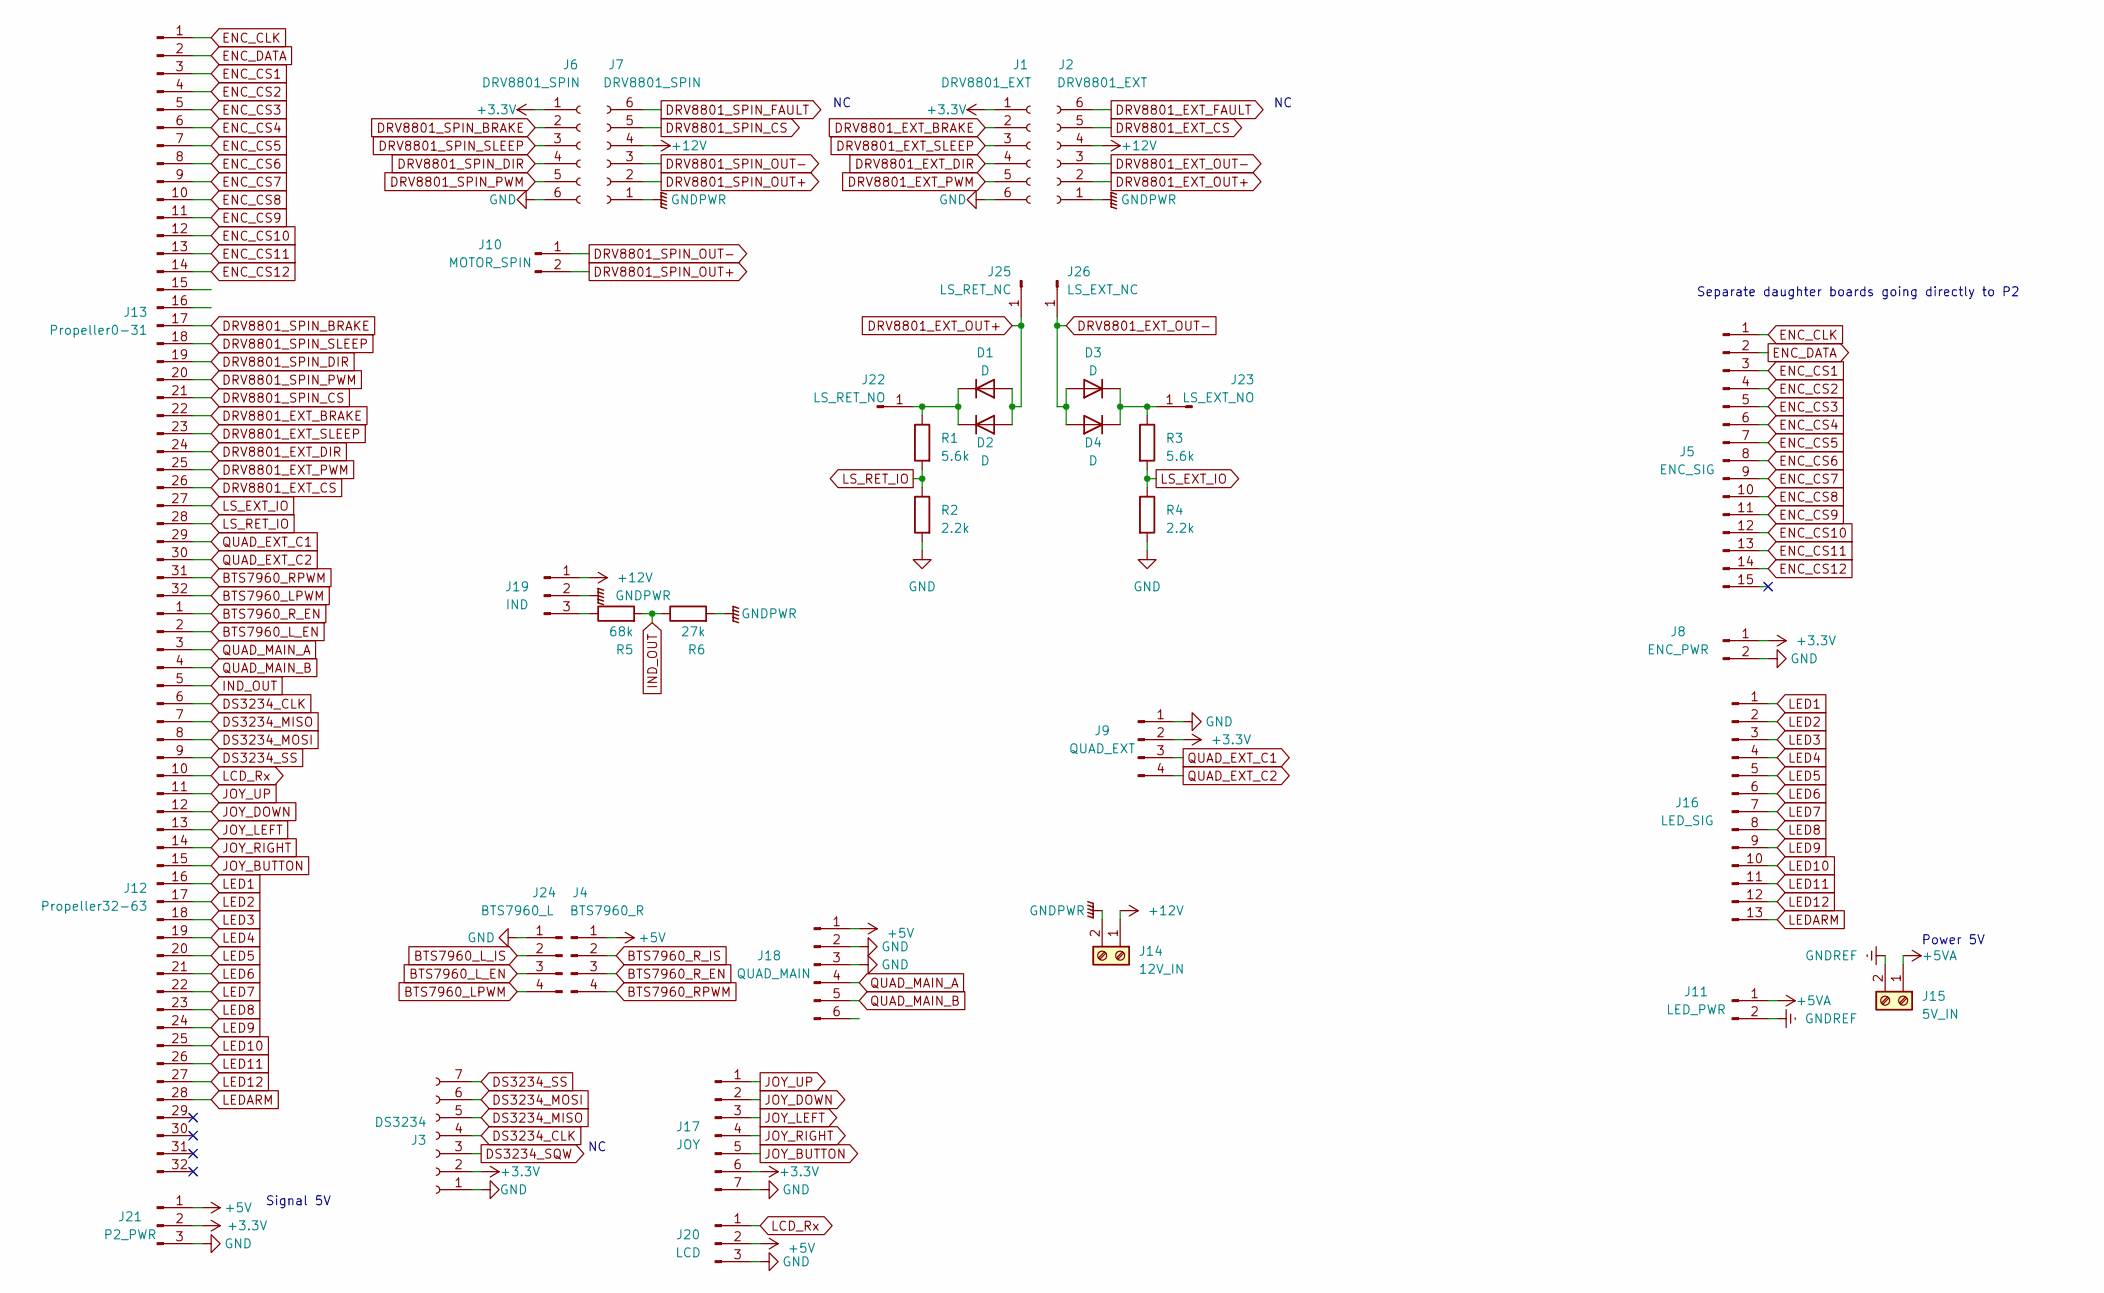
[picture p148: schematic SandsOfTimePCB.kicad_sch]

Parts:
D1, D2, D3, D4: D
J1, J2: DRV8801_EXT
J3: DS3234
J4: BTS7960_R
J5: ENC_SIG
J6, J7: DRV8801_SPIN
J8: ENC_PWR
J9: QUAD_EXT
J10: MOTOR_SPIN
J11: LED_PWR
J12: Propeller32-63
J13: Propeller0-31
J14: 12V_IN
J15: 5V_IN
J16: LED_SIG
J17: JOY
J18: QUAD_MAIN
J19: IND
J20: LCD
J21: P2_PWR
J22: LS_RET_NO
J23: LS_EXT_NO
J24: BTS7960_L
J25: LS_RET_NC
J26: LS_EXT_NC
R1, R3: 5.6k
R2, R4: 2.2k
R5: 68k
R6: 27k

Connections:
+3.3V: J1.1, J3.2, J6.1, J8.1, J9.2, J17.6, J21.2
+5V: J4.1, J18.1, J20.2, J21.1
+5VA: J11.1, J15.1
+12V: J2.4, J7.4, J14.1, J19.1
BTS7960_LPWM: J13.32, J24.4
BTS7960_L_EN: J12.2, J24.3
BTS7960_L_IS: J24.2
BTS7960_RPWM: J4.4, J13.31
BTS7960_R_EN: J4.3, J12.1
BTS7960_R_IS: J4.2
DRV8801_EXT_BRAKE: J1.2, J13.22
DRV8801_EXT_CS: J2.5, J13.26
DRV8801_EXT_DIR: J1.4, J13.24
DRV8801_EXT_FAULT: J2.6
DRV8801_EXT_OUT+: D1.2 (A), D2.2 (A), J2.2, J25.1
DRV8801_EXT_OUT-: D3.2 (A), D4.2 (A), J2.3, J26.1
DRV8801_EXT_PWM: J1.5, J13.25
DRV8801_EXT_SLEEP: J1.3, J13.23
DRV8801_SPIN_BRAKE: J6.2, J13.17
DRV8801_SPIN_CS: J7.5, J13.21
DRV8801_SPIN_DIR: J6.4, J13.19
DRV8801_SPIN_FAULT: J7.6
DRV8801_SPIN_OUT+: J7.2, J10.2
DRV8801_SPIN_OUT-: J7.3, J10.1
DRV8801_SPIN_PWM: J6.5, J13.20
DRV8801_SPIN_SLEEP: J6.3, J13.18
DS3234_CLK: J3.4, J12.6
DS3234_MISO: J3.5, J12.7
DS3234_MOSI: J3.6, J12.8
DS3234_SQW: J3.3
DS3234_SS: J3.7, J12.9
ENC_CLK: J5.1, J13.1
ENC_CS1: J5.3, J13.3
ENC_CS2: J5.4, J13.4
ENC_CS3: J5.5, J13.5
ENC_CS4: J5.6, J13.6
ENC_CS5: J5.7, J13.7
ENC_CS6: J5.8, J13.8
ENC_CS7: J5.9, J13.9
ENC_CS8: J5.10, J13.10
ENC_CS9: J5.11, J13.11
ENC_CS10: J5.12, J13.12
ENC_CS11: J5.13, J13.13
ENC_CS12: J5.14, J13.14
ENC_DATA: J5.2, J13.2
GND: J1.6, J3.1, J6.6, J8.2, J9.1, J17.7, J18.2, J18.3, J20.3, J21.3, J24.1, R2.2, R4.2
GNDPWR: J2.1, J7.1, J14.2, J19.2, R6.2
GNDREF: J11.2, J15.2
IND_OUT: J12.5, R5.2, R6.1
JOY_BUTTON: J12.15, J17.5
JOY_DOWN: J12.12, J17.2
JOY_LEFT: J12.13, J17.3
JOY_RIGHT: J12.14, J17.4
JOY_UP: J12.11, J17.1
LCD_Rx: J12.10, J20.1
LED1: J12.16, J16.1
LED2: J12.17, J16.2
LED3: J12.18, J16.3
LED4: J12.19, J16.4
LED5: J12.20, J16.5
LED6: J12.21, J16.6
LED7: J12.22, J16.7
LED8: J12.23, J16.8
LED9: J12.24, J16.9
LED10: J12.25, J16.10
LED11: J12.26, J16.11
LED12: J12.27, J16.12
LEDARM: J12.28, J16.13
LS_EXT_IO: J13.27, R3.2, R4.1
LS_RET_IO: J13.28, R1.2, R2.1
unnamed: D1.1 (K), D2.1 (K), J22.1, R1.1
unnamed: D3.1 (K), D4.1 (K), J23.1, R3.1
unnamed: J19.3, R5.1
QUAD_EXT_C1: J9.3, J13.29
QUAD_EXT_C2: J9.4, J13.30
QUAD_MAIN_A: J12.3, J18.4
QUAD_MAIN_B: J12.4, J18.5

Notes on the sheet:
Separate daughter boards going directly to P2
Signal 5V
Power 5V
